attu0/benzene/assets/images/amcl_localization/rviz_particle_filtter.png

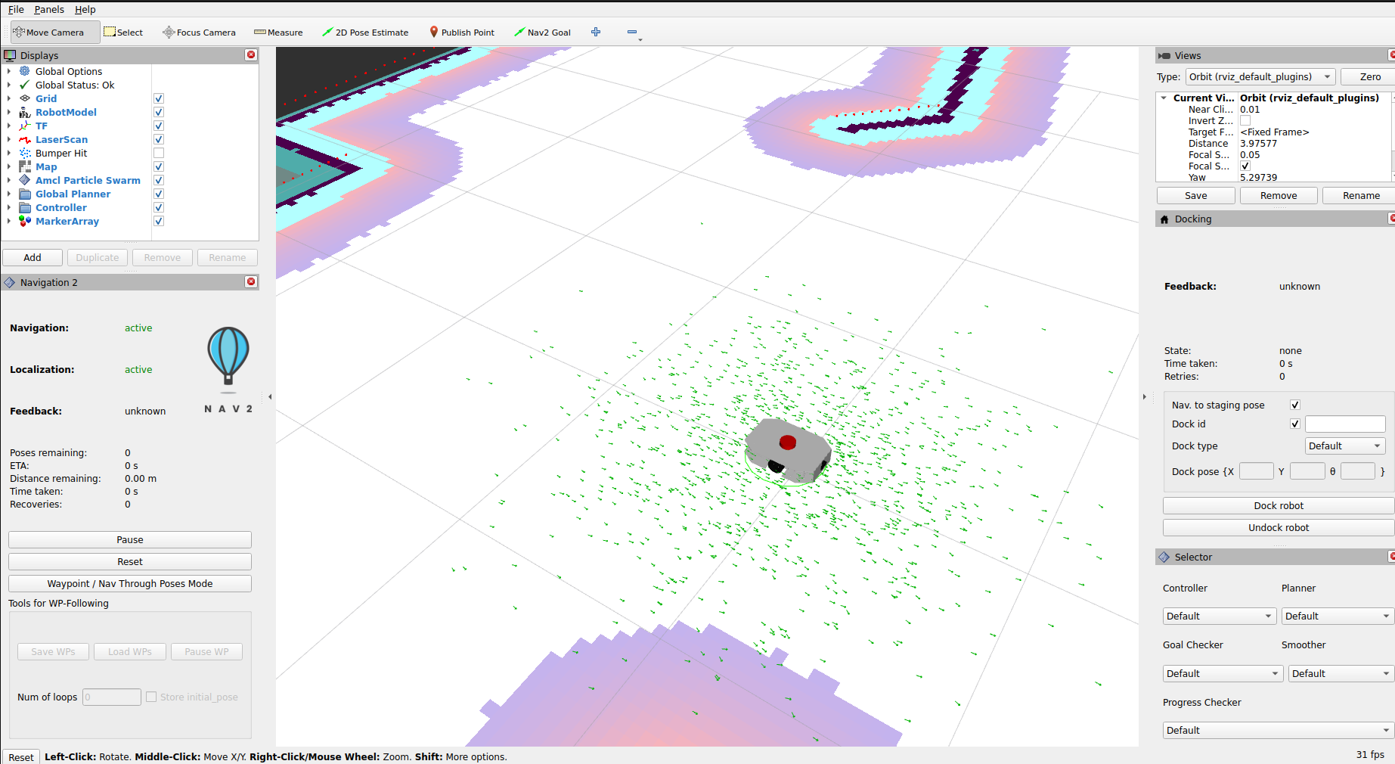
assets/images/amcl_localization/rviz_particle_filtter.png
