attu0/benzene/assets/images/amcl_localization/warehosue_particle.png

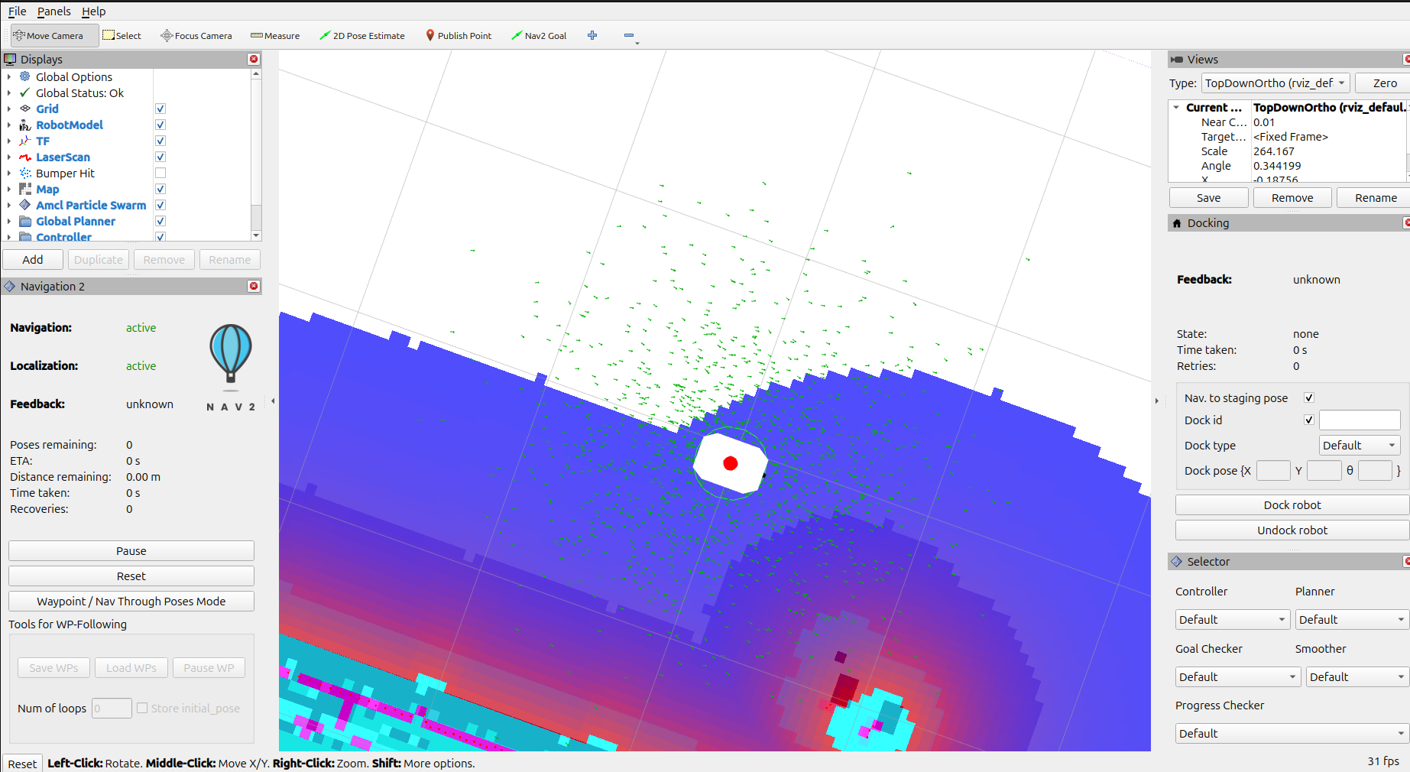
assets/images/amcl_localization/warehosue_particle.png
