attu0/benzene/assets/images/benzene/benzene.png

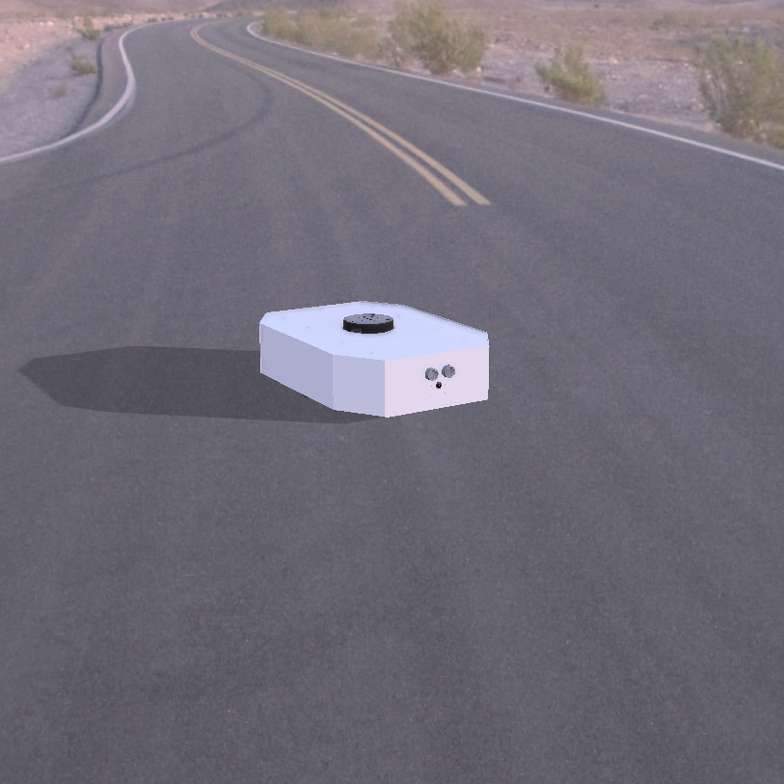
assets/images/benzene/benzene.png
