attu0/benzene/assets/images/benzene/benzene_2.png

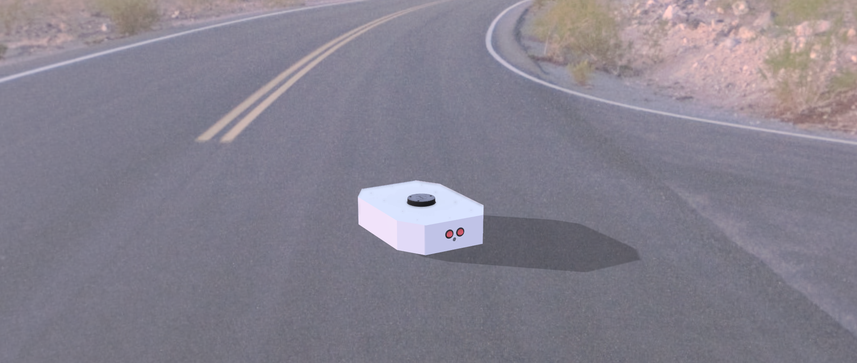
assets/images/benzene/benzene_2.png
