attu0/benzene/assets/images/benzene/benzene_2_back.png

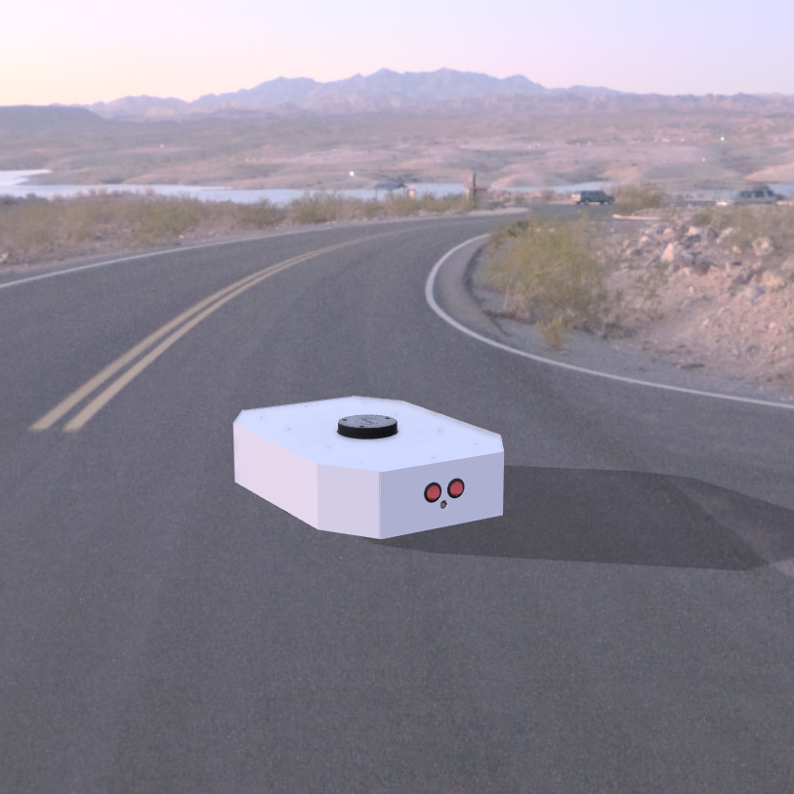
assets/images/benzene/benzene_2_back.png
