attu0/benzene/assets/images/benzene/benzene_2_solid.png

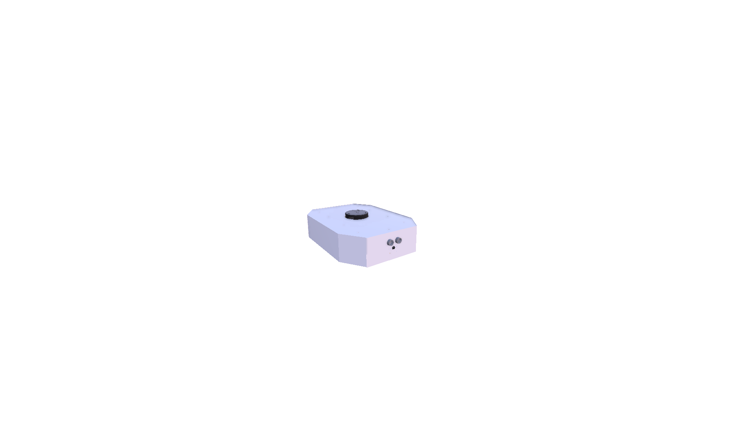
assets/images/benzene/benzene_2_solid.png
