attu0/benzene/assets/images/benzene/urdf_view_in_rviz.png

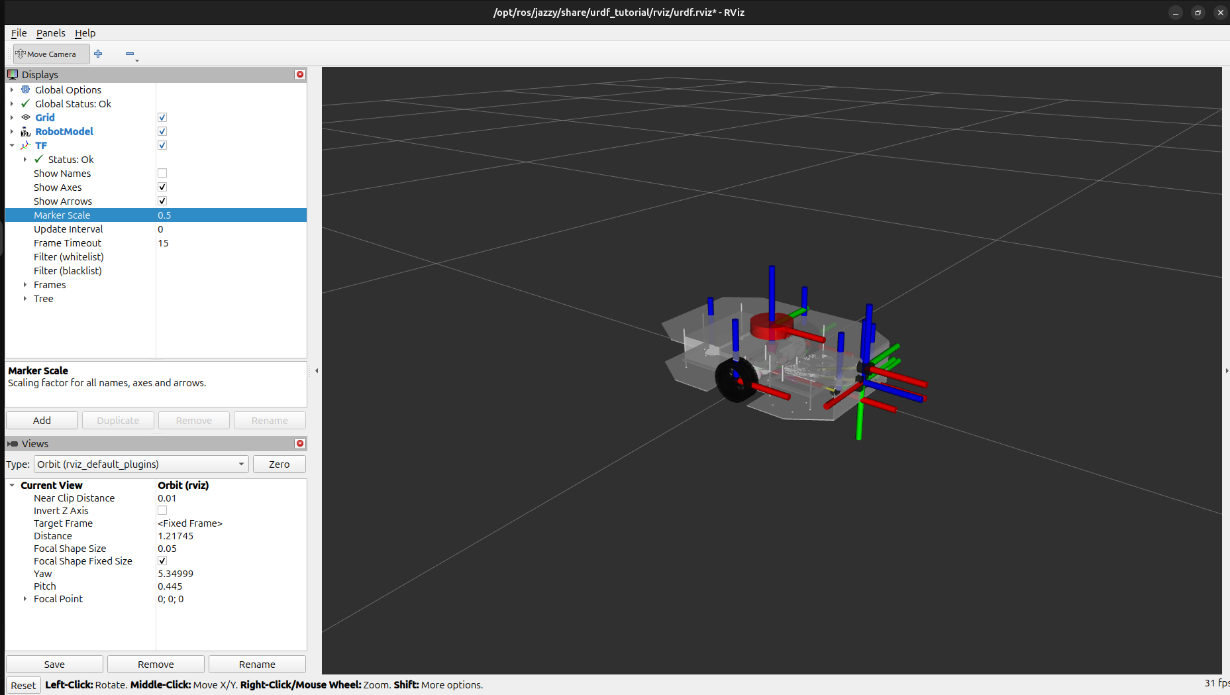
assets/images/benzene/urdf_view_in_rviz.png
