attu0/benzene/assets/images/circuit/arduino.png

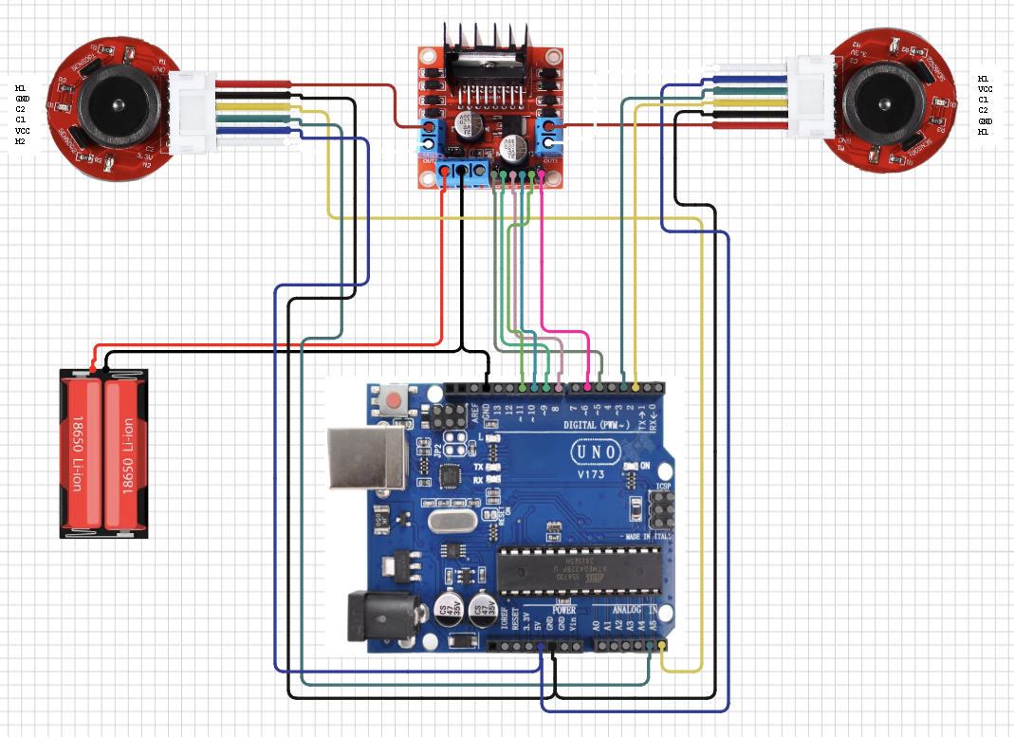
assets/images/circuit/arduino.png
