attu0/benzene/assets/images/circuit/complete_circuit.png

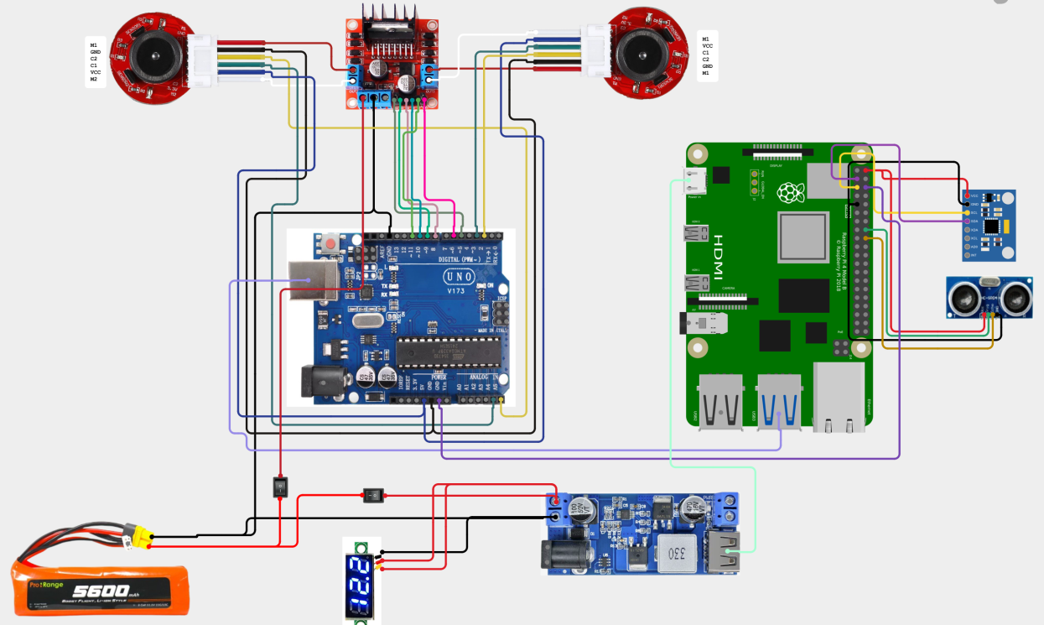
assets/images/circuit/complete_circuit.png
