attu0/benzene/assets/images/circuit/flow.jpg

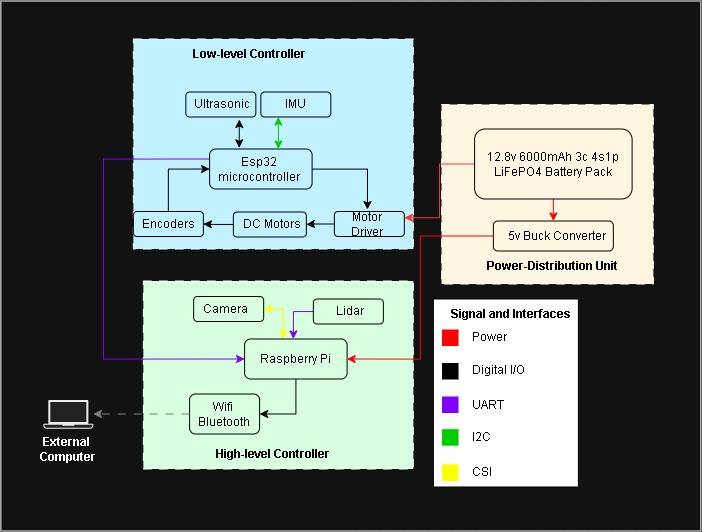
assets/images/circuit/flow.jpg
