attu0/benzene/assets/images/circuit/pi.png

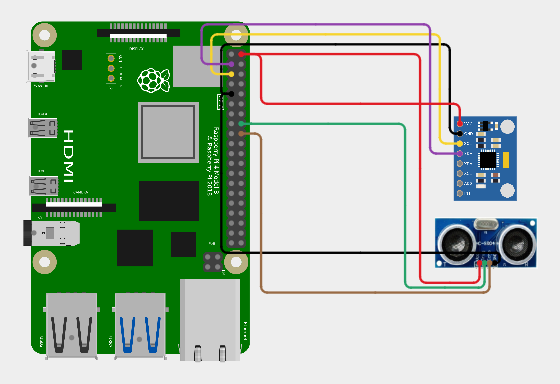
assets/images/circuit/pi.png
