attu0/benzene/assets/images/dagger/line_detection.png

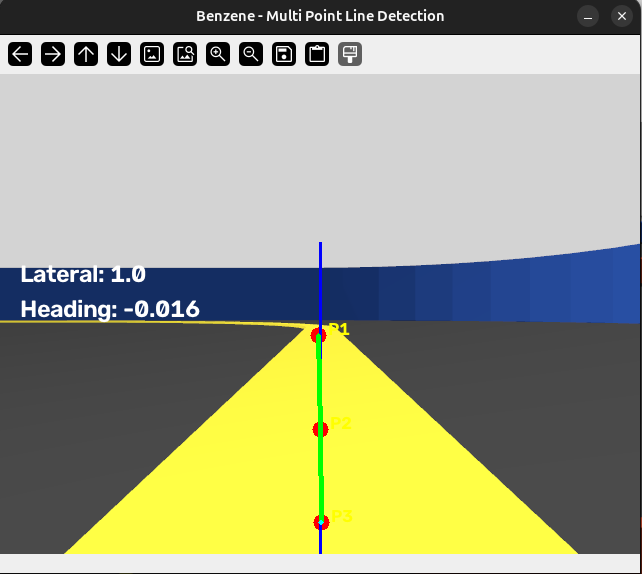
assets/images/dagger/line_detection.png
