attu0/benzene/assets/images/dagger/masking.png

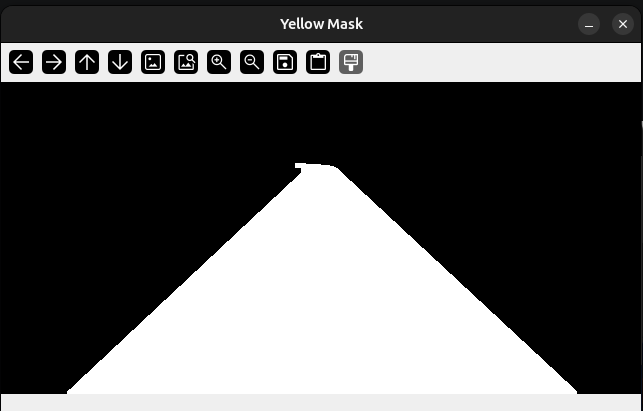
assets/images/dagger/masking.png
