attu0/benzene/assets/images/dagger/rviz2.png

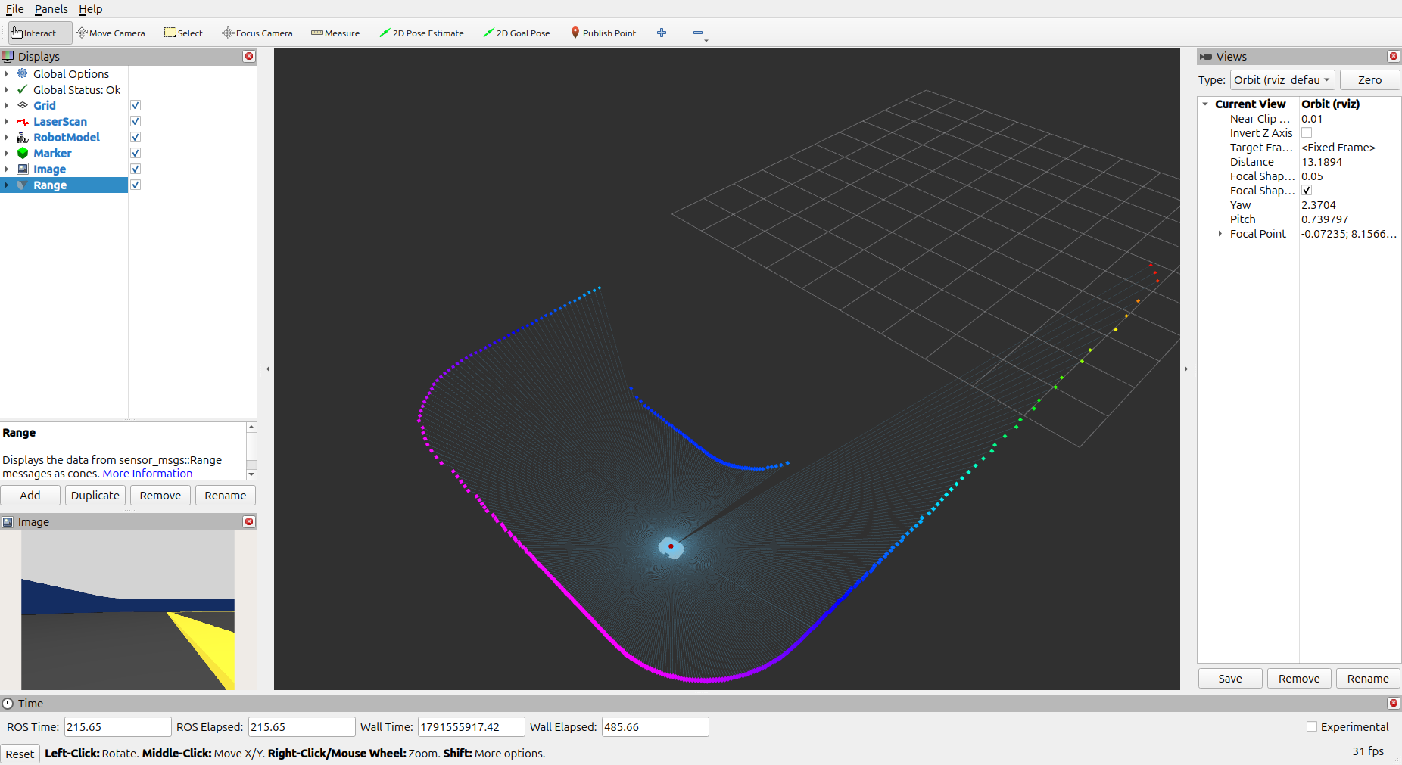
assets/images/dagger/rviz2.png
