attu0/benzene/assets/images/dagger/rviz.png

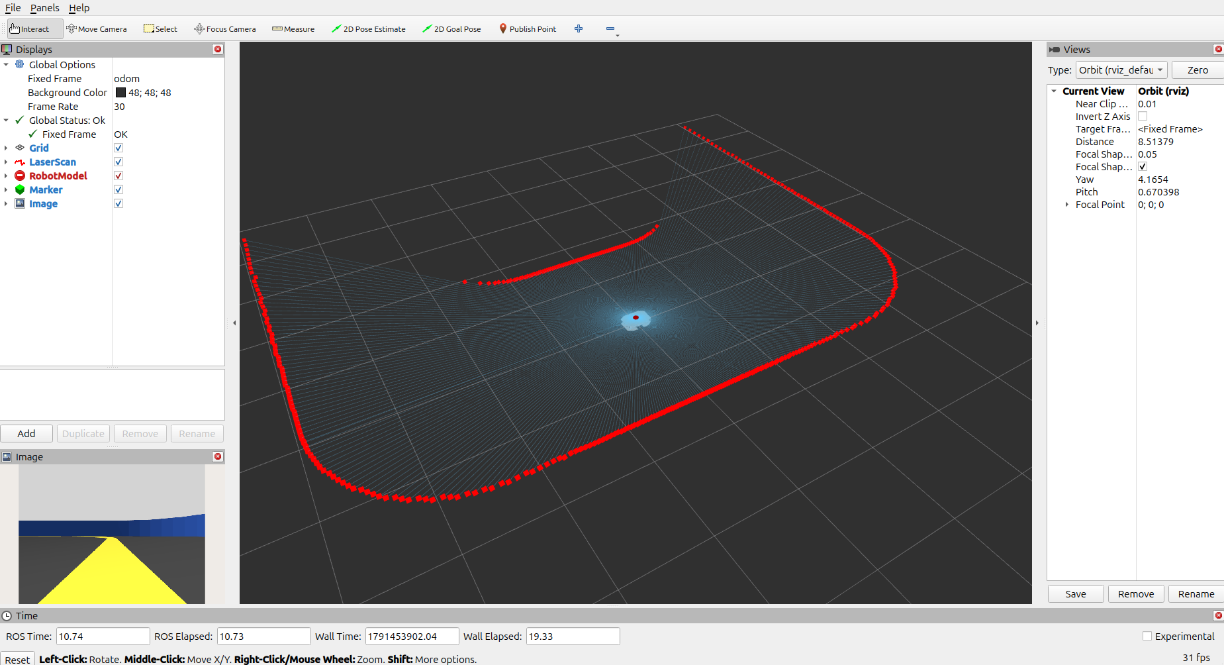
assets/images/dagger/rviz.png
