attu0/benzene/assets/images/dagger/world.png

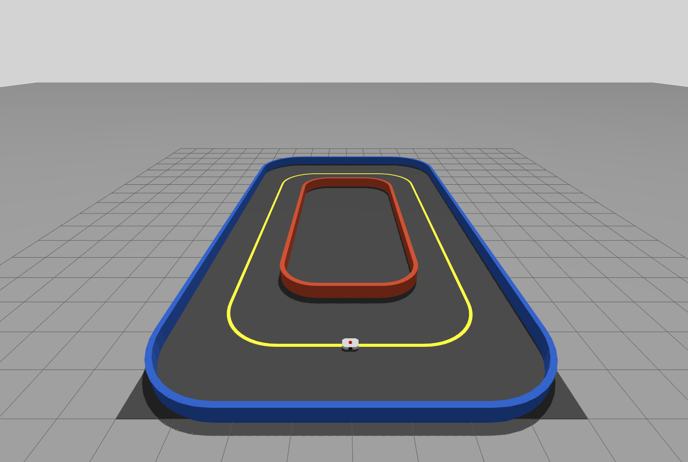
assets/images/dagger/world.png
