attu0/benzene/assets/images/docking/april_tag_align.png

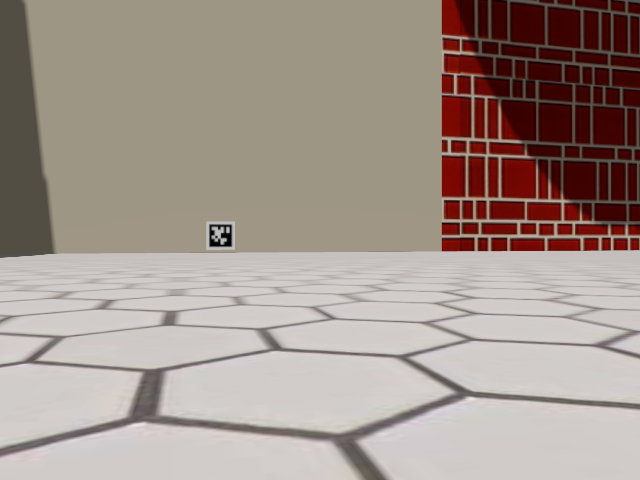
assets/images/docking/april_tag_align.png
