attu0/benzene/assets/images/docking/bot_view.png

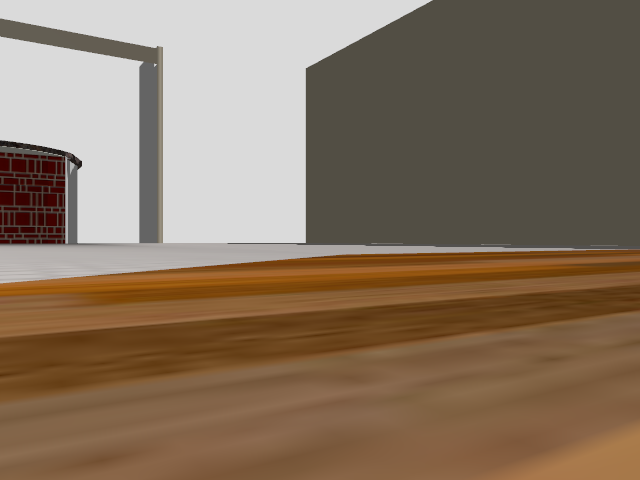
assets/images/docking/bot_view.png
