attu0/benzene/assets/images/docking/docking.png

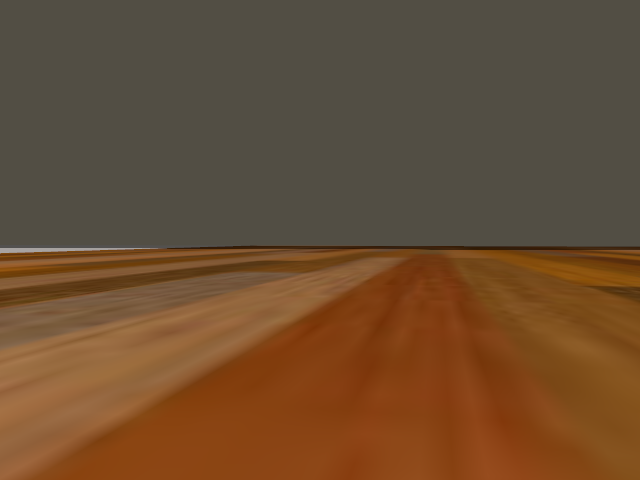
assets/images/docking/docking.png
