attu0/benzene/assets/images/docking/finding_april_tag.png

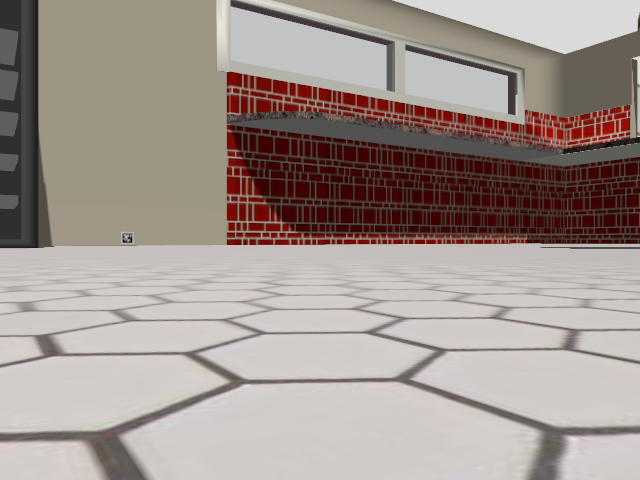
assets/images/docking/finding_april_tag.png
