attu0/benzene/assets/images/docking/gz1.png

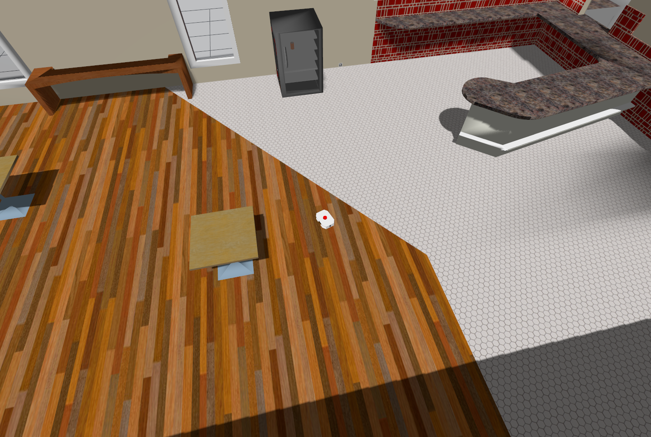
assets/images/docking/gz1.png
