attu0/benzene/assets/images/docking/gz2.png

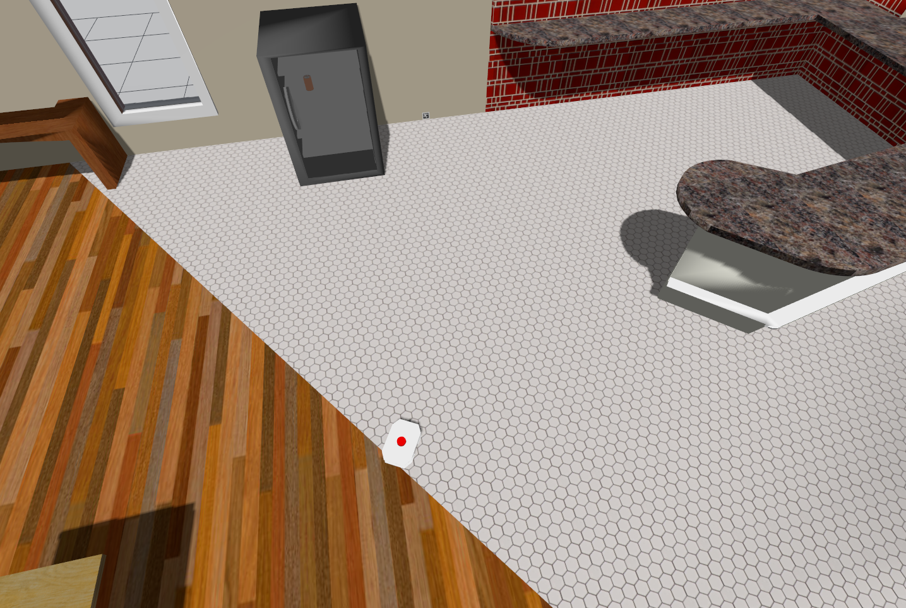
assets/images/docking/gz2.png
