attu0/benzene/assets/images/docking/gz3.png

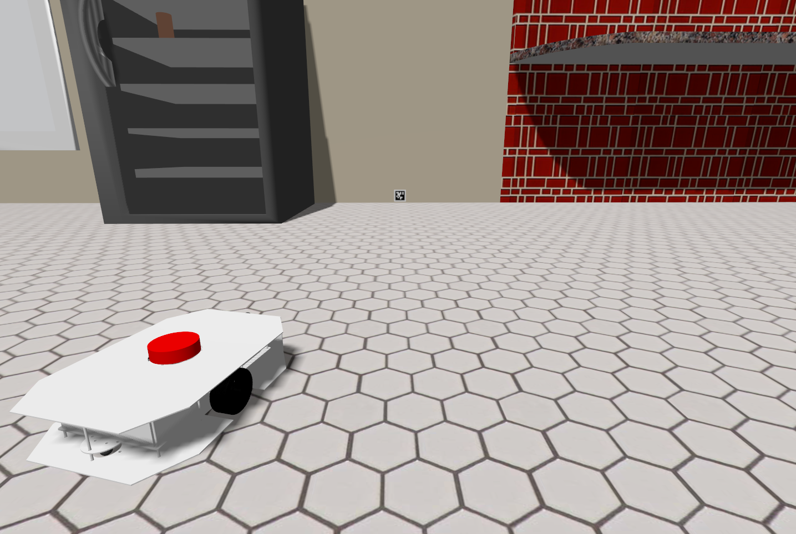
assets/images/docking/gz3.png
