attu0/benzene/assets/images/docking/gz4.png

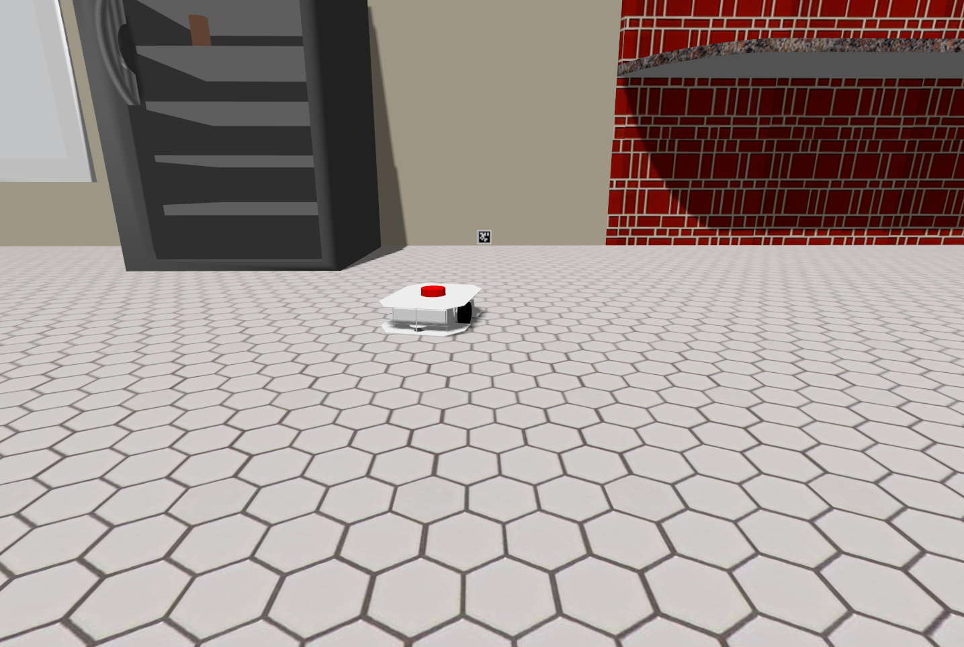
assets/images/docking/gz4.png
