attu0/benzene/assets/images/docking/image.png

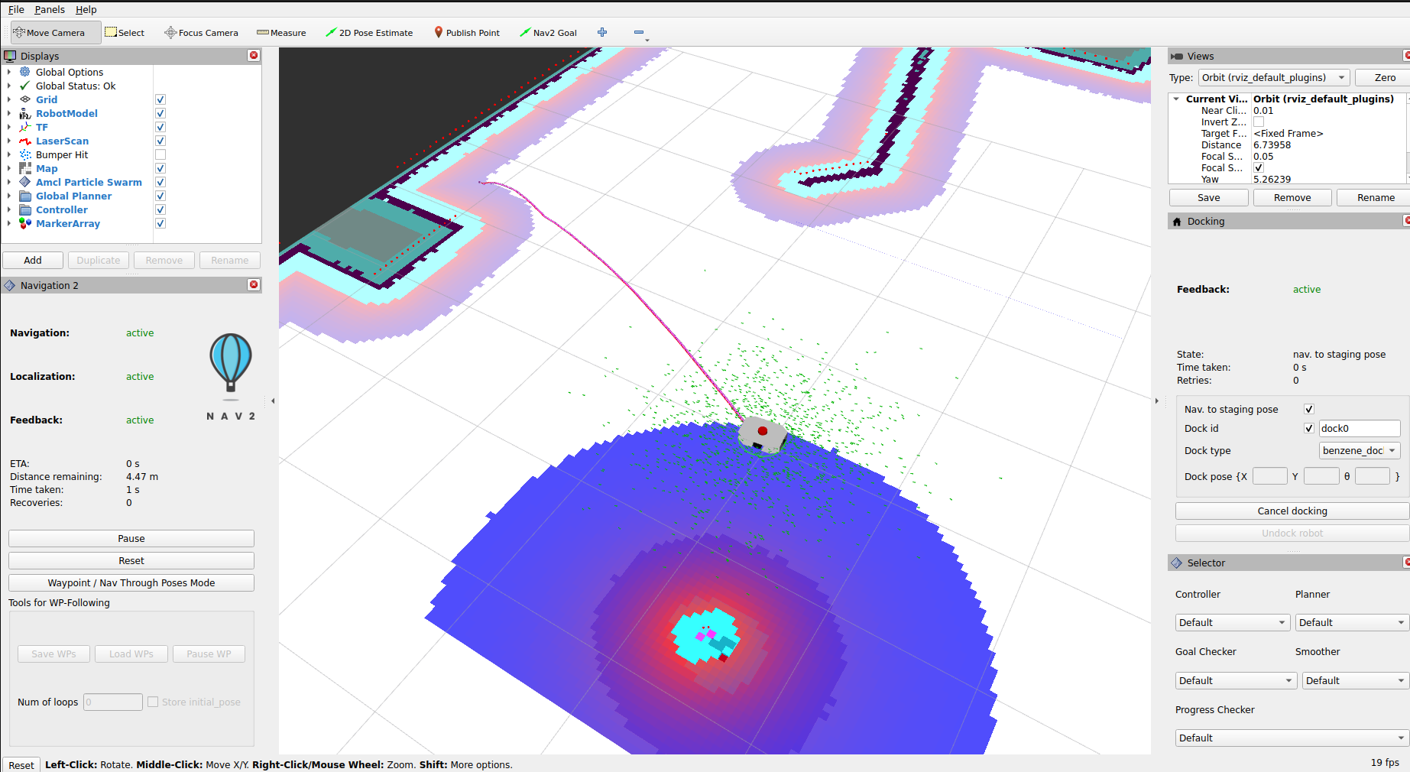
assets/images/docking/image.png
