attu0/benzene/assets/images/docking/reached.png

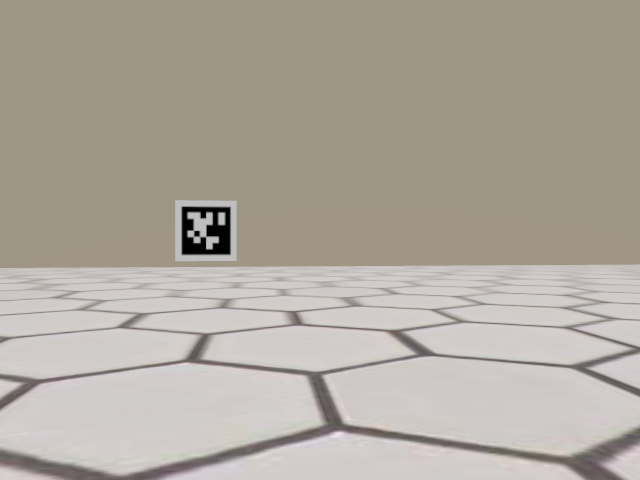
assets/images/docking/reached.png
