attu0/benzene/assets/images/laser_cut/base_plate.jpg

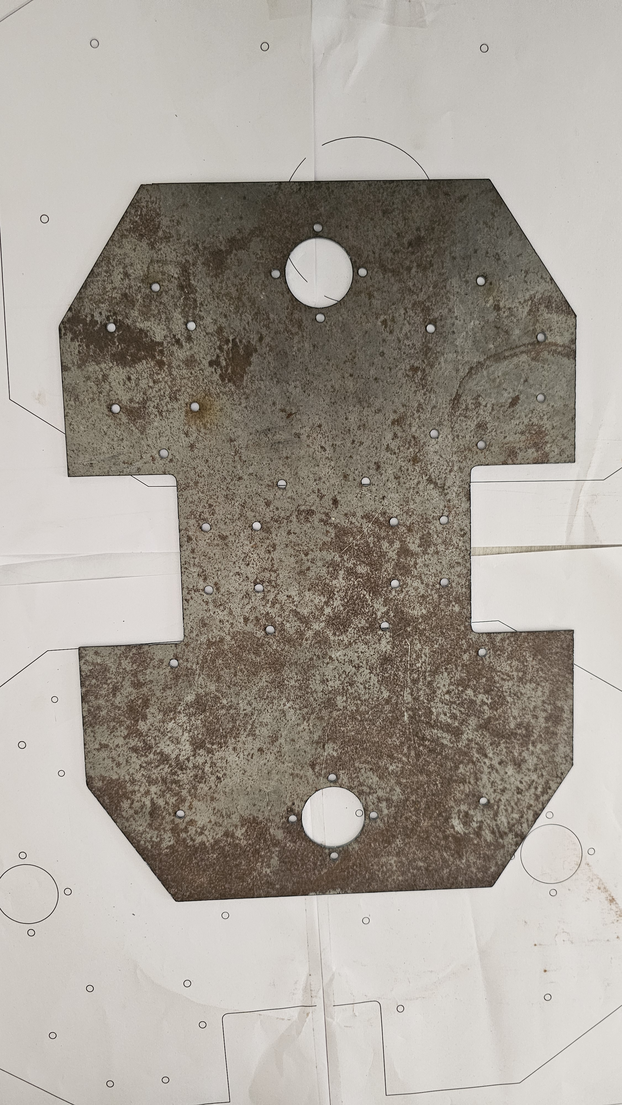
assets/images/laser_cut/base_plate.jpg
