attu0/benzene/assets/images/laser_cut/caster_plates.jpg

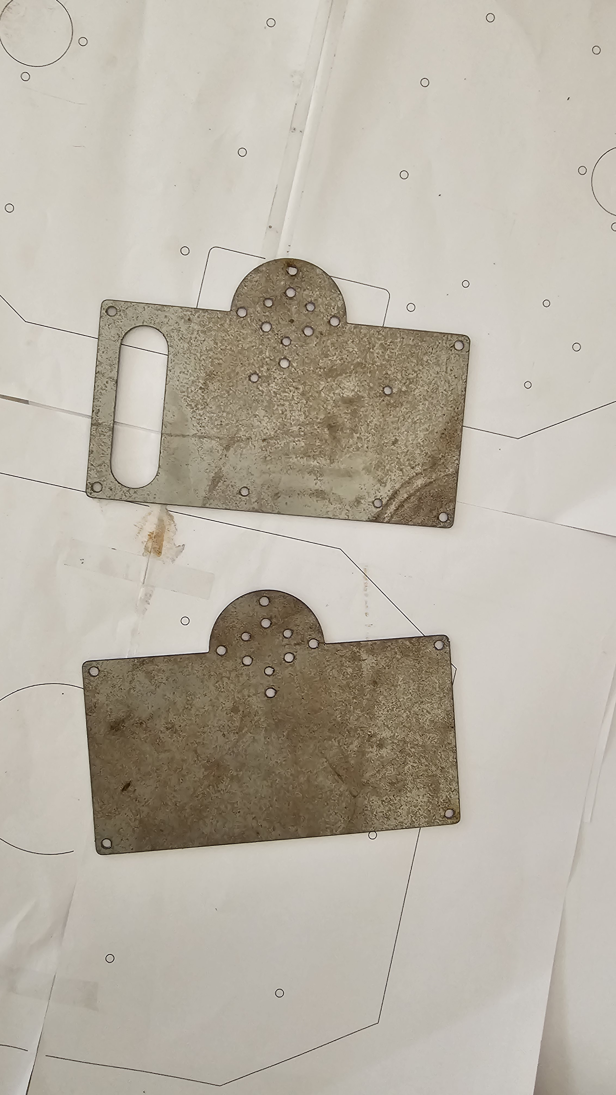
assets/images/laser_cut/caster_plates.jpg
