attu0/benzene/assets/images/laser_cut/corner_panels.jpg

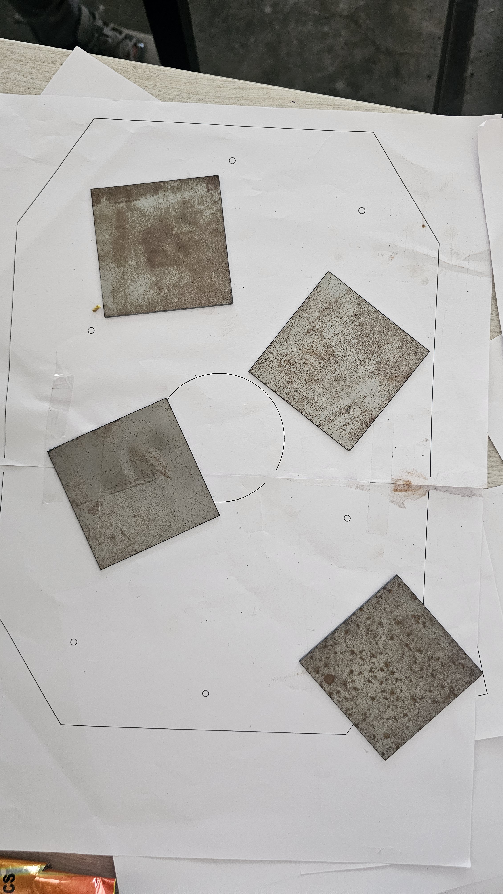
assets/images/laser_cut/corner_panels.jpg
