attu0/benzene/assets/images/laser_cut/fro_rear_plates.jpg

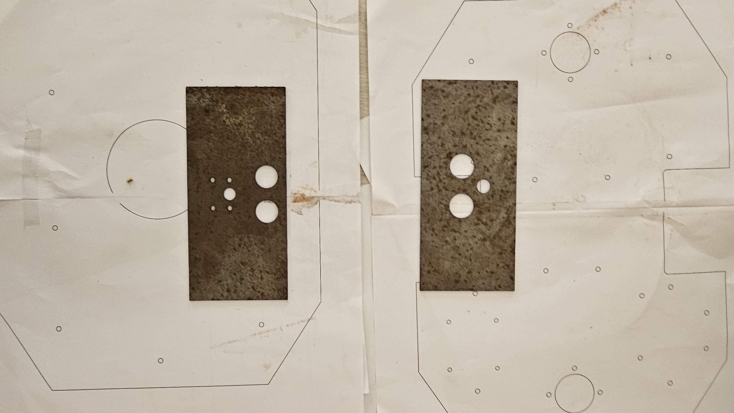
assets/images/laser_cut/fro_rear_plates.jpg
