attu0/benzene/assets/images/laser_cut/side_plates.jpg

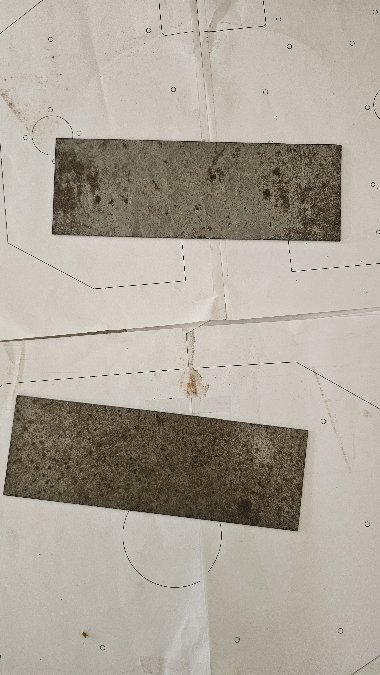
assets/images/laser_cut/side_plates.jpg
