attu0/benzene/assets/images/laser_cut/top_plate.jpg

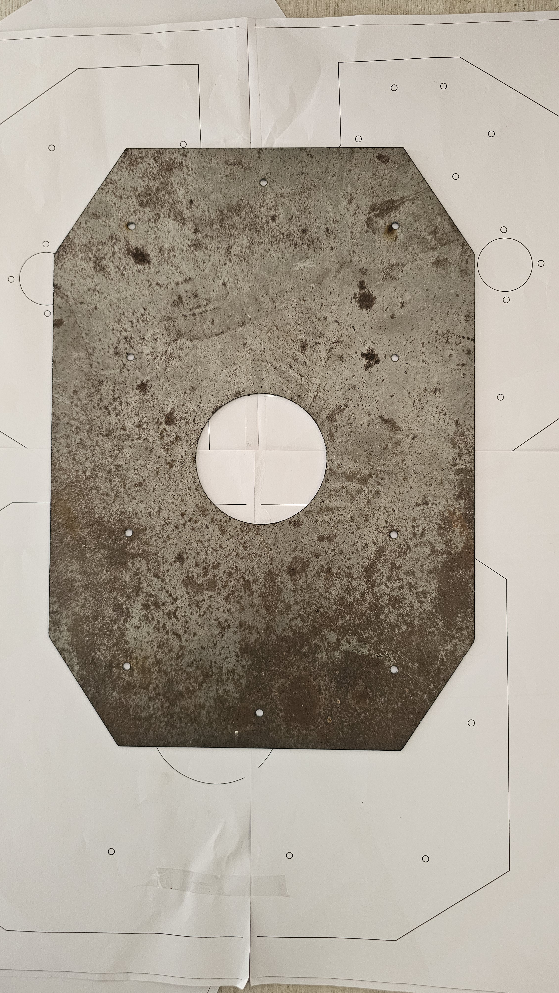
assets/images/laser_cut/top_plate.jpg
