attu0/benzene/assets/images/maps/cafe.png

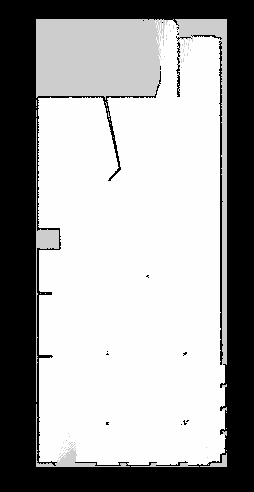
assets/images/maps/cafe.png
