attu0/benzene/assets/images/maps/office.png

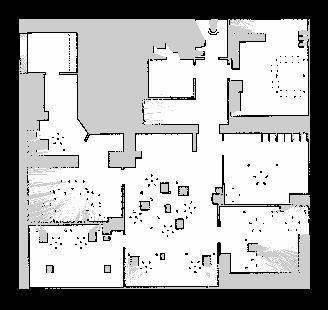
assets/images/maps/office.png
