attu0/benzene/assets/images/maps/warehouse.png

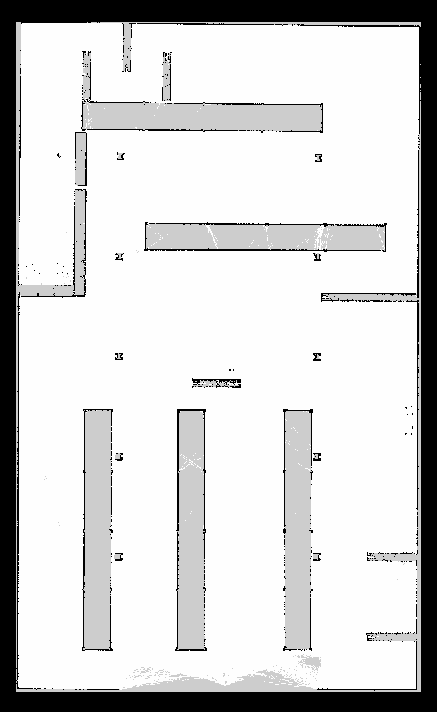
assets/images/maps/warehouse.png
