attu0/benzene/assets/images/nav2/gz_cafe.png

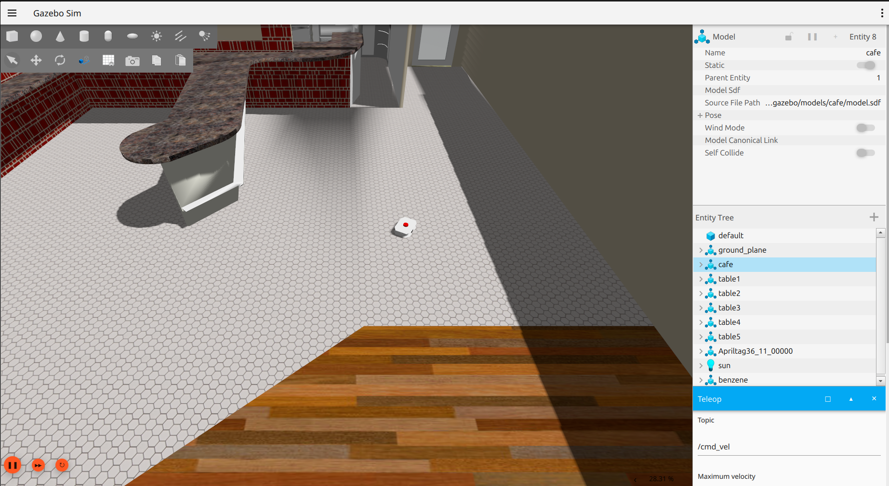
assets/images/nav2/gz_cafe.png
