attu0/benzene/assets/images/nav2/gz_warehouse.png

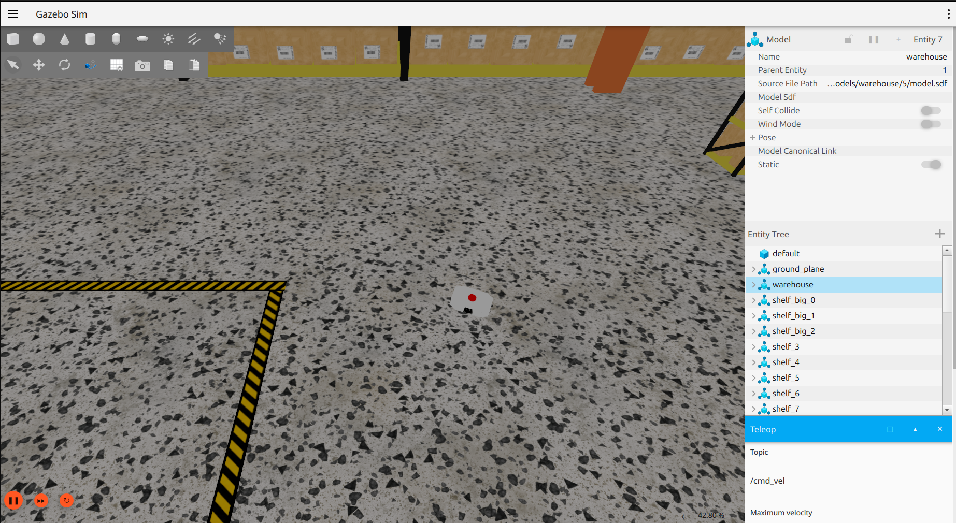
assets/images/nav2/gz_warehouse.png
