attu0/benzene/assets/images/nav2/rviz_cafe.png

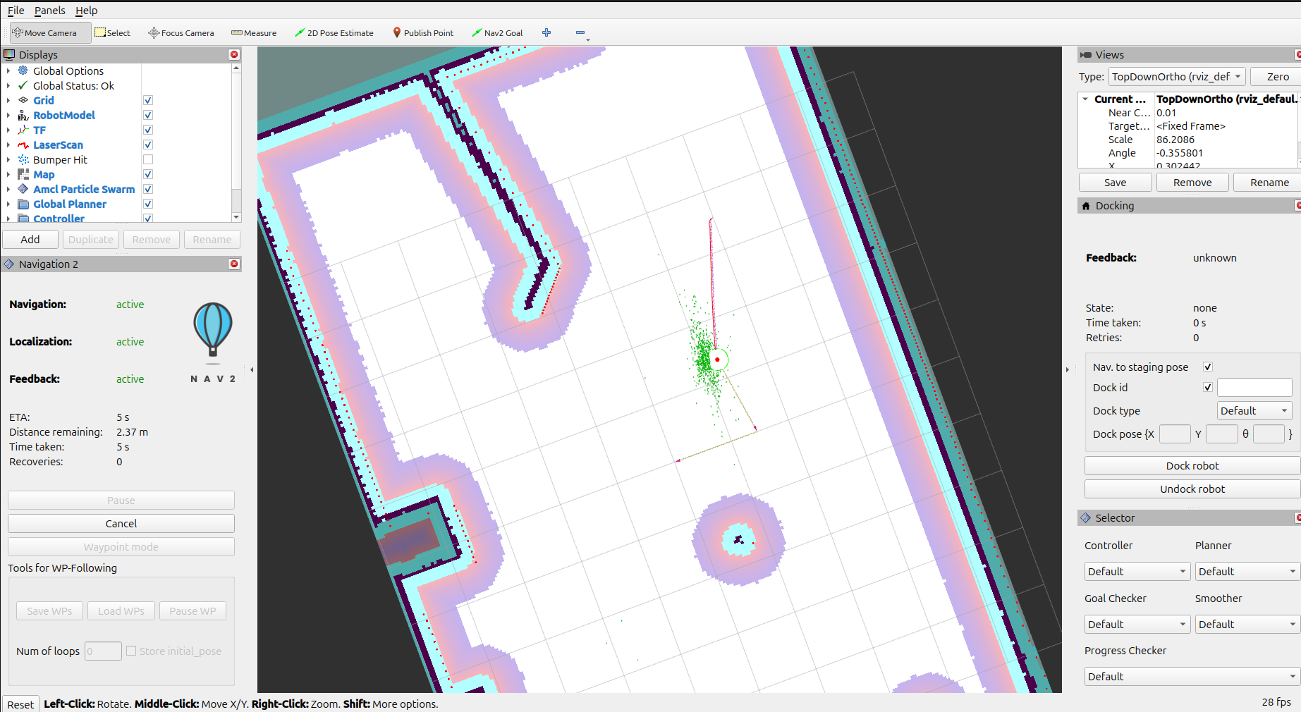
assets/images/nav2/rviz_cafe.png
