attu0/benzene/assets/images/nav2/rviz_office2.png

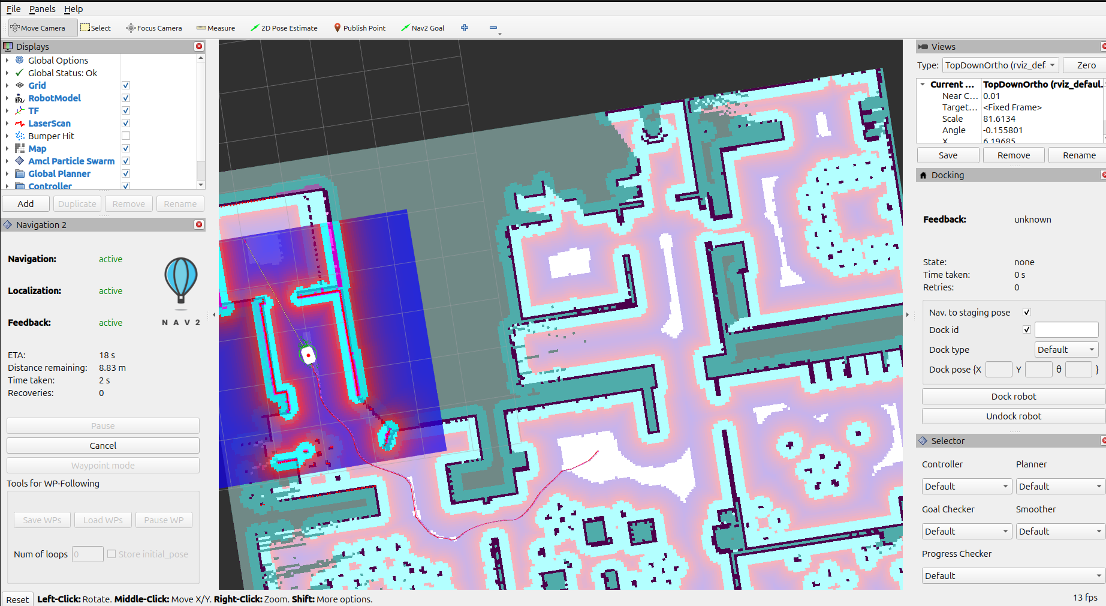
assets/images/nav2/rviz_office2.png
