attu0/benzene/assets/images/nav2/rviz_office.png

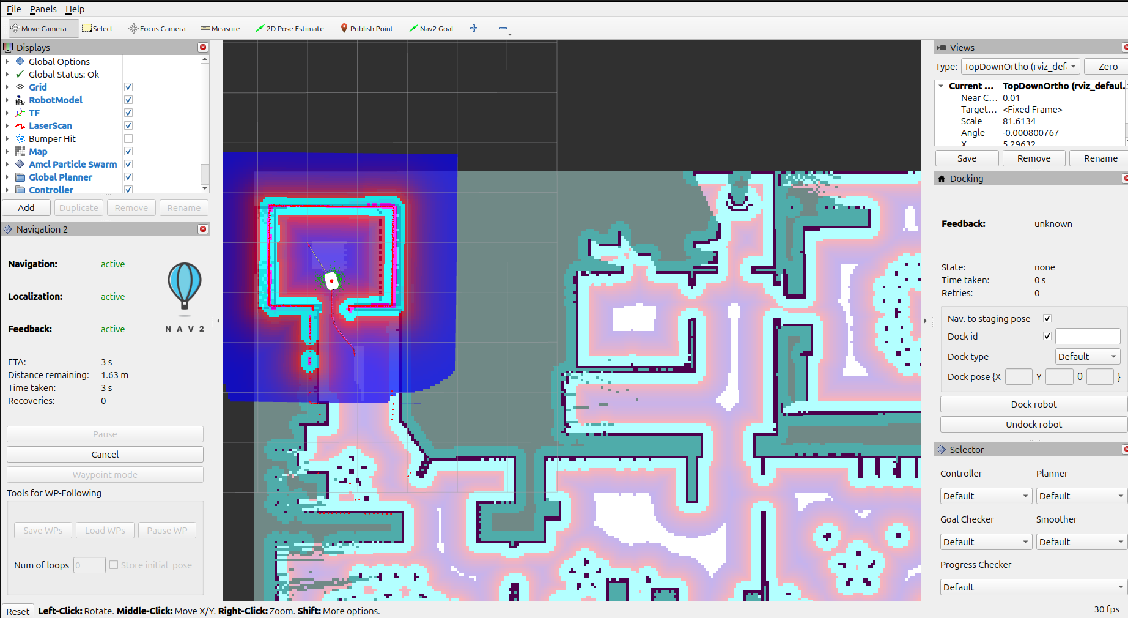
assets/images/nav2/rviz_office.png
