attu0/benzene/assets/images/nav2/rviz_warehosue.png

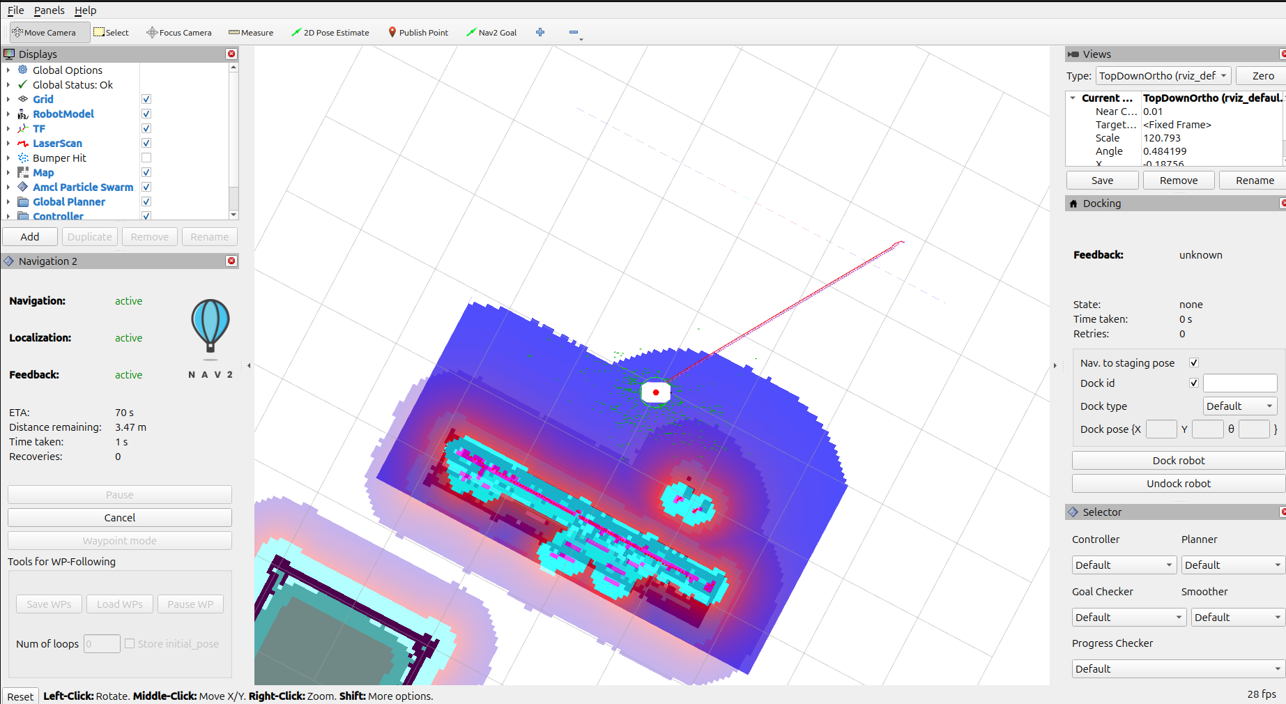
assets/images/nav2/rviz_warehosue.png
