attu0/benzene/assets/images/real_bot/benzene.jpeg

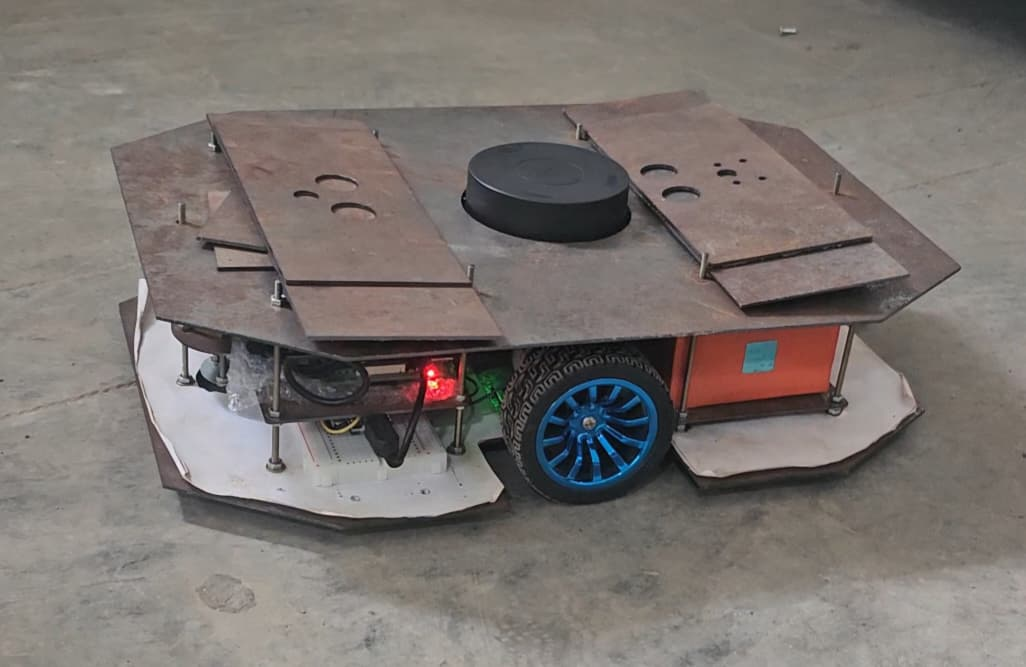
assets/images/real_bot/benzene.jpeg
