attu0/benzene/assets/images/real_bot/ckt_named.png

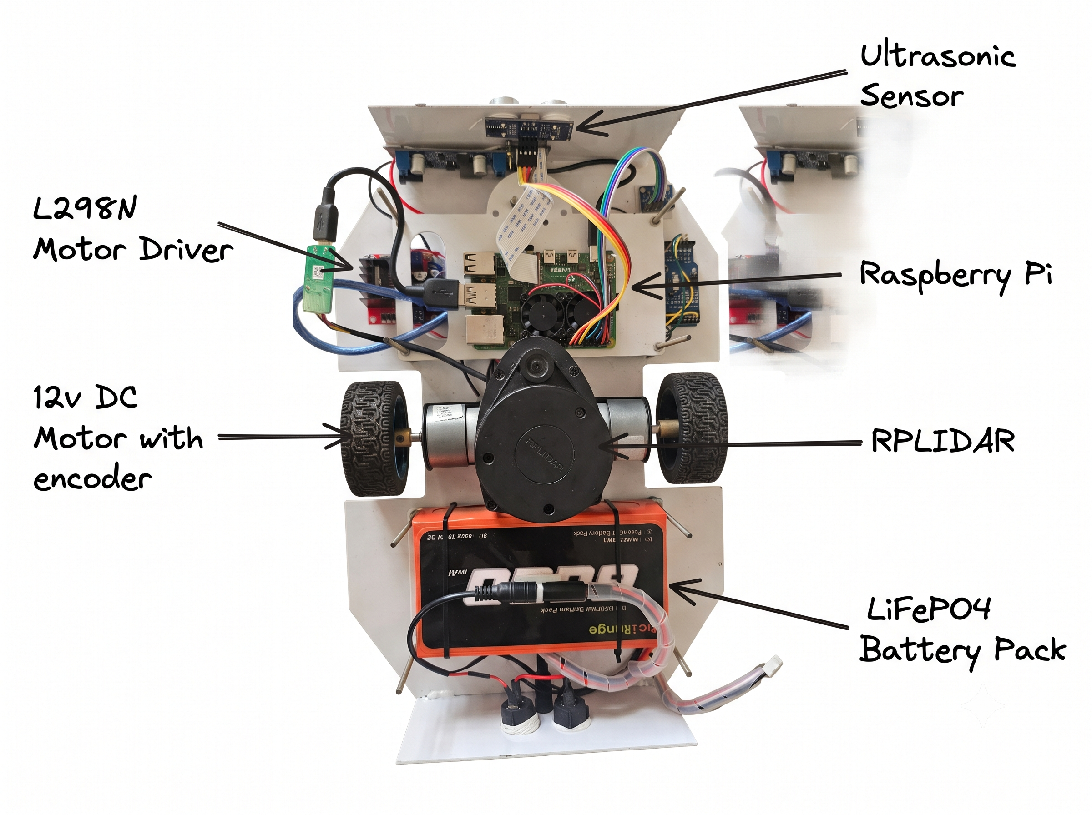
assets/images/real_bot/ckt_named.png
