attu0/benzene/assets/images/real_bot/front1.jpg

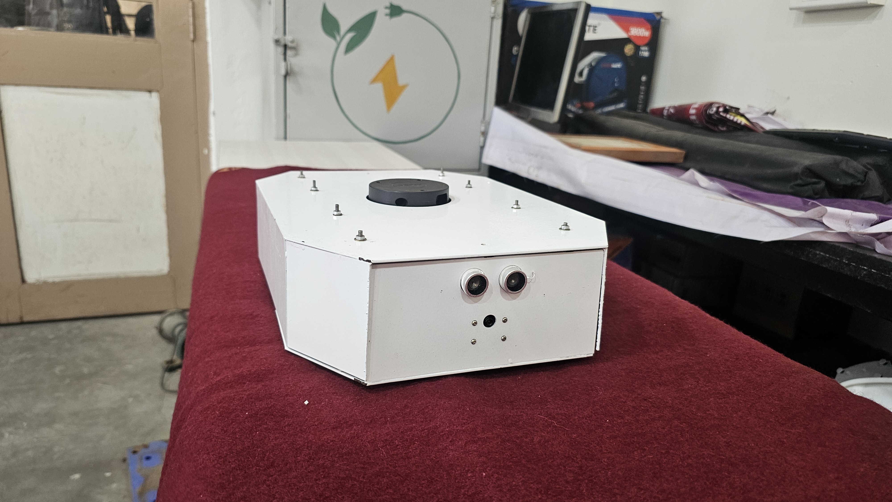
assets/images/real_bot/front1.jpg
