attu0/benzene/assets/images/real_bot/front2.jpg

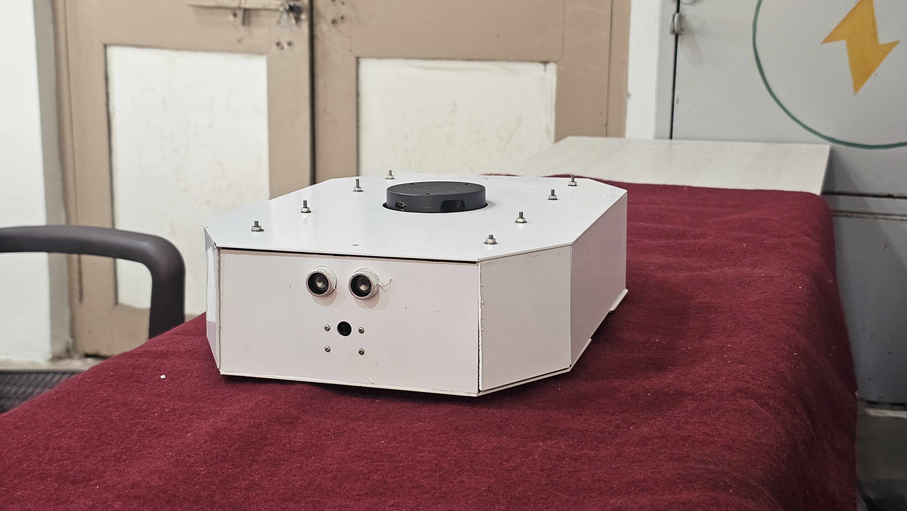
assets/images/real_bot/front2.jpg
