attu0/benzene/assets/images/real_bot/front3.jpg

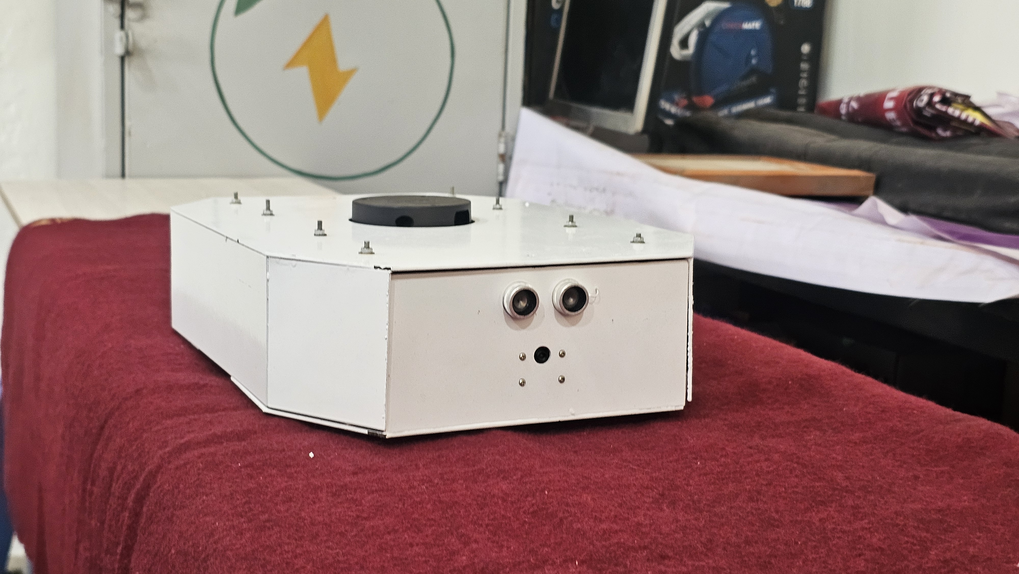
assets/images/real_bot/front3.jpg
