attu0/benzene/assets/images/real_bot/internal.jpg

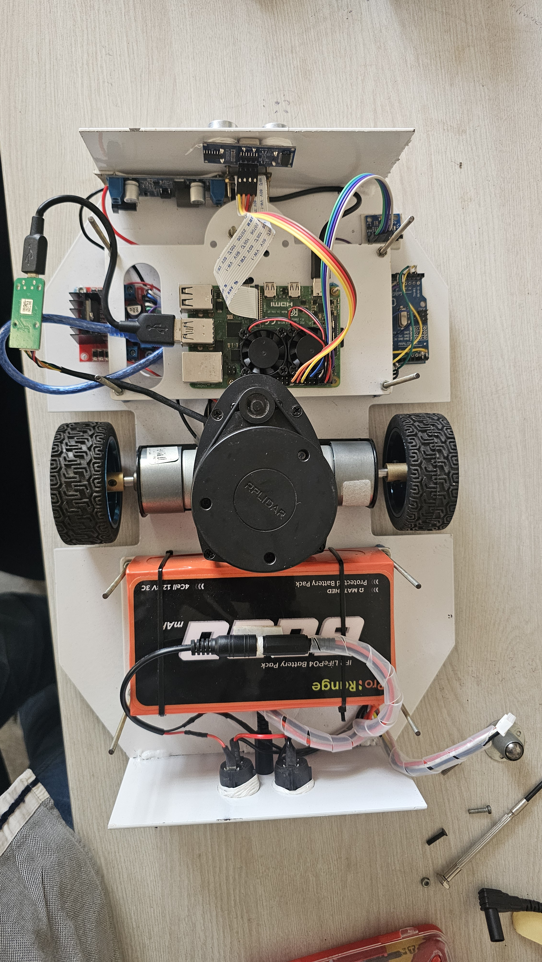
assets/images/real_bot/internal.jpg
