attu0/benzene/assets/images/real_bot/rear1.jpg

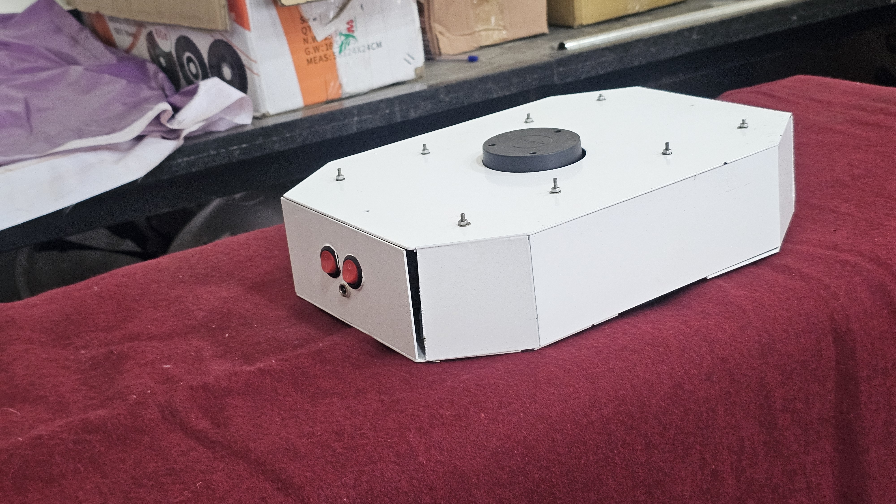
assets/images/real_bot/rear1.jpg
