attu0/benzene/assets/images/real_bot/rear2.jpg

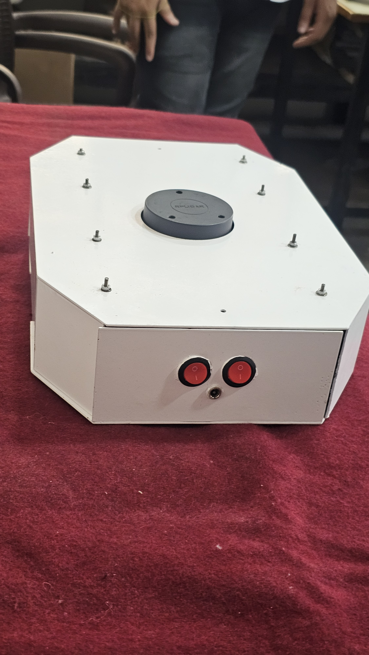
assets/images/real_bot/rear2.jpg
