attu0/benzene/assets/images/self_explore/cafe2.png

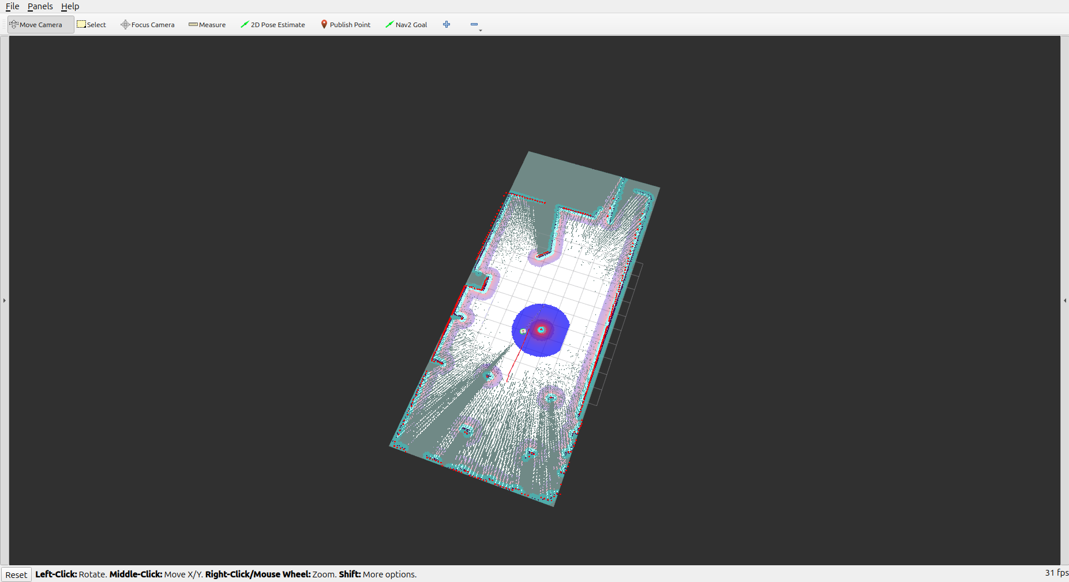
assets/images/self_explore/cafe2.png
