attu0/benzene/assets/images/self_explore/cafe.png

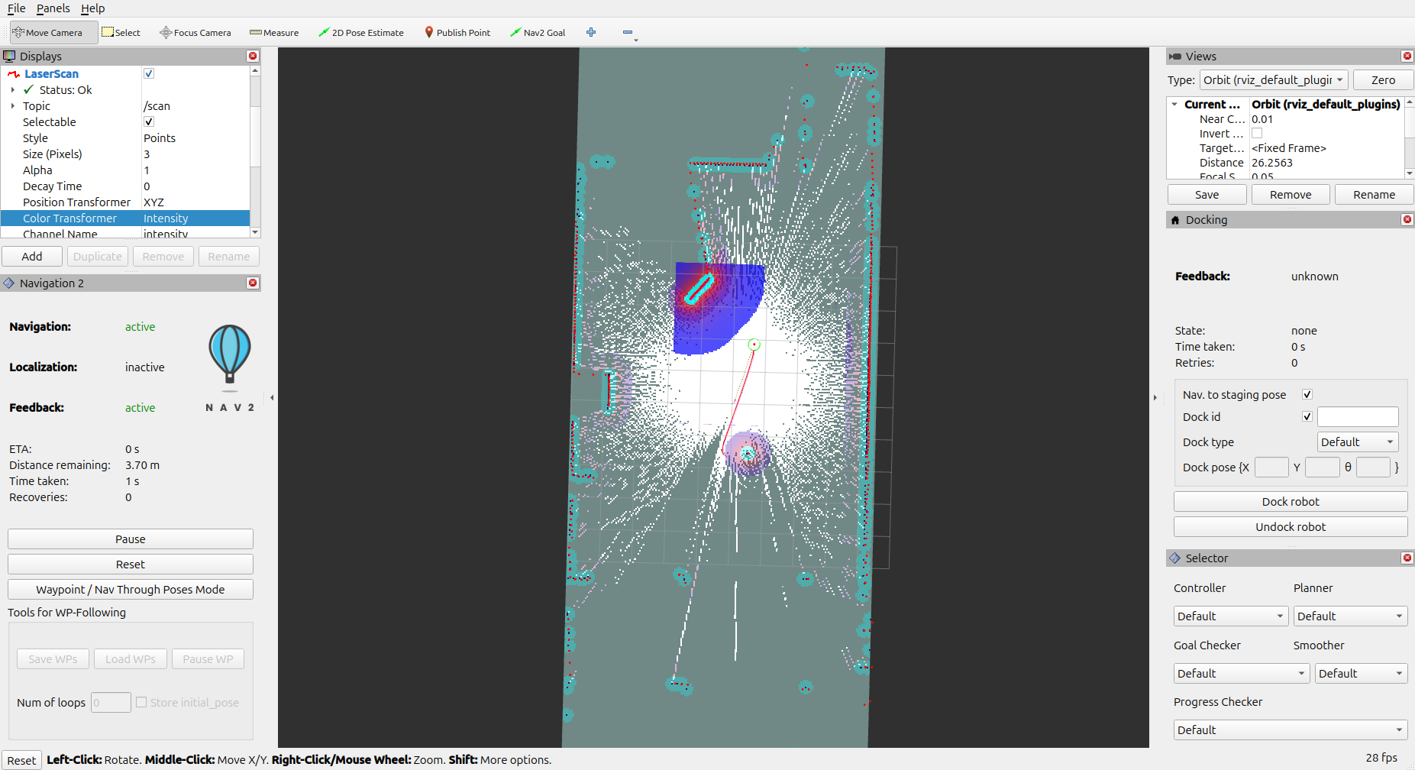
assets/images/self_explore/cafe.png
