attu0/benzene/assets/images/self_explore/office.png

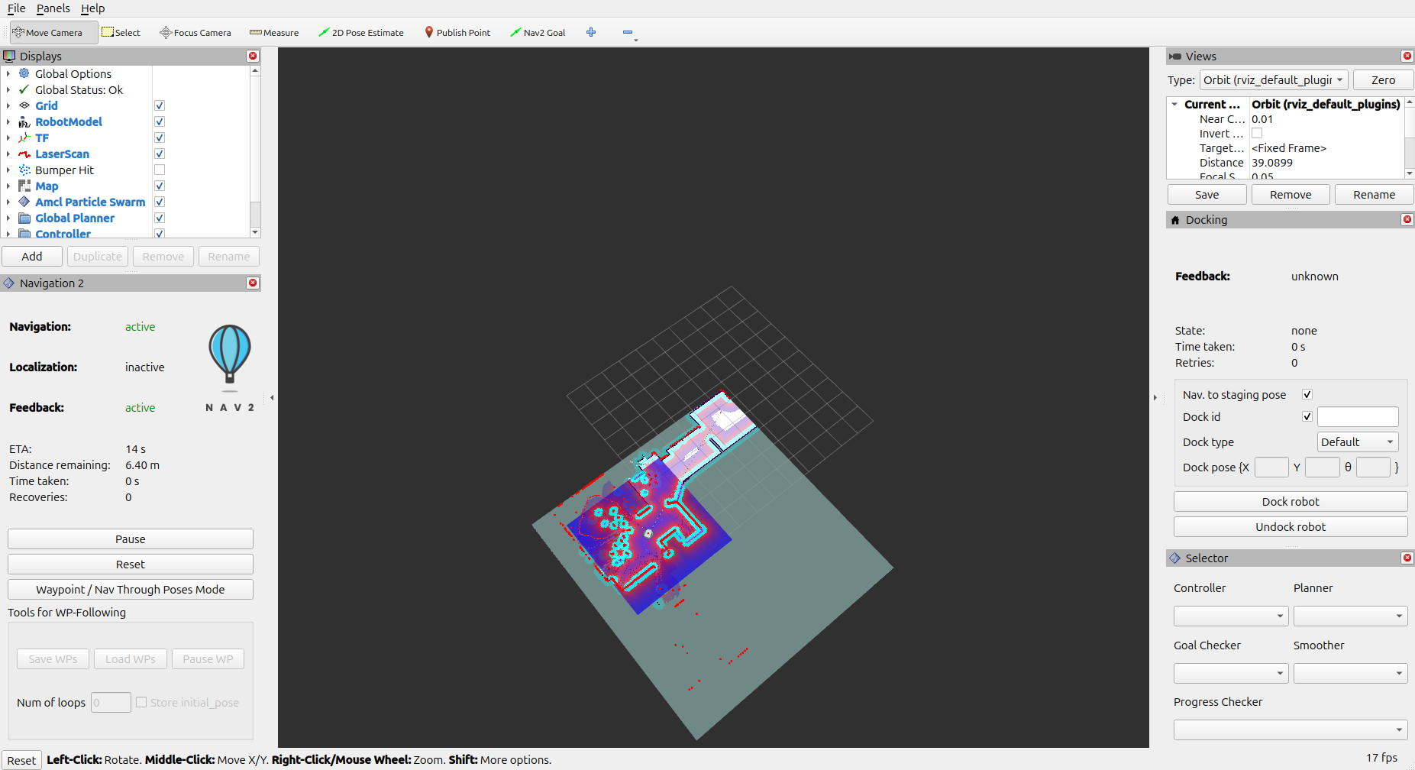
assets/images/self_explore/office.png
