attu0/benzene/assets/images/self_explore/office_gz.png

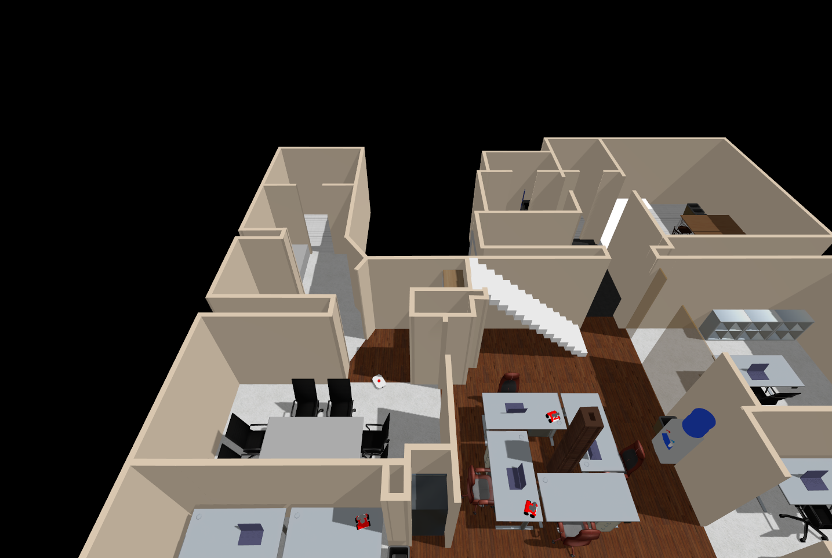
assets/images/self_explore/office_gz.png
