attu0/benzene/assets/images/self_explore/warehosue_gz.png

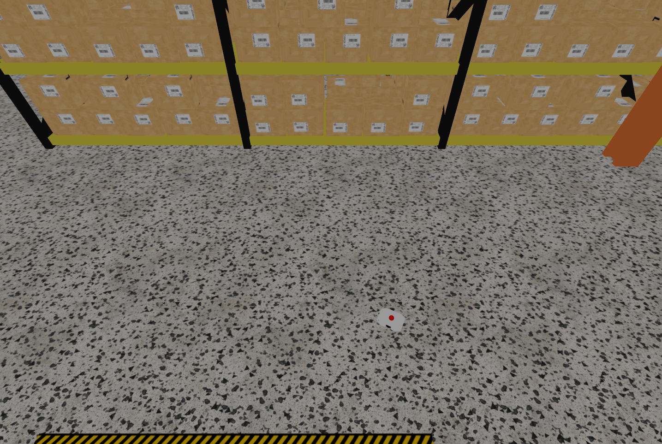
assets/images/self_explore/warehosue_gz.png
