attu0/benzene/assets/images/self_explore/warehouse2.png

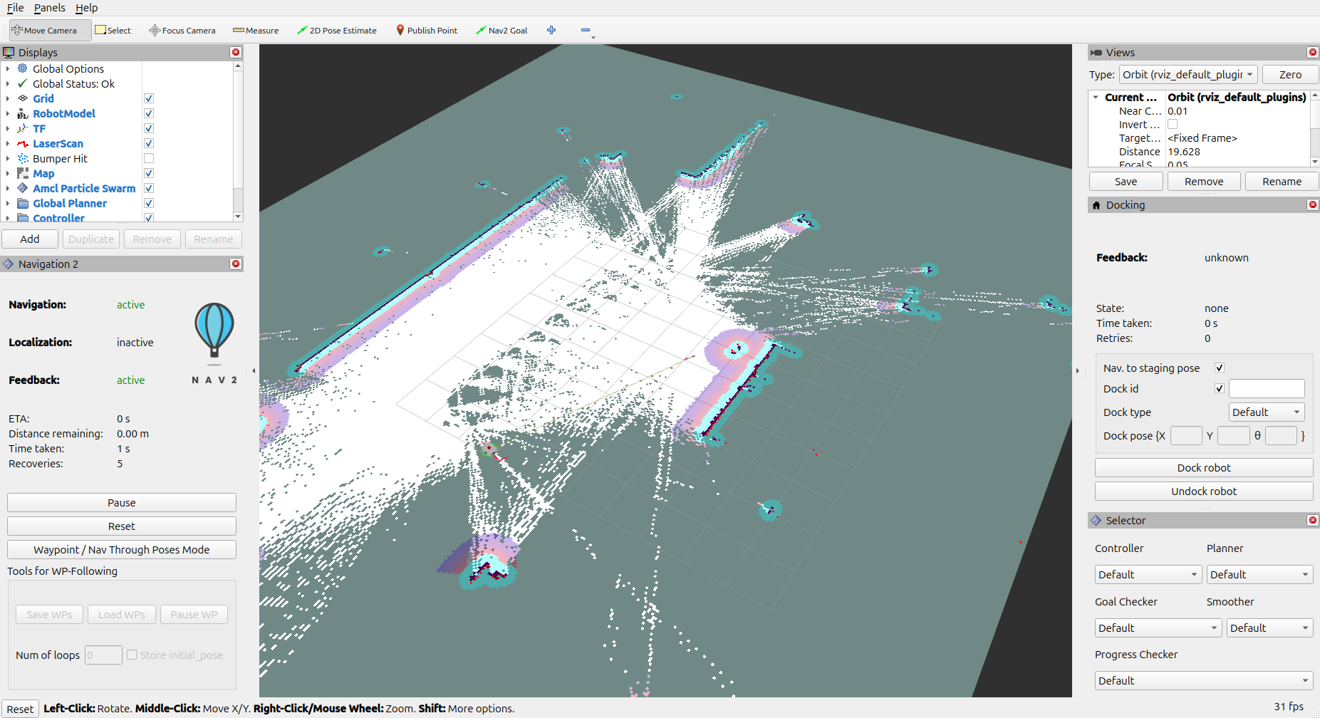
assets/images/self_explore/warehouse2.png
