attu0/benzene/assets/images/self_explore/warehouse.png

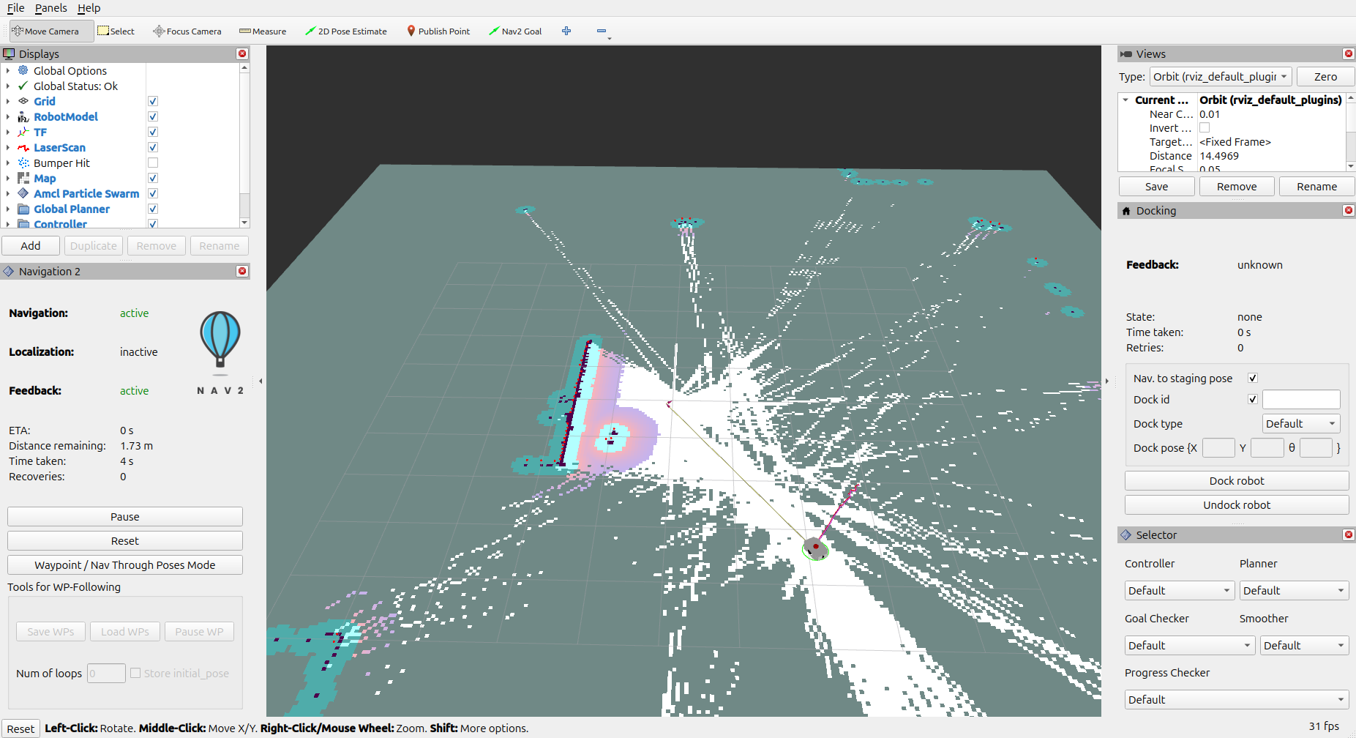
assets/images/self_explore/warehouse.png
