attu0/benzene/assets/images/sensors/ultrasonic_sim.png

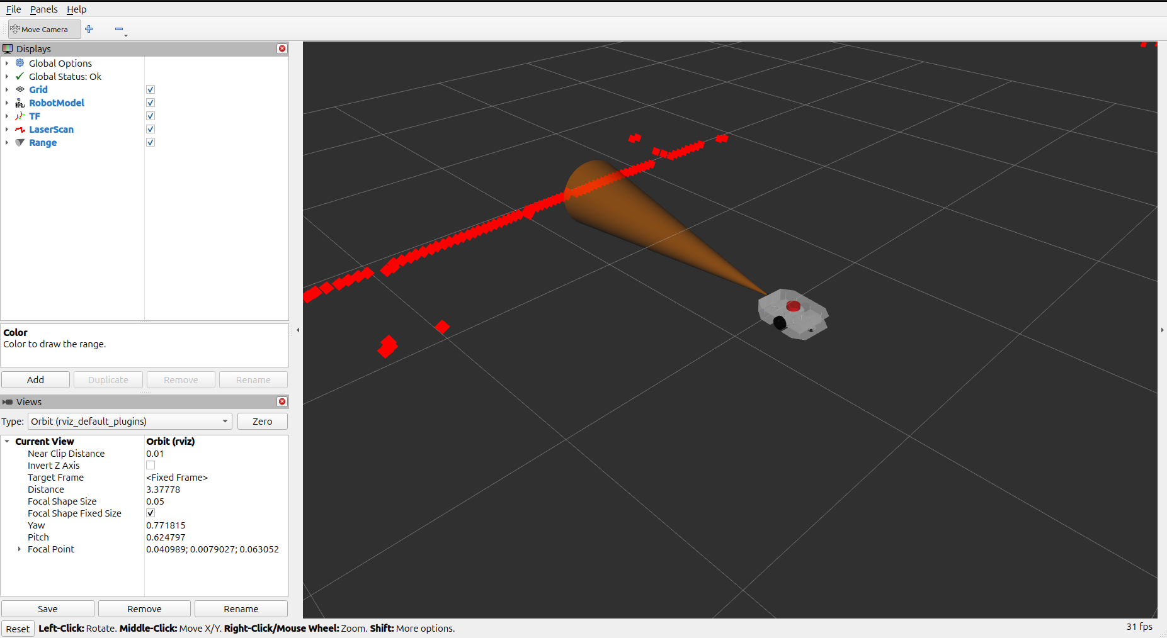
assets/images/sensors/ultrasonic_sim.png
