attu0/benzene/assets/images/slam/cafe.png

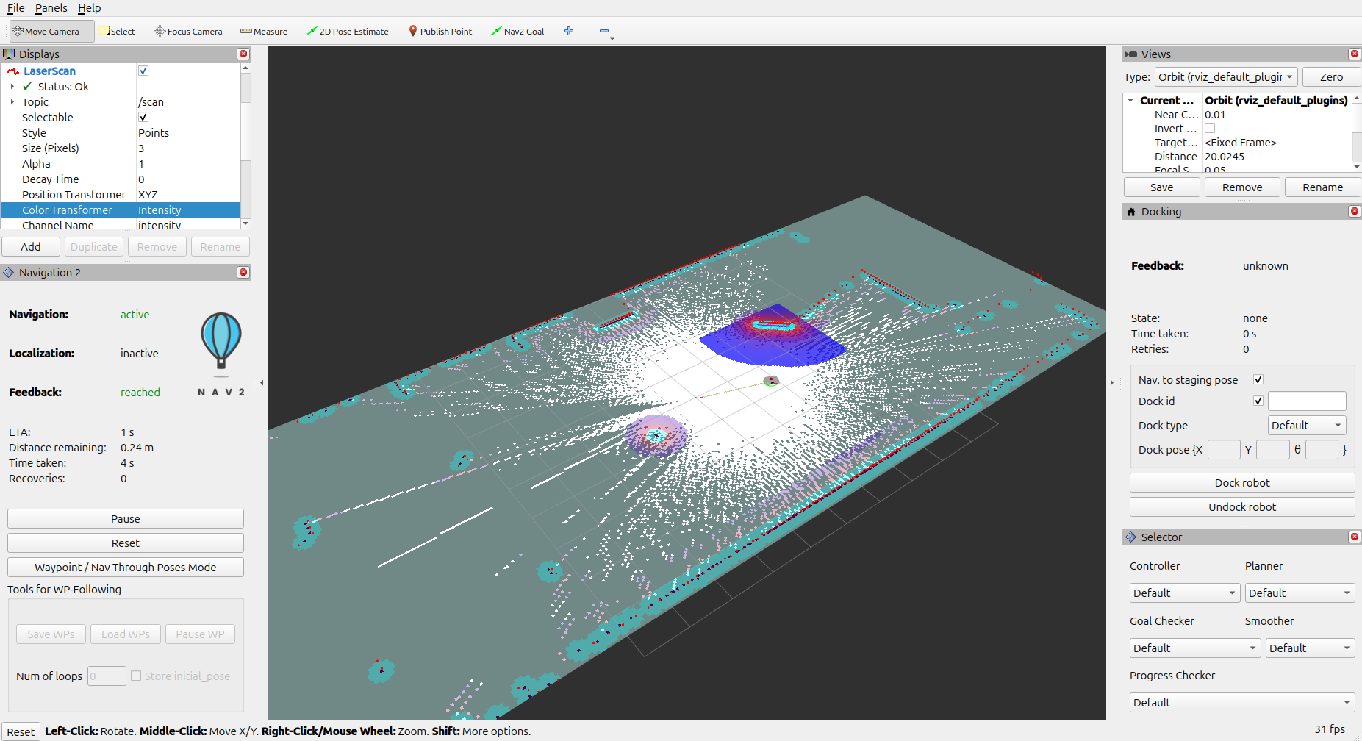
assets/images/slam/cafe.png
