attu0/benzene/assets/images/slam/warehouse.png

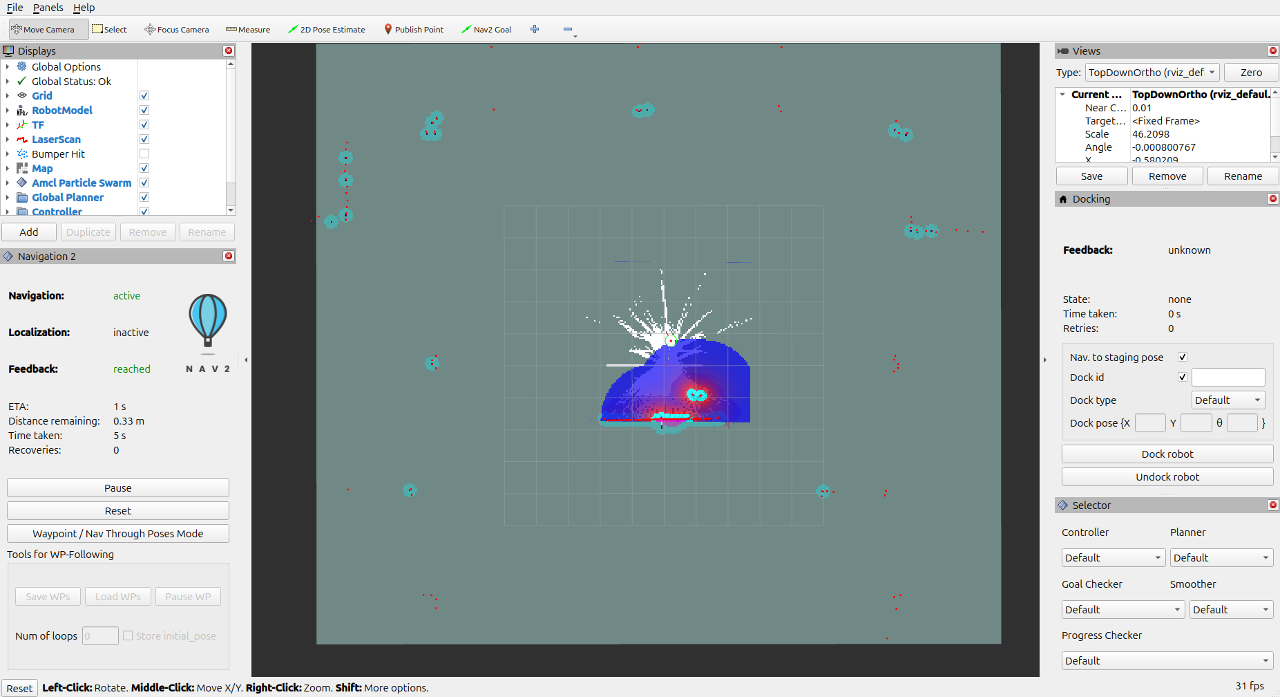
assets/images/slam/warehouse.png
