attu0/benzene/assets/images/teleop/teleop.png

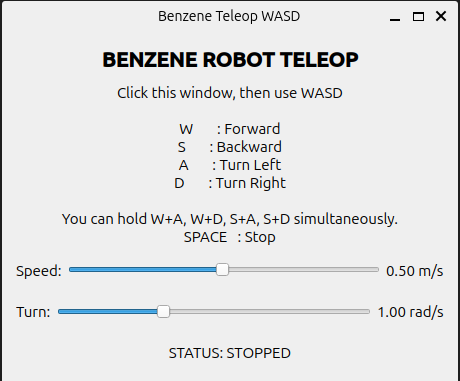
assets/images/teleop/teleop.png
