attu0/benzene/assets/images/waypoints/office/gazebo.png

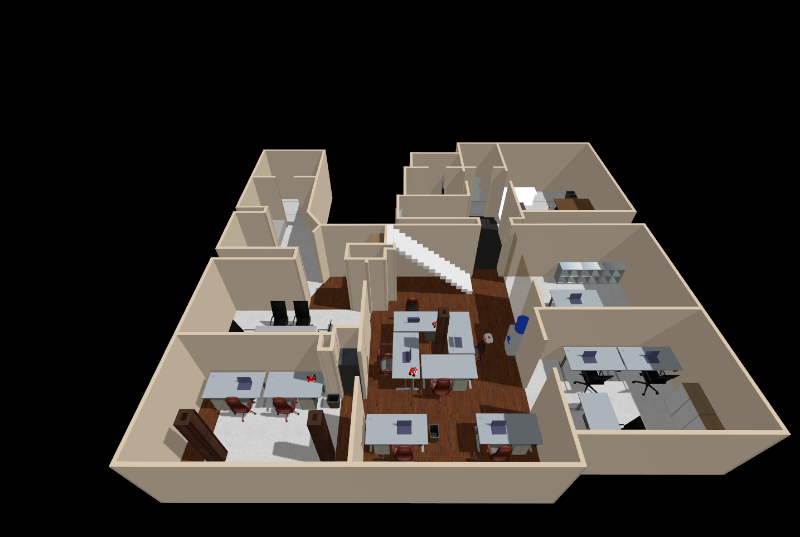
assets/images/waypoints/office/gazebo.png
