attu0/benzene/assets/images/waypoints/office/rviz1.png

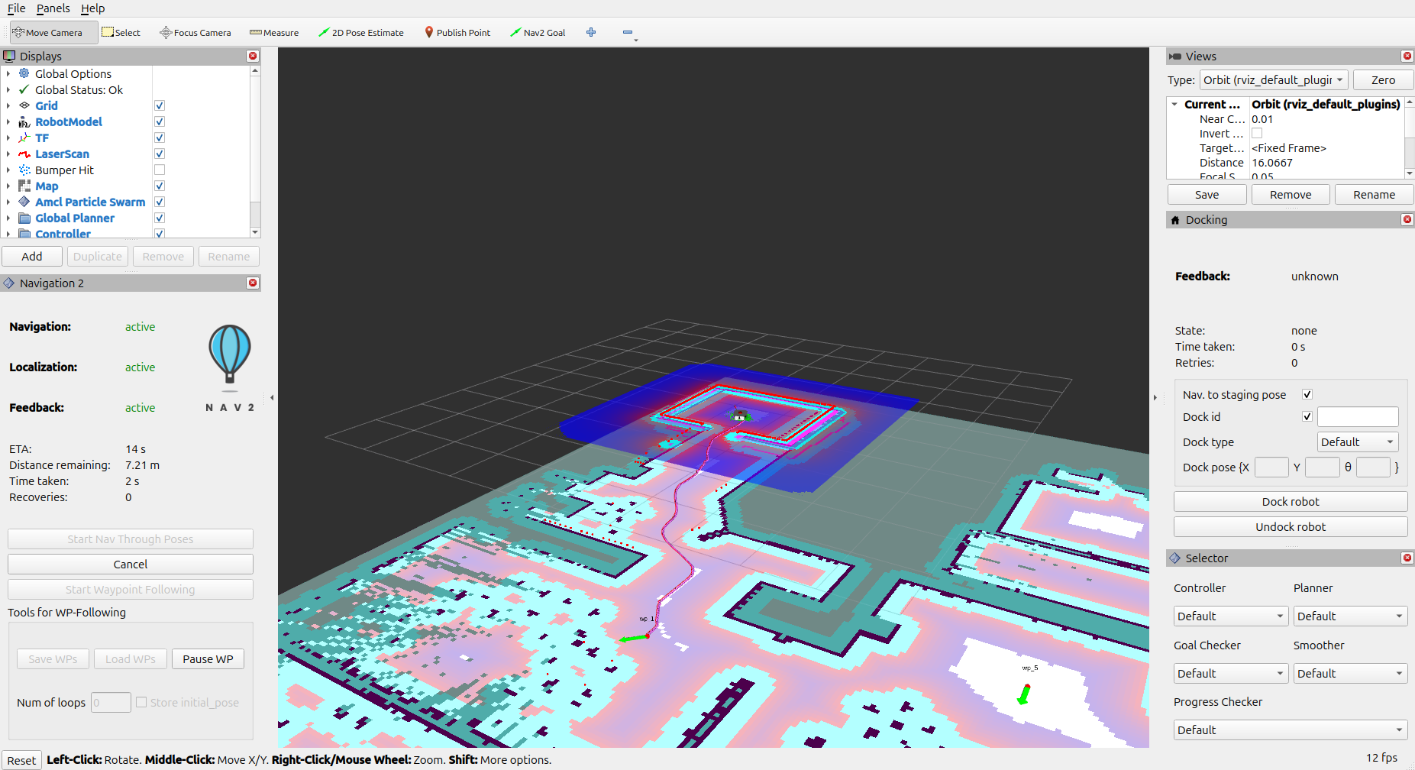
assets/images/waypoints/office/rviz1.png
