attu0/benzene/assets/images/waypoints/office/rviz2.png

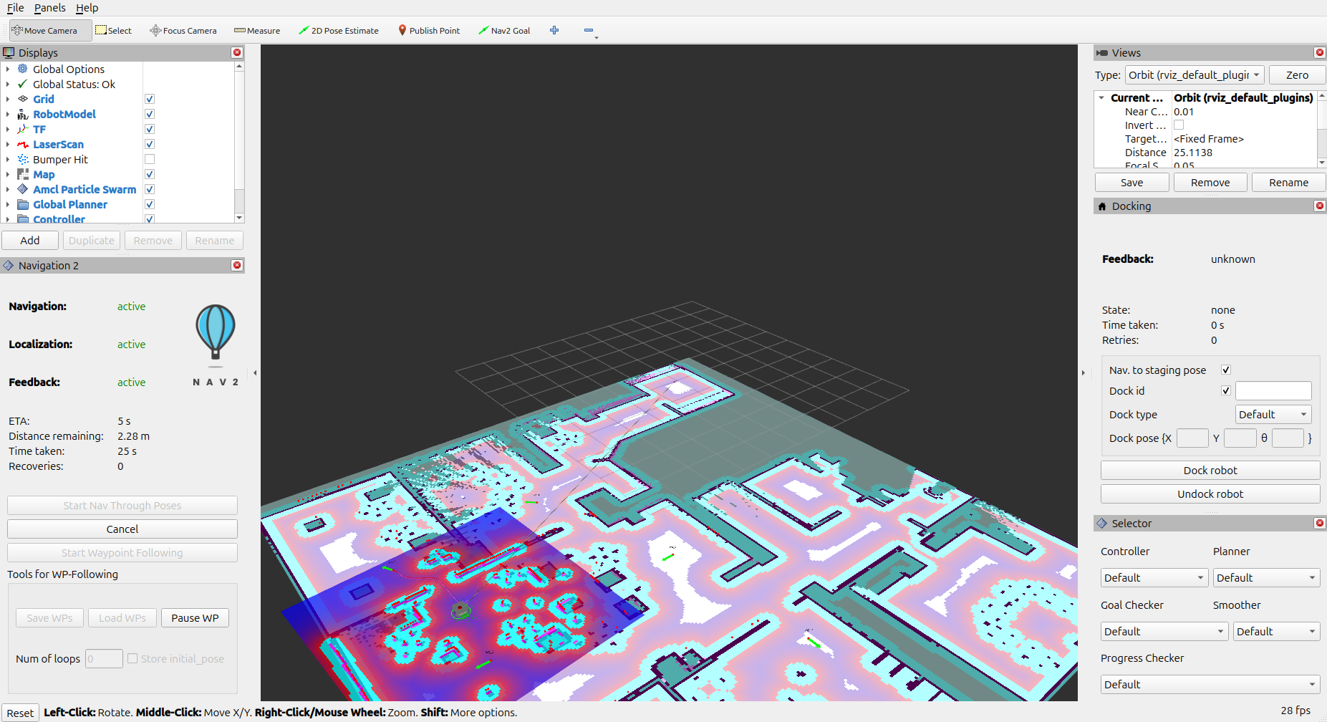
assets/images/waypoints/office/rviz2.png
