attu0/benzene/benzene_gazebo/models/mustard/meshes/texture_map.png

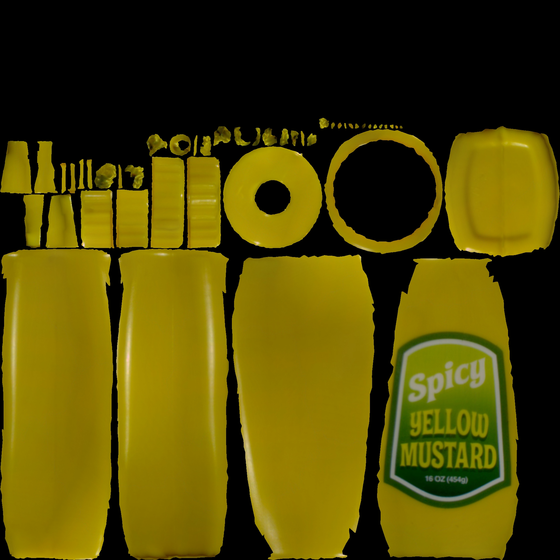
benzene_gazebo/models/mustard/meshes/texture_map.png
