attu0/benzene/benzene_gazebo/models/office/meshes/ROB_work_station/10239_Office_Chair_v1_Diffuse.jpg

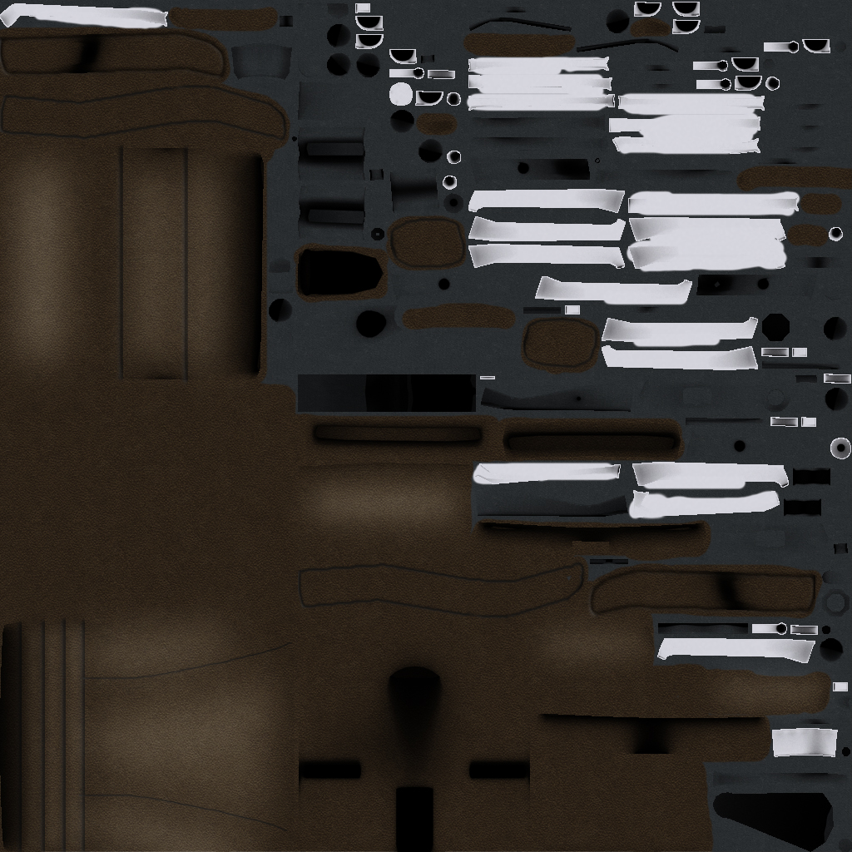
benzene_gazebo/models/office/meshes/ROB_work_station/10239_Office_Chair_v1_Diffuse.jpg
