attu0/benzene/benzene_gazebo/models/Surfaces/meshes/white_carpet.png

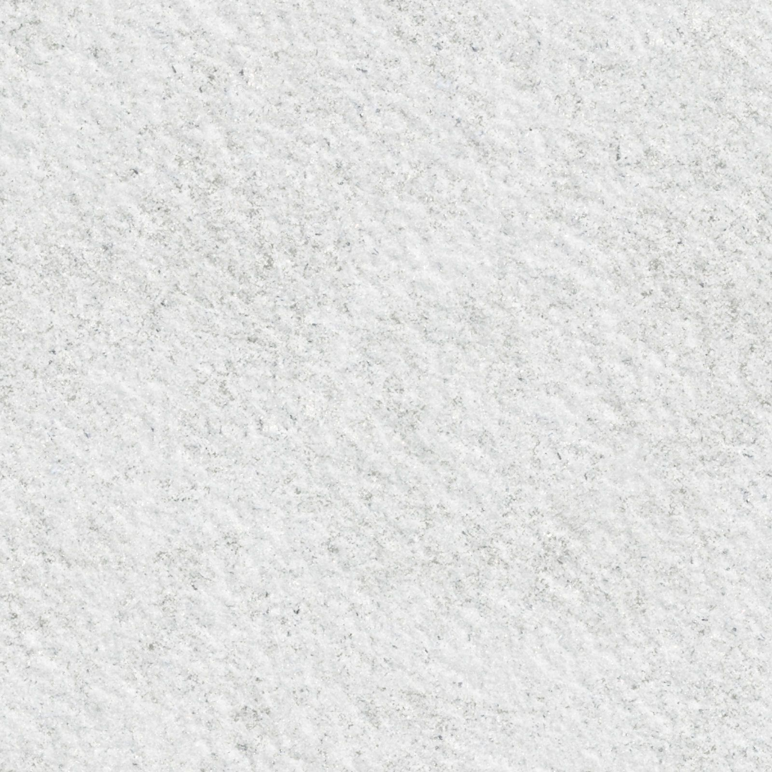
benzene_gazebo/models/Surfaces/meshes/white_carpet.png
