attu0/benzene/benzene_gazebo/models/Surfaces/meshes/white_tiles.png

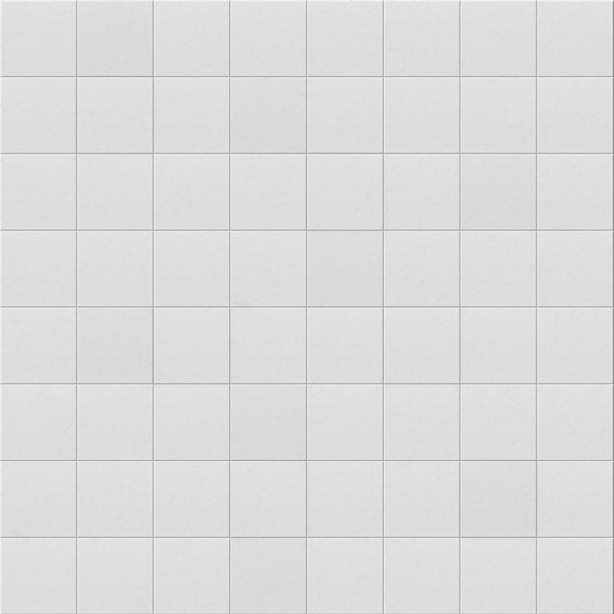
benzene_gazebo/models/Surfaces/meshes/white_tiles.png
