attu0/benzene/benzene_gazebo/models/Surfaces/meshes/wood1.png

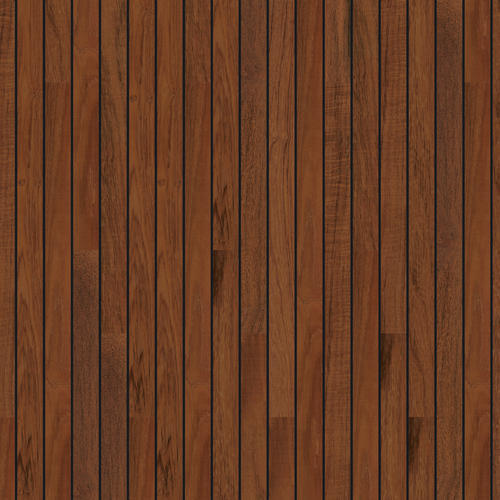
benzene_gazebo/models/Surfaces/meshes/wood1.png
