attu0/benzene/benzene_gazebo/models/Surfaces/meshes/wood2.png

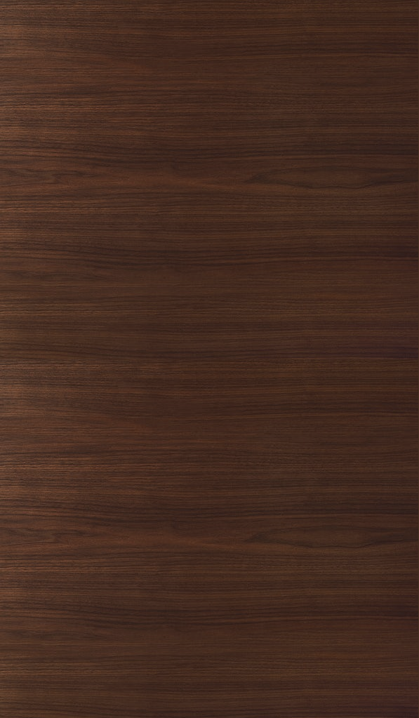
benzene_gazebo/models/Surfaces/meshes/wood2.png
