attu0/benzene/benzene_gazebo/models/Apriltag36_11_00000/materials/textures/tag36_11_00000.png

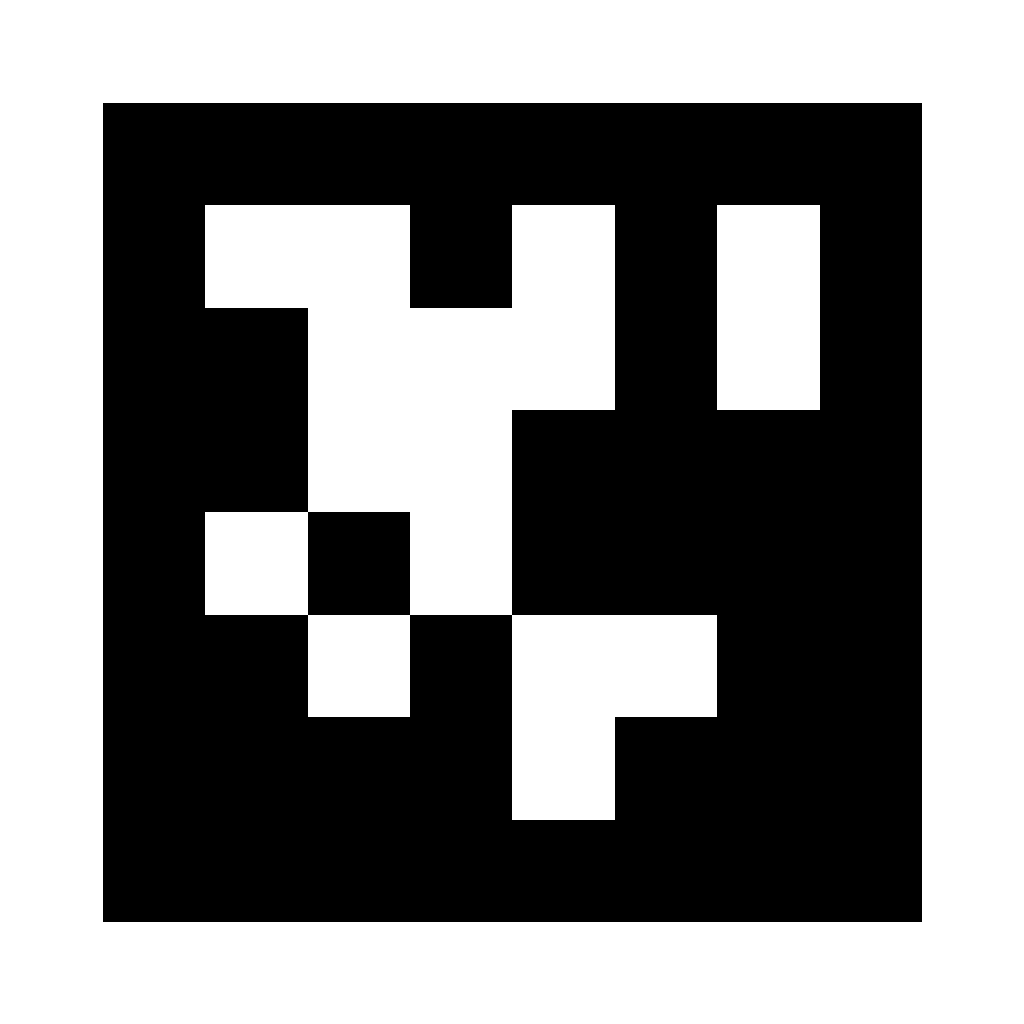
benzene_gazebo/models/Apriltag36_11_00000/materials/textures/tag36_11_00000.png
