attu0/benzene/benzene_gazebo/models/aws_bucket/materials/textures/aws_robomaker_warehouse_Bucket_01.png

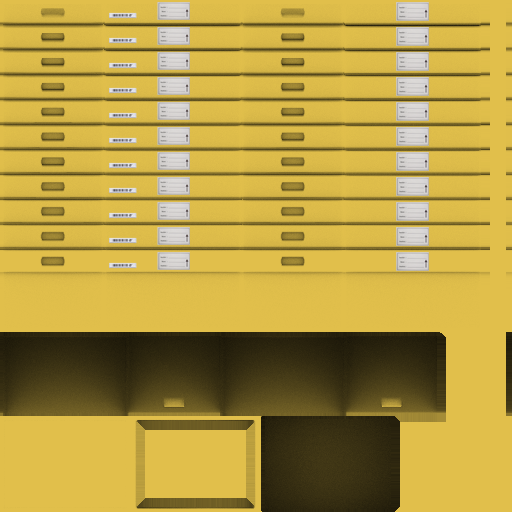
benzene_gazebo/models/aws_bucket/materials/textures/aws_robomaker_warehouse_Bucket_01.png
