attu0/benzene/benzene_gazebo/models/aws_cluttering_A/materials/textures/aws_robomaker_warehouse_ClutteringA_02.png

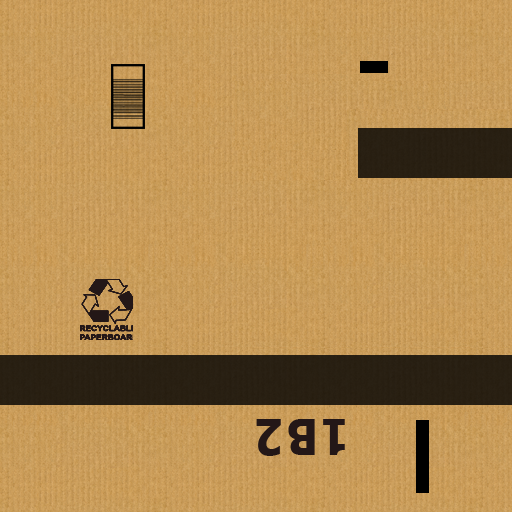
benzene_gazebo/models/aws_cluttering_A/materials/textures/aws_robomaker_warehouse_ClutteringA_02.png
