attu0/benzene/benzene_gazebo/models/aws_desk_C/materials/textures/aws_robomaker_warehouse_DeskC_04.png

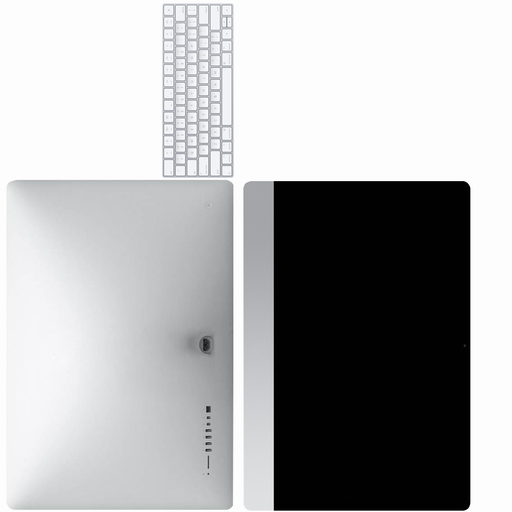
benzene_gazebo/models/aws_desk_C/materials/textures/aws_robomaker_warehouse_DeskC_04.png
