attu0/benzene/benzene_gazebo/models/aws_palletjack_B/materials/textures/aws_robomaker_warehouse_PalletJackB_02.png

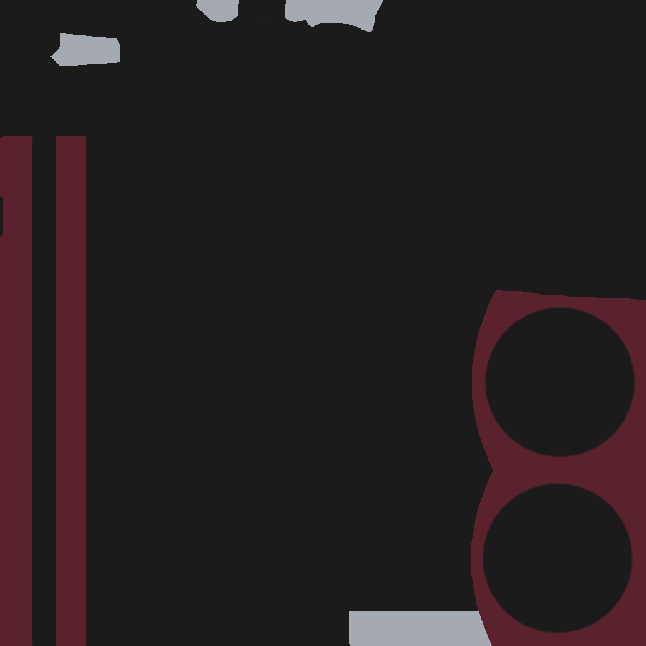
benzene_gazebo/models/aws_palletjack_B/materials/textures/aws_robomaker_warehouse_PalletJackB_02.png
