attu0/benzene/benzene_gazebo/models/aws_robomaker_residential_Ball_01/materials/textures/aws_Ball_01.png

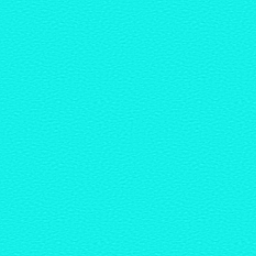
benzene_gazebo/models/aws_robomaker_residential_Ball_01/materials/textures/aws_Ball_01.png
