attu0/benzene/benzene_gazebo/models/aws_robomaker_residential_Bed_01/materials/textures/aws_BedA_01.png

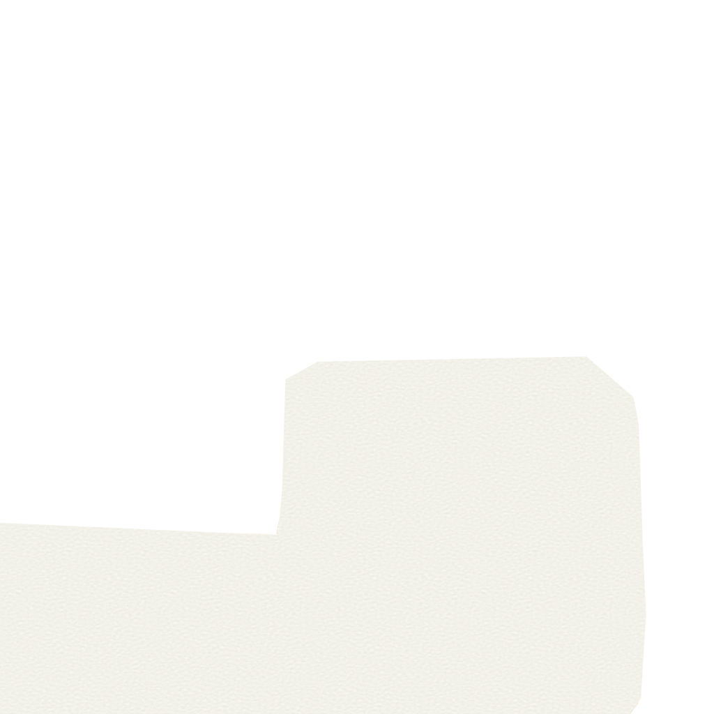
benzene_gazebo/models/aws_robomaker_residential_Bed_01/materials/textures/aws_BedA_01.png
