attu0/benzene/benzene_gazebo/models/aws_robomaker_residential_Board_01/materials/textures/aws_Board_01.png

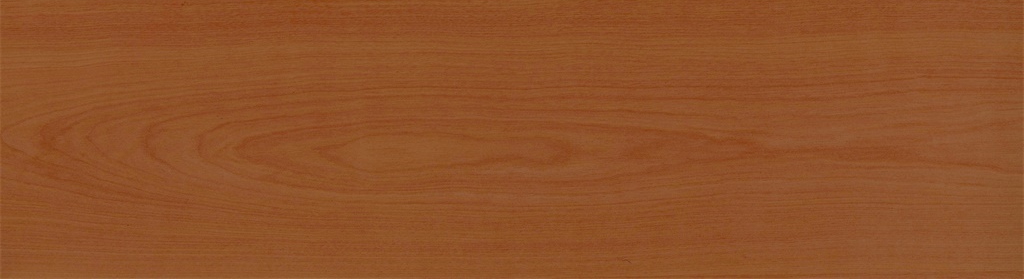
benzene_gazebo/models/aws_robomaker_residential_Board_01/materials/textures/aws_Board_01.png
