attu0/benzene/benzene_gazebo/models/aws_robomaker_residential_Carpet_01/materials/textures/aws_Carpet_01.png

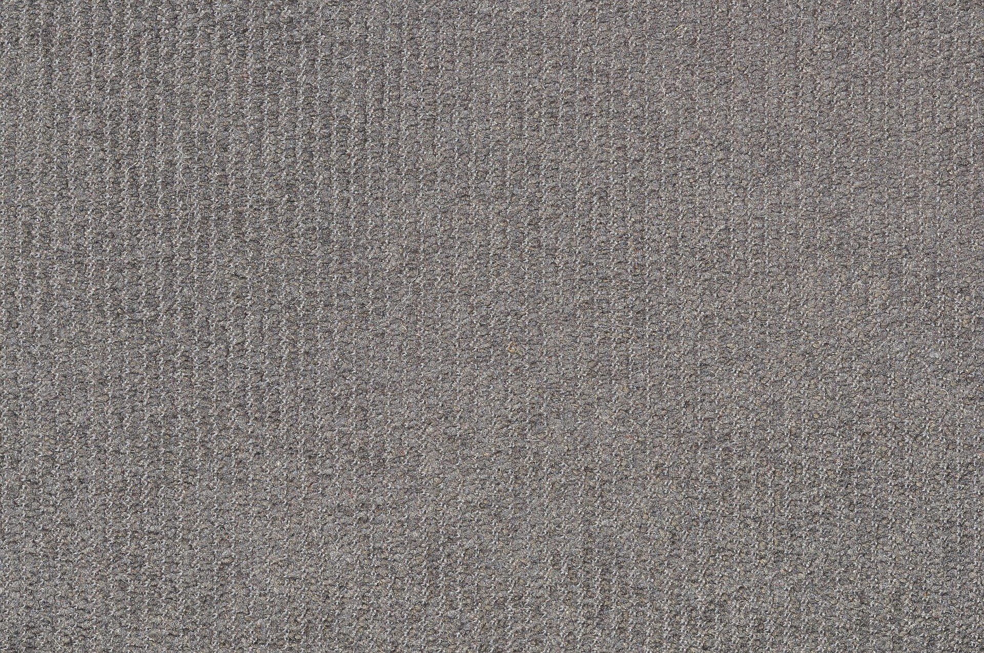
benzene_gazebo/models/aws_robomaker_residential_Carpet_01/materials/textures/aws_Carpet_01.png
