attu0/benzene/benzene_gazebo/models/aws_robomaker_residential_ChairA_01/materials/textures/aws_ChairA_01.png

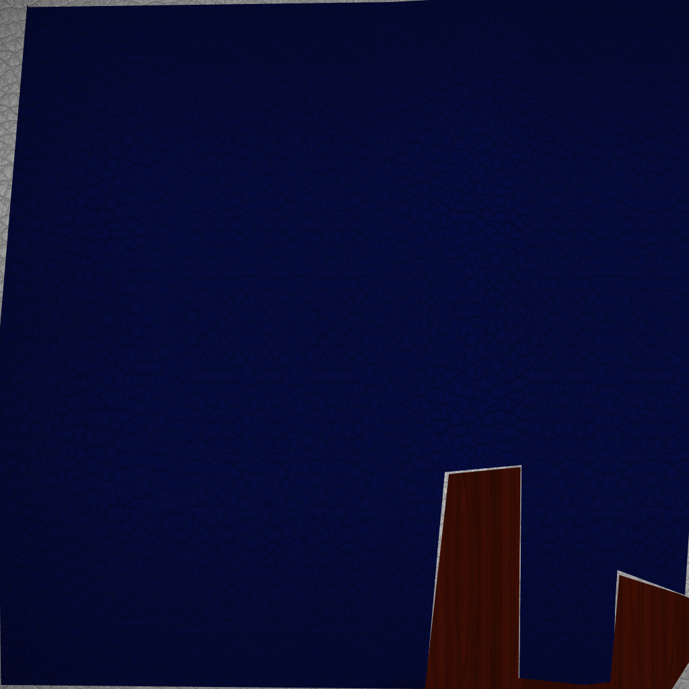
benzene_gazebo/models/aws_robomaker_residential_ChairA_01/materials/textures/aws_ChairA_01.png
