attu0/benzene/benzene_gazebo/models/aws_robomaker_residential_Curtain_01/materials/textures/aws_Curtain_01.png

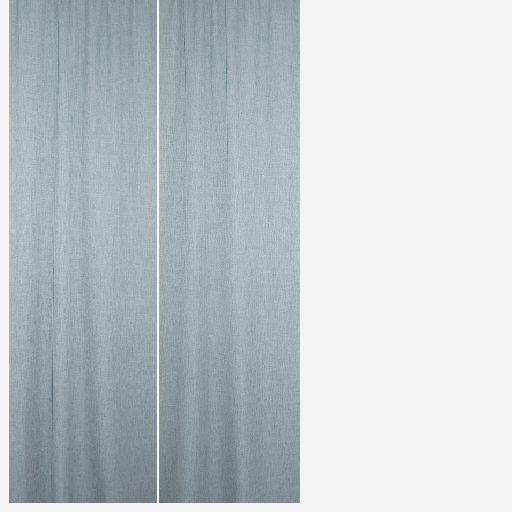
benzene_gazebo/models/aws_robomaker_residential_Curtain_01/materials/textures/aws_Curtain_01.png
