attu0/benzene/benzene_gazebo/models/aws_robomaker_residential_Door_01/materials/textures/aws_Door_01.png

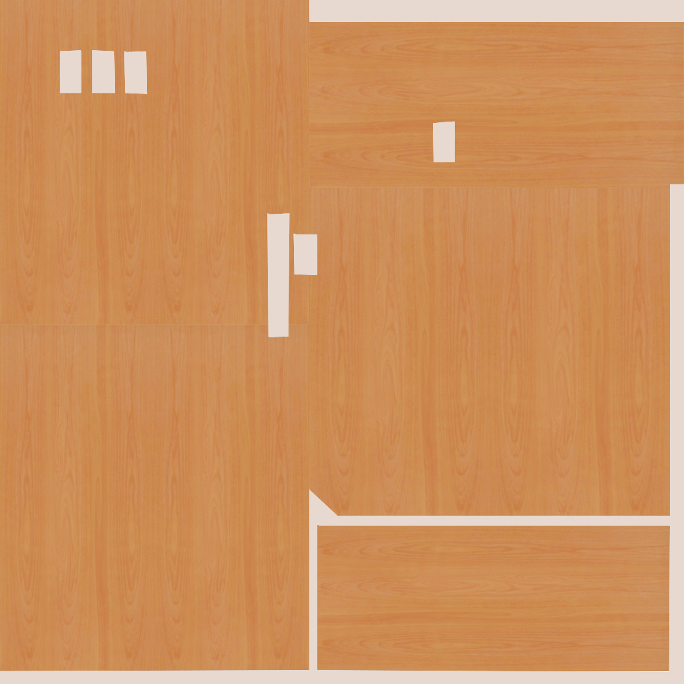
benzene_gazebo/models/aws_robomaker_residential_Door_01/materials/textures/aws_Door_01.png
