attu0/benzene/benzene_gazebo/models/aws_robomaker_residential_FloorB_01/materials/textures/aws_FloorB_01.png

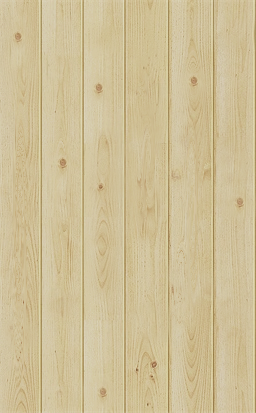
benzene_gazebo/models/aws_robomaker_residential_FloorB_01/materials/textures/aws_FloorB_01.png
