attu0/benzene/benzene_gazebo/models/aws_robomaker_residential_Handle_01/materials/textures/aws_Handle_01.png

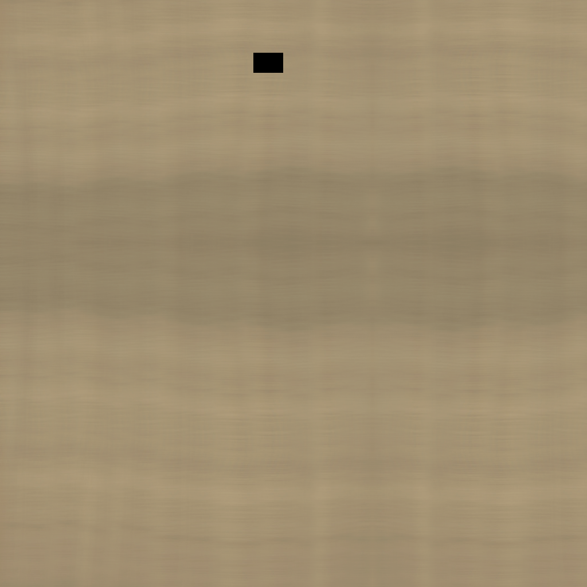
benzene_gazebo/models/aws_robomaker_residential_Handle_01/materials/textures/aws_Handle_01.png
