attu0/benzene/benzene_gazebo/models/aws_robomaker_residential_NightStand_01/materials/textures/aws_NightStand_01.png

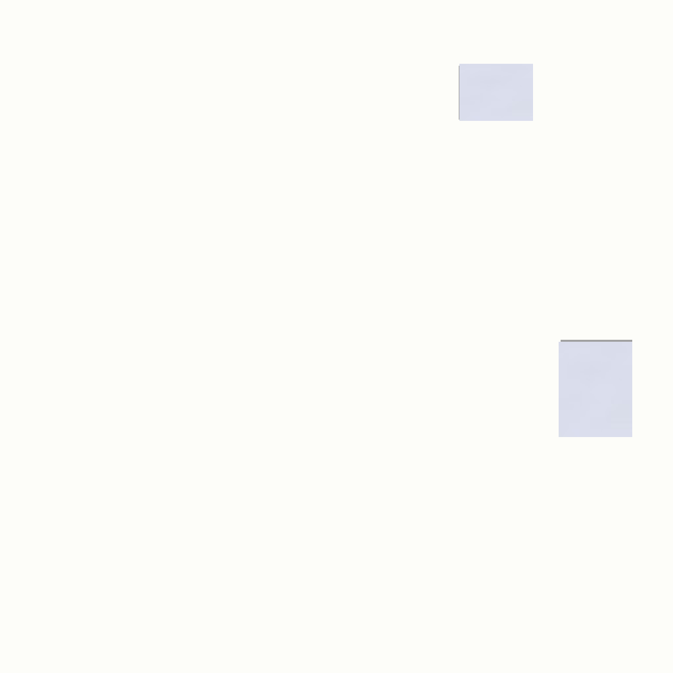
benzene_gazebo/models/aws_robomaker_residential_NightStand_01/materials/textures/aws_NightStand_01.png
