attu0/benzene/benzene_gazebo/models/aws_robomaker_residential_PortraitA_01/materials/textures/PortraitA_01.jpg

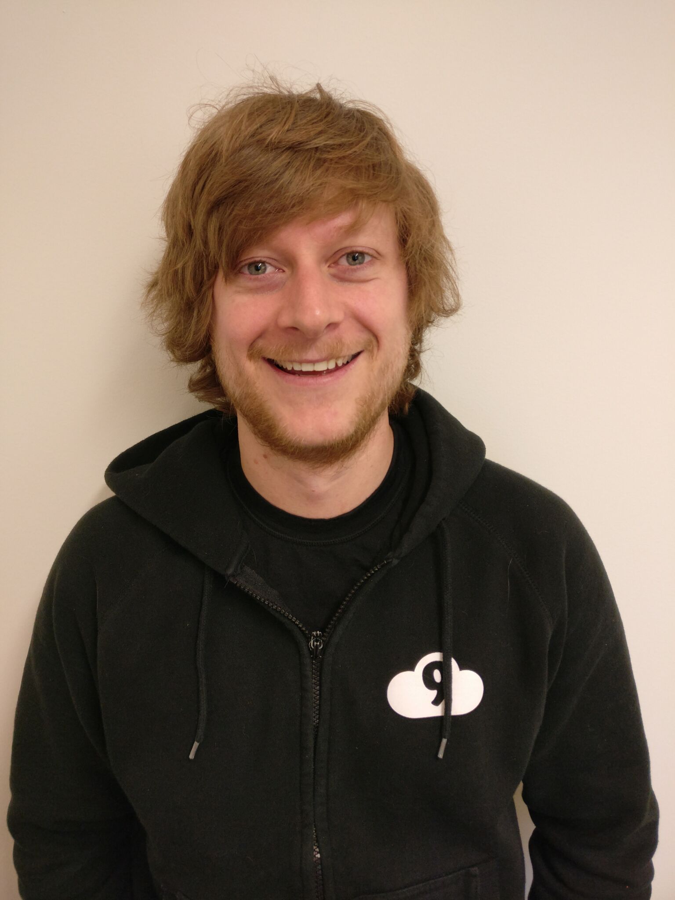
benzene_gazebo/models/aws_robomaker_residential_PortraitA_01/materials/textures/PortraitA_01.jpg
