attu0/benzene/benzene_gazebo/models/aws_robomaker_residential_PortraitA_02/materials/textures/PortraitA_02.jpg

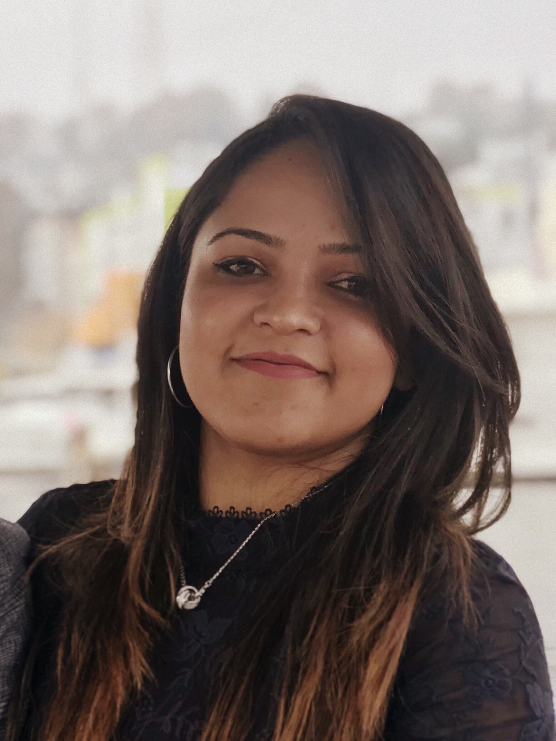
benzene_gazebo/models/aws_robomaker_residential_PortraitA_02/materials/textures/PortraitA_02.jpg
