attu0/benzene/benzene_gazebo/models/aws_robomaker_residential_PortraitB_01/materials/textures/PortraitB_01.jpg

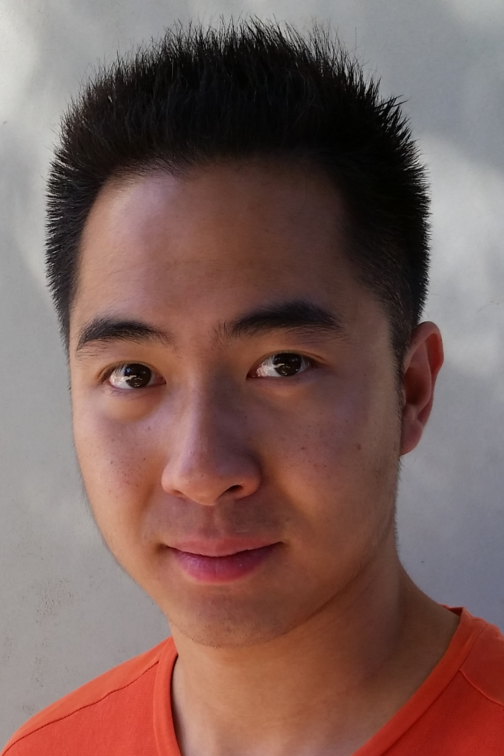
benzene_gazebo/models/aws_robomaker_residential_PortraitB_01/materials/textures/PortraitB_01.jpg
