attu0/benzene/benzene_gazebo/models/aws_robomaker_residential_PortraitB_02/materials/textures/PortraitB_02.jpg

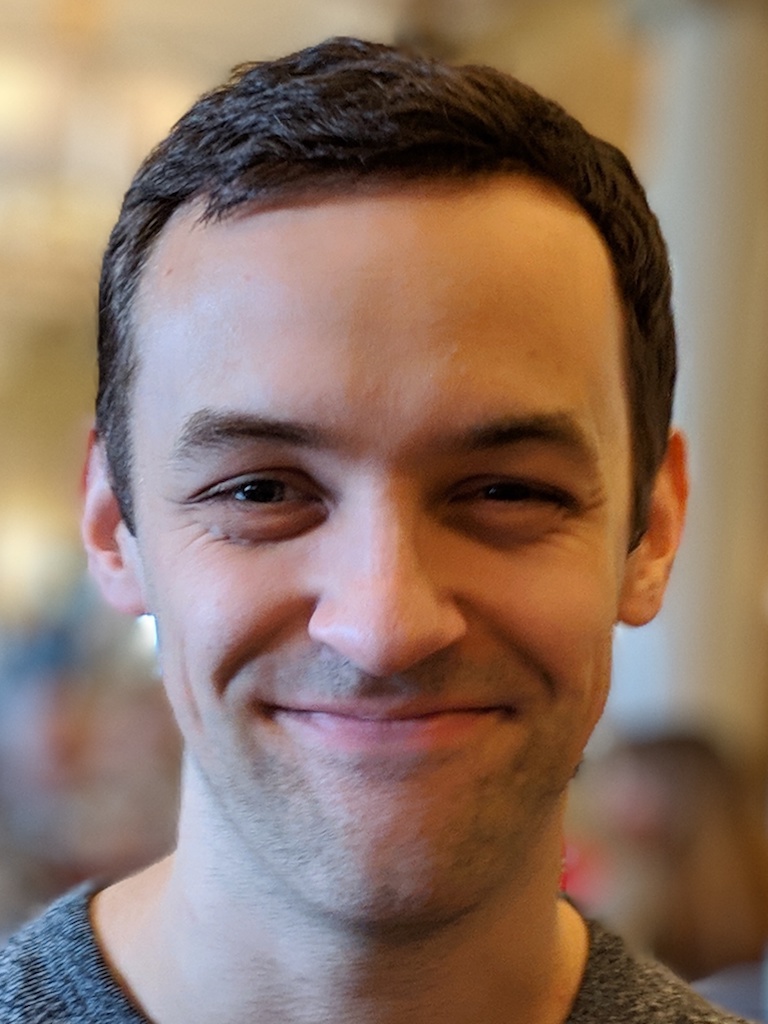
benzene_gazebo/models/aws_robomaker_residential_PortraitB_02/materials/textures/PortraitB_02.jpg
