attu0/benzene/benzene_gazebo/models/aws_robomaker_residential_PortraitB_03/materials/textures/PortraitB_03.jpg

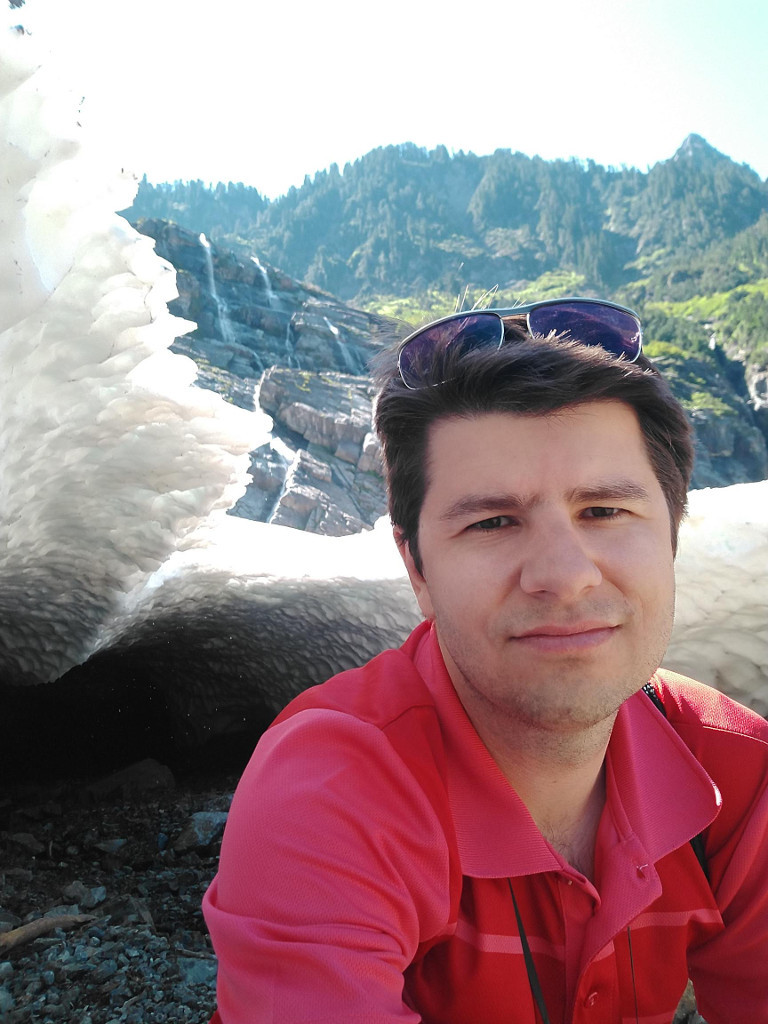
benzene_gazebo/models/aws_robomaker_residential_PortraitB_03/materials/textures/PortraitB_03.jpg
