attu0/benzene/benzene_gazebo/models/aws_robomaker_residential_PortraitC_01/materials/textures/PortraitC_01.jpg

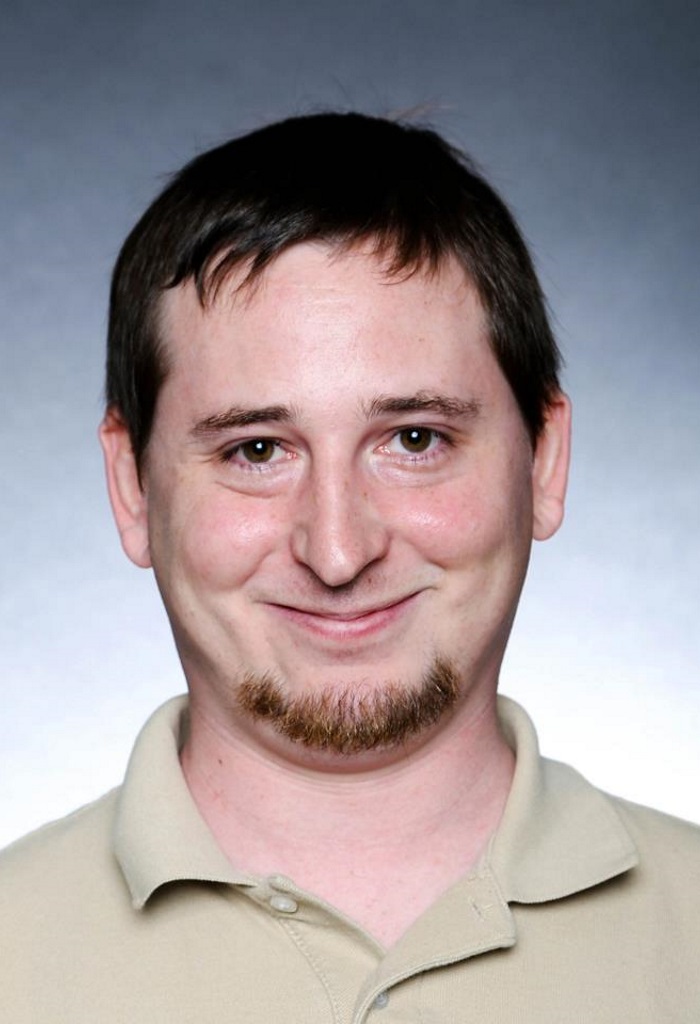
benzene_gazebo/models/aws_robomaker_residential_PortraitC_01/materials/textures/PortraitC_01.jpg
