attu0/benzene/benzene_gazebo/models/aws_robomaker_residential_PortraitE_01/materials/textures/PortraitE_01.jpg

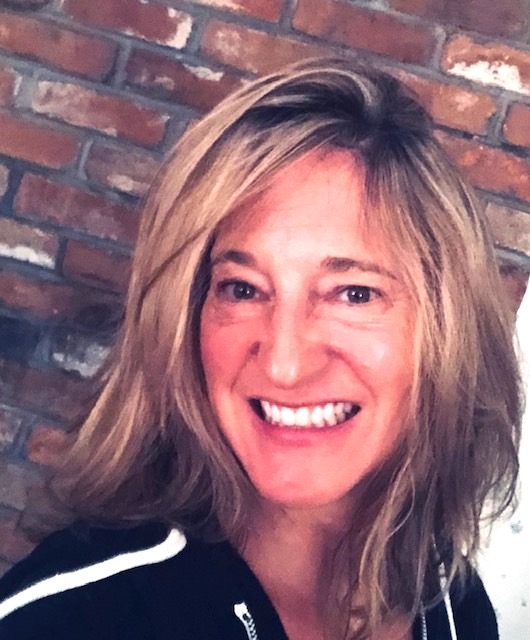
benzene_gazebo/models/aws_robomaker_residential_PortraitE_01/materials/textures/PortraitE_01.jpg
