attu0/benzene/benzene_gazebo/models/aws_robomaker_residential_PortraitE_02/materials/textures/PortraitE_02.jpg

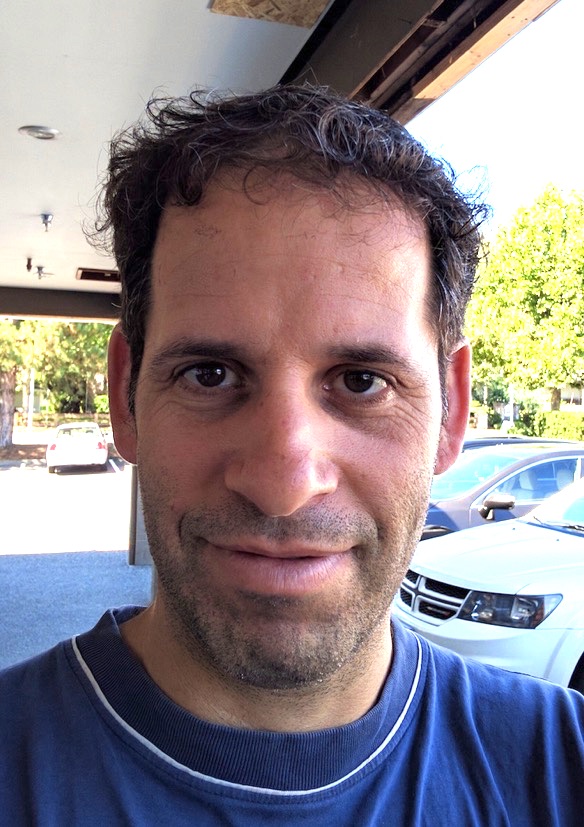
benzene_gazebo/models/aws_robomaker_residential_PortraitE_02/materials/textures/PortraitE_02.jpg
