attu0/benzene/benzene_gazebo/models/aws_robomaker_residential_Tableware_01/materials/textures/aws_Tableware_01.png

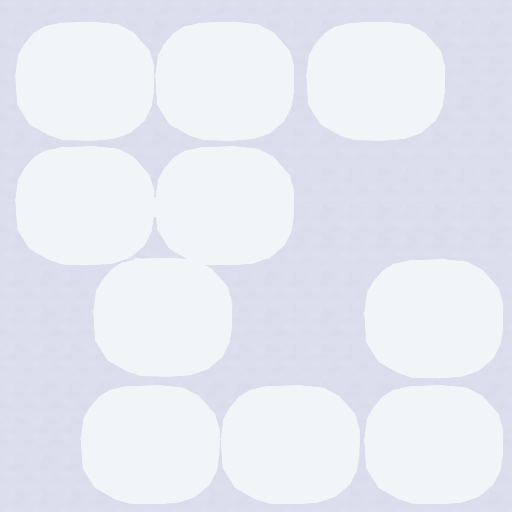
benzene_gazebo/models/aws_robomaker_residential_Tableware_01/materials/textures/aws_Tableware_01.png
