attu0/benzene/benzene_gazebo/models/aws_robomaker_residential_Trash_01/materials/textures/aws_Trash_01.png

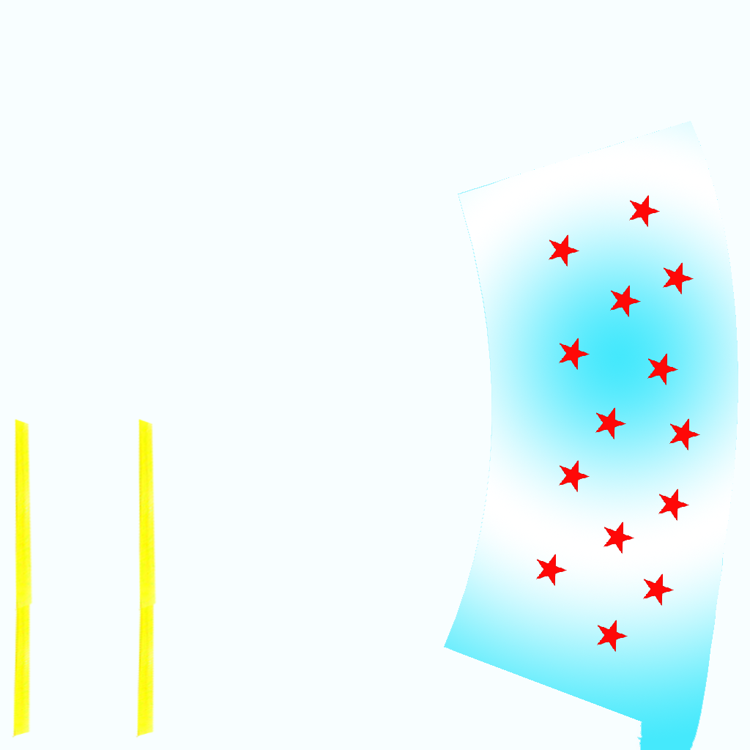
benzene_gazebo/models/aws_robomaker_residential_Trash_01/materials/textures/aws_Trash_01.png
