attu0/benzene/benzene_gazebo/models/aws_robomaker_residential_TV_02/materials/textures/aws_TV_01.png

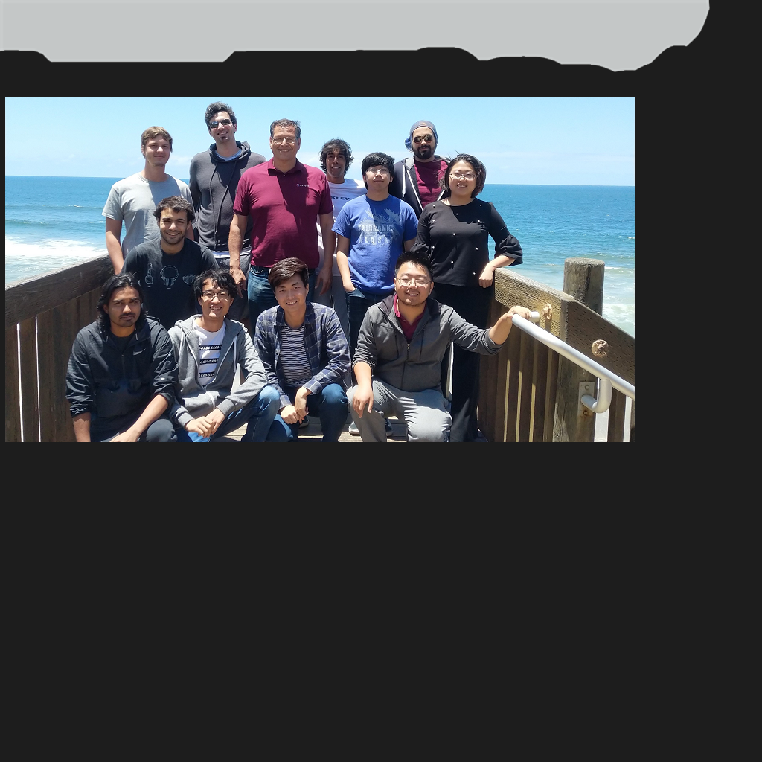
benzene_gazebo/models/aws_robomaker_residential_TV_02/materials/textures/aws_TV_01.png
