attu0/benzene/benzene_gazebo/models/aws_robomaker_residential_Vase_01/materials/textures/aws_Vase_01.png

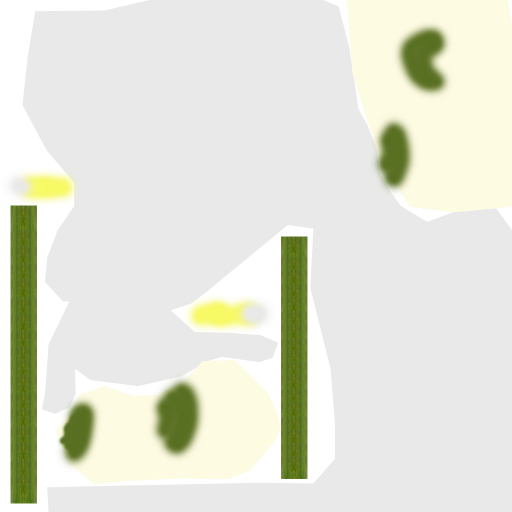
benzene_gazebo/models/aws_robomaker_residential_Vase_01/materials/textures/aws_Vase_01.png
