attu0/benzene/benzene_gazebo/models/aws_trashcan/materials/textures/aws_robomaker_warehouse_TrashCanC_01.png

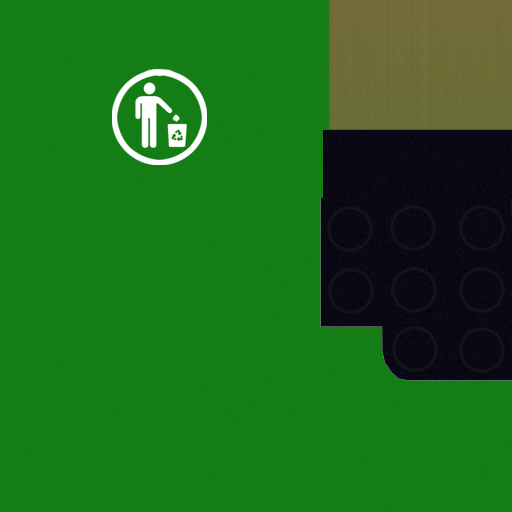
benzene_gazebo/models/aws_trashcan/materials/textures/aws_robomaker_warehouse_TrashCanC_01.png
