attu0/benzene/benzene_gazebo/models/cafe/materials/textures/__auto_21.jpg

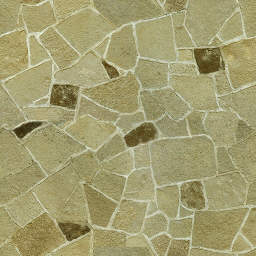
benzene_gazebo/models/cafe/materials/textures/__auto_21.jpg
