attu0/benzene/benzene_gazebo/models/cafe/materials/textures/__auto_26.jpg

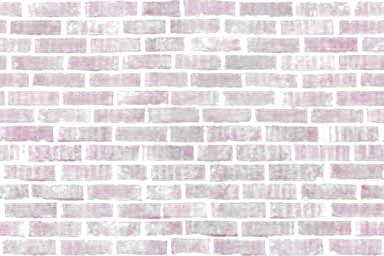
benzene_gazebo/models/cafe/materials/textures/__auto_26.jpg
