attu0/benzene/benzene_gazebo/models/cafe/materials/textures/__auto_35.jpg

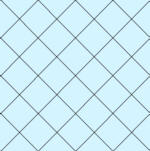
benzene_gazebo/models/cafe/materials/textures/__auto_35.jpg
