attu0/benzene/benzene_gazebo/models/cafe/materials/textures/__auto_37.jpg

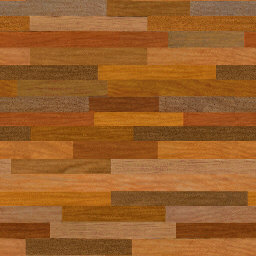
benzene_gazebo/models/cafe/materials/textures/__auto_37.jpg
