attu0/benzene/benzene_gazebo/models/cafe_counter/materials/textures/cafe_counter.png

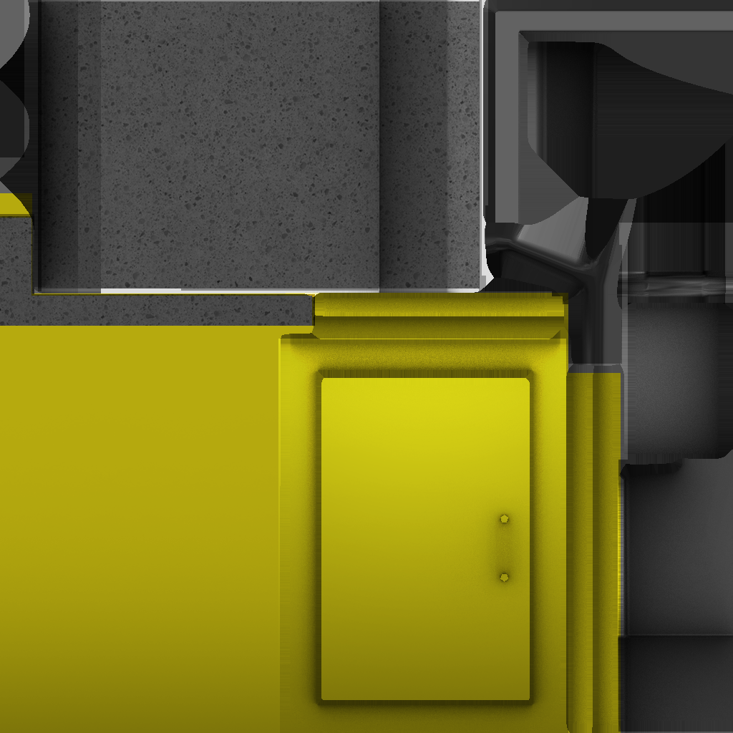
benzene_gazebo/models/cafe_counter/materials/textures/cafe_counter.png
