attu0/benzene/benzene_gazebo/models/cafe_table/materials/textures/Maple.jpg

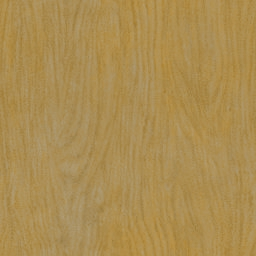
benzene_gazebo/models/cafe_table/materials/textures/Maple.jpg
