attu0/benzene/benzene_gazebo/models/coke_can/materials/textures/coke_can.png

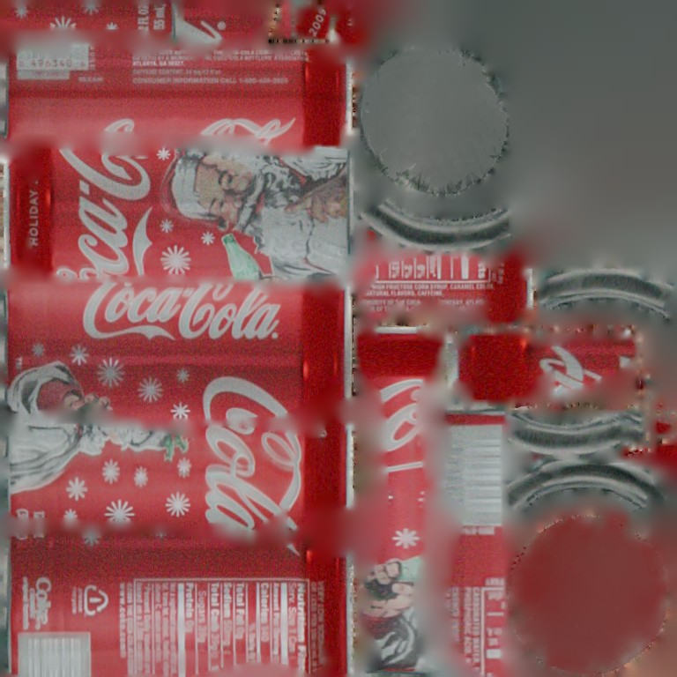
benzene_gazebo/models/coke_can/materials/textures/coke_can.png
