attu0/benzene/benzene_gazebo/models/workcell/materials/textures/Bin.png

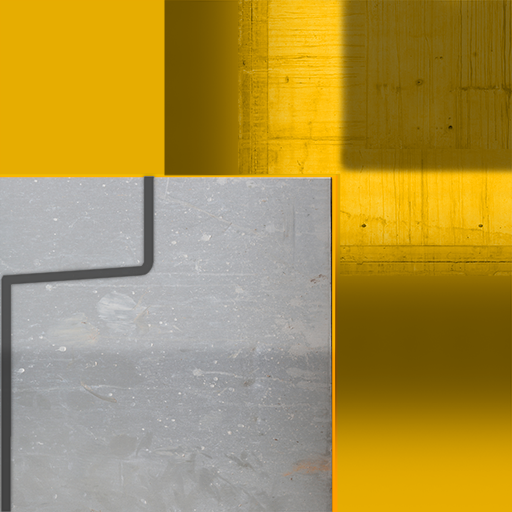
benzene_gazebo/models/workcell/materials/textures/Bin.png
