attu0/benzene/benzene_gazebo/models/workcell/materials/textures/CardboardBoxes.png

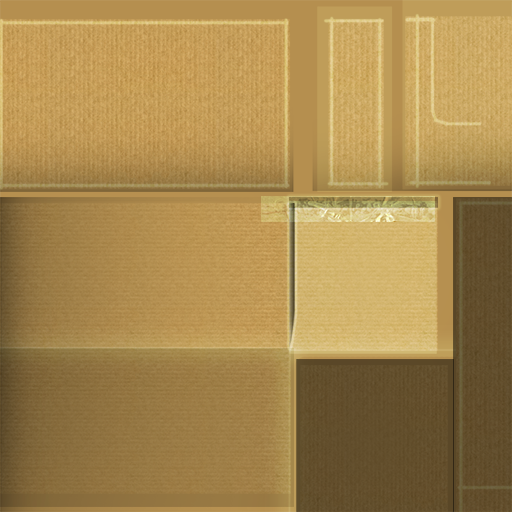
benzene_gazebo/models/workcell/materials/textures/CardboardBoxes.png
