attu0/benzene/benzene_gazebo/models/workcell/materials/textures/ControlPanel.png

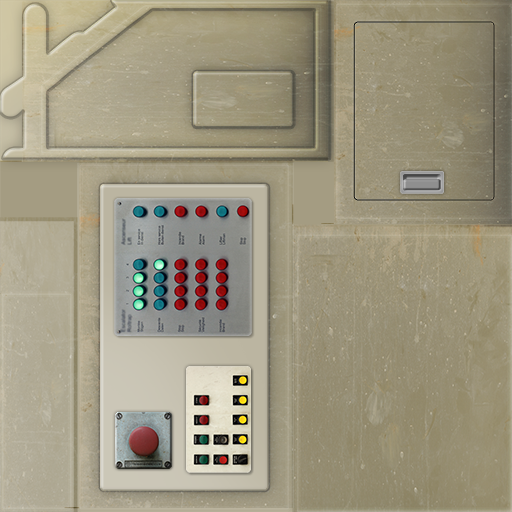
benzene_gazebo/models/workcell/materials/textures/ControlPanel.png
