attu0/benzene/benzene_gazebo/models/workcell/materials/textures/Conveyor.png

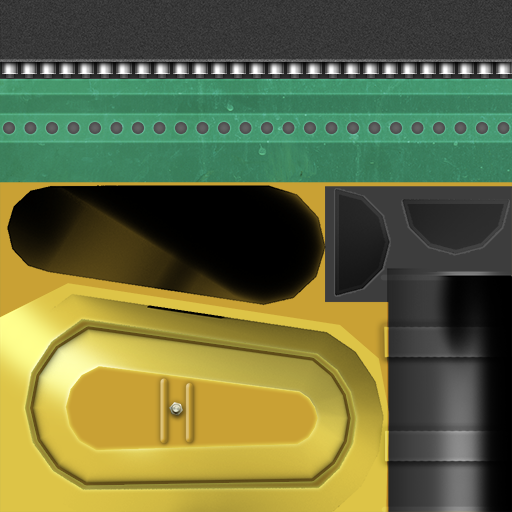
benzene_gazebo/models/workcell/materials/textures/Conveyor.png
