attu0/benzene/benzene_gazebo/models/workcell/materials/textures/Door_Window.png

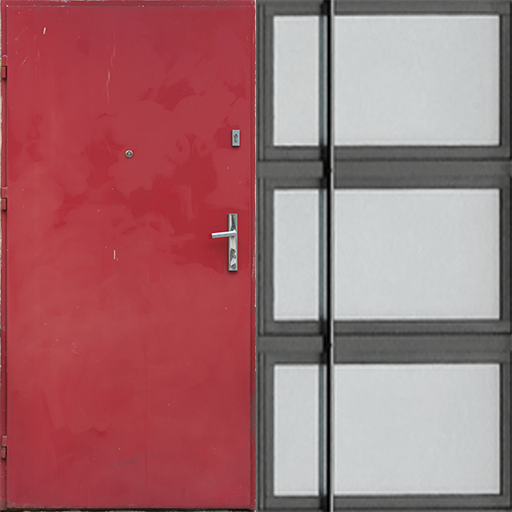
benzene_gazebo/models/workcell/materials/textures/Door_Window.png
