attu0/benzene/benzene_gazebo/models/workcell/materials/textures/Floor.png

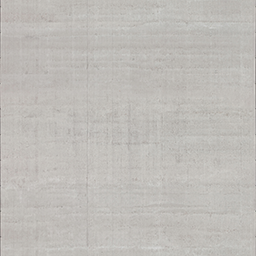
benzene_gazebo/models/workcell/materials/textures/Floor.png
