attu0/benzene/benzene_gazebo/models/workcell/materials/textures/Pallet.png

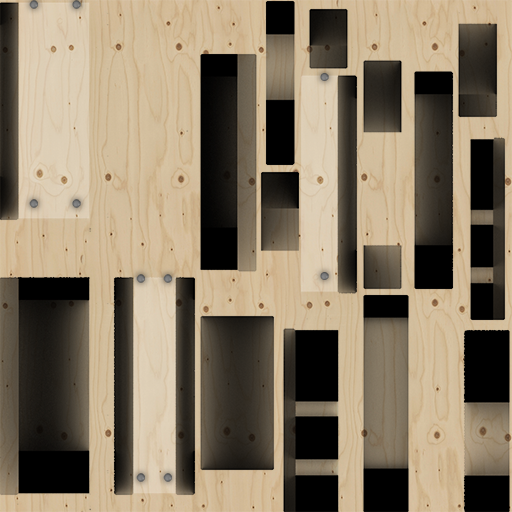
benzene_gazebo/models/workcell/materials/textures/Pallet.png
