attu0/benzene/benzene_gazebo/models/workcell/materials/textures/PalletWrap.png

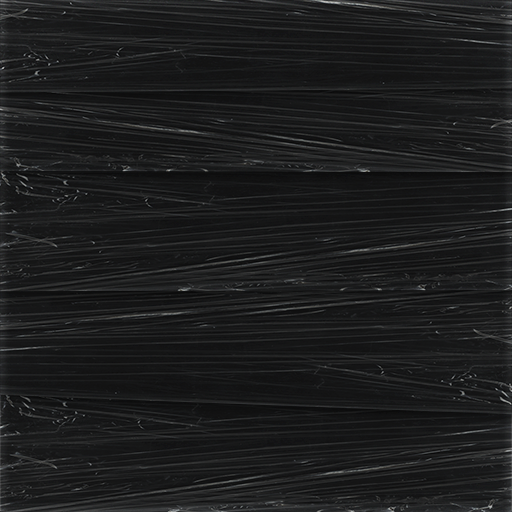
benzene_gazebo/models/workcell/materials/textures/PalletWrap.png
