attu0/benzene/benzene_gazebo/models/workcell/materials/textures/Pillar.png

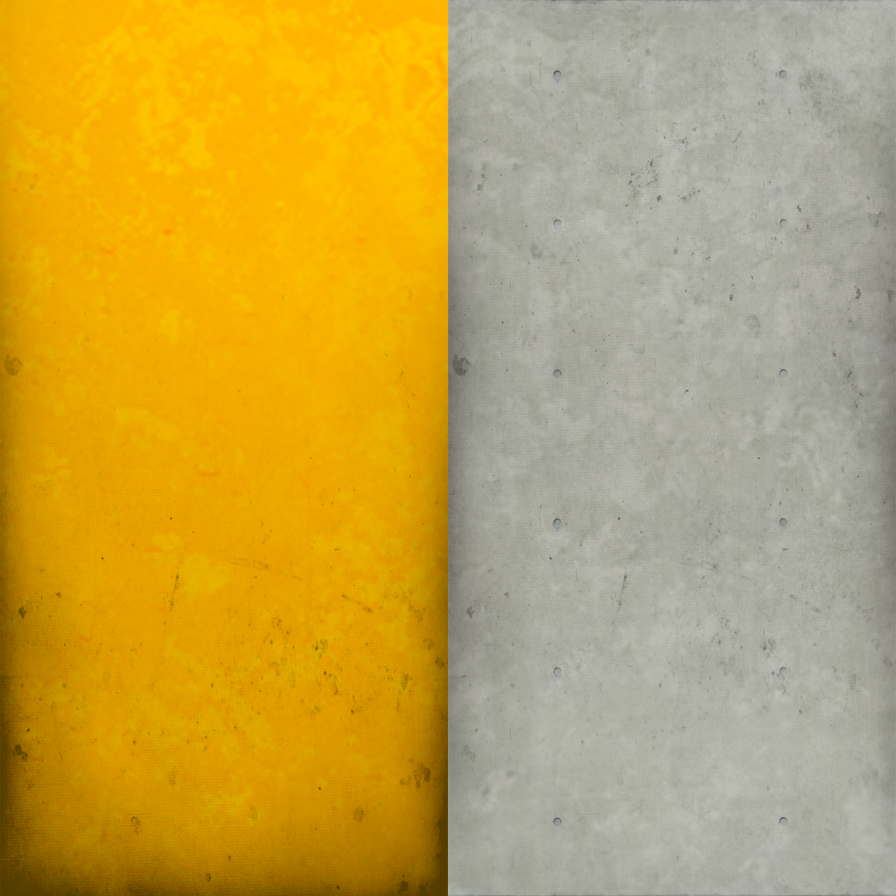
benzene_gazebo/models/workcell/materials/textures/Pillar.png
