attu0/benzene/benzene_gazebo/models/workcell/materials/textures/Plywood.png

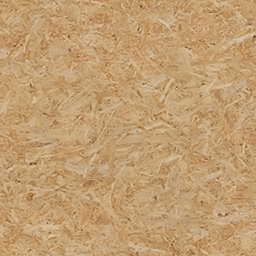
benzene_gazebo/models/workcell/materials/textures/Plywood.png
