attu0/benzene/benzene_gazebo/models/workcell/materials/textures/RollupDoor.png

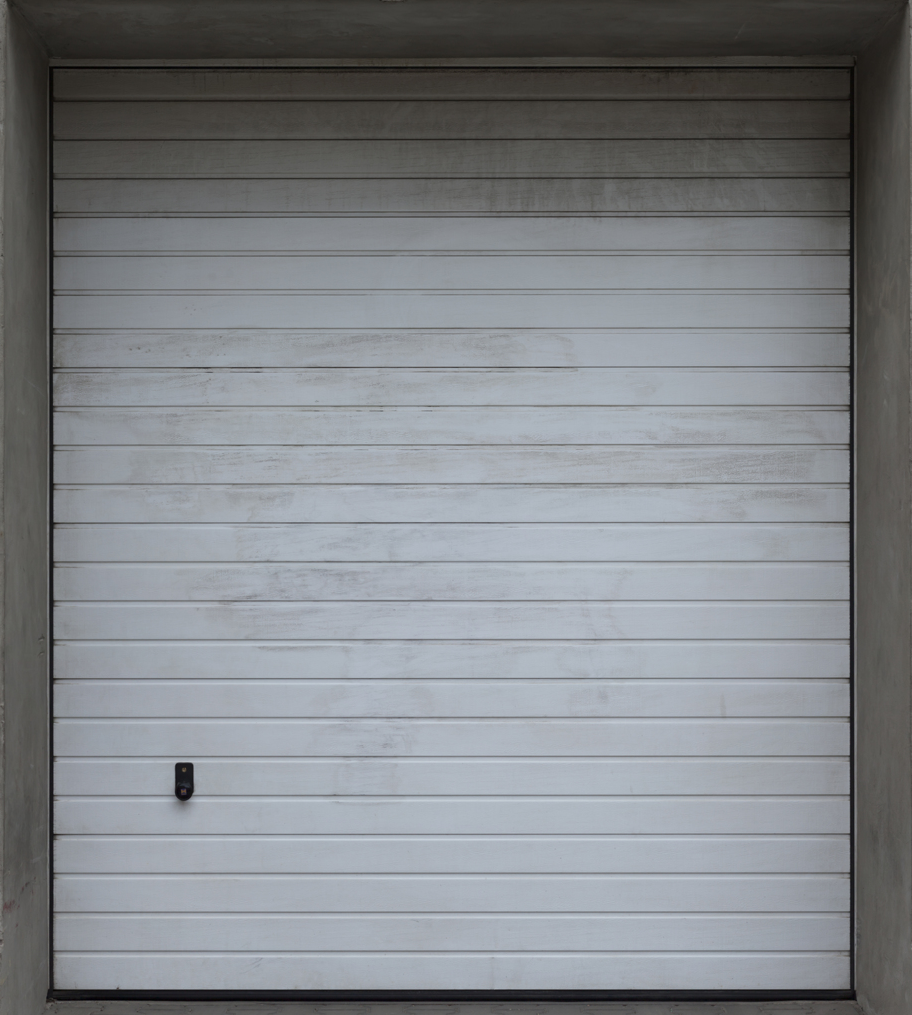
benzene_gazebo/models/workcell/materials/textures/RollupDoor.png
