attu0/benzene/benzene_gazebo/models/workcell/materials/textures/RubberMat.png

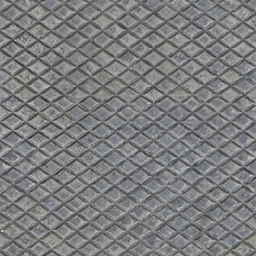
benzene_gazebo/models/workcell/materials/textures/RubberMat.png
