attu0/benzene/benzene_gazebo/models/workcell/materials/textures/Shelves.png

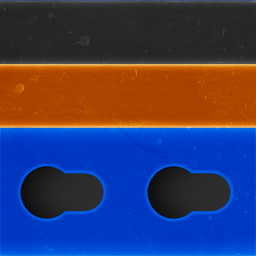
benzene_gazebo/models/workcell/materials/textures/Shelves.png
