attu0/benzene/benzene_gazebo/models/workcell/materials/textures/Stairs.png

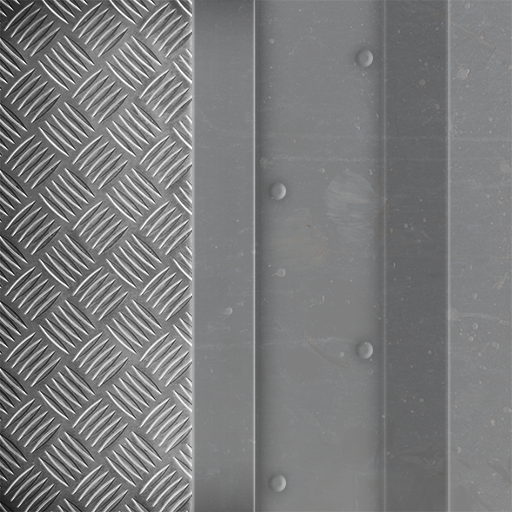
benzene_gazebo/models/workcell/materials/textures/Stairs.png
