attu0/benzene/benzene_gazebo/models/workcell/materials/textures/Wall_Concrete.png

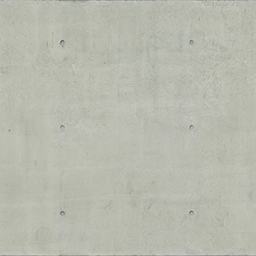
benzene_gazebo/models/workcell/materials/textures/Wall_Concrete.png
