attu0/benzene/benzene_gazebo/models/workcell/materials/textures/Wall_Corrugated.png

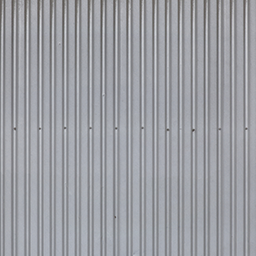
benzene_gazebo/models/workcell/materials/textures/Wall_Corrugated.png
