attu0/benzene/benzene_gazebo/models/workcell/materials/textures/WorkCell_Render.png

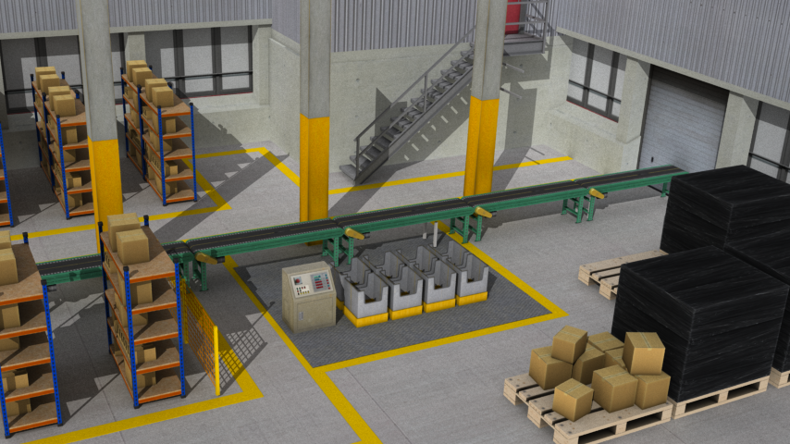
benzene_gazebo/models/workcell/materials/textures/WorkCell_Render.png
