attu0/benzene/benzene_gazebo/models/opil_warehouse/meshes/opil_warehouse.STL

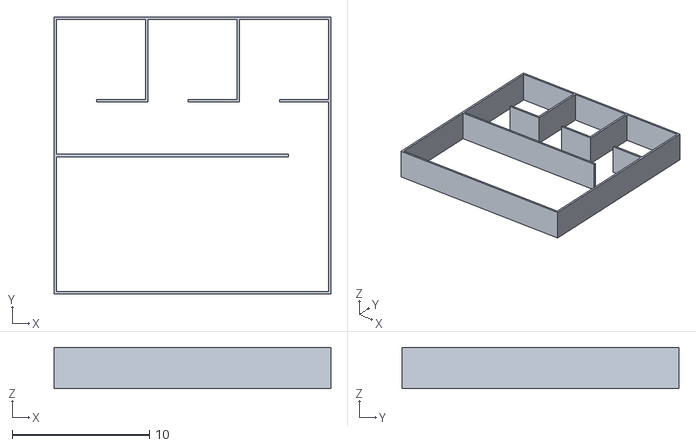
[picture p193: CAD file, 2026-09-20]
benzene_gazebo/models/opil_warehouse/meshes/opil_warehouse.STL
20.2 x 20.2 x 3.00
