attu0/benzene/benzene_gazebo/models/others/meshes/apple_collision.stl

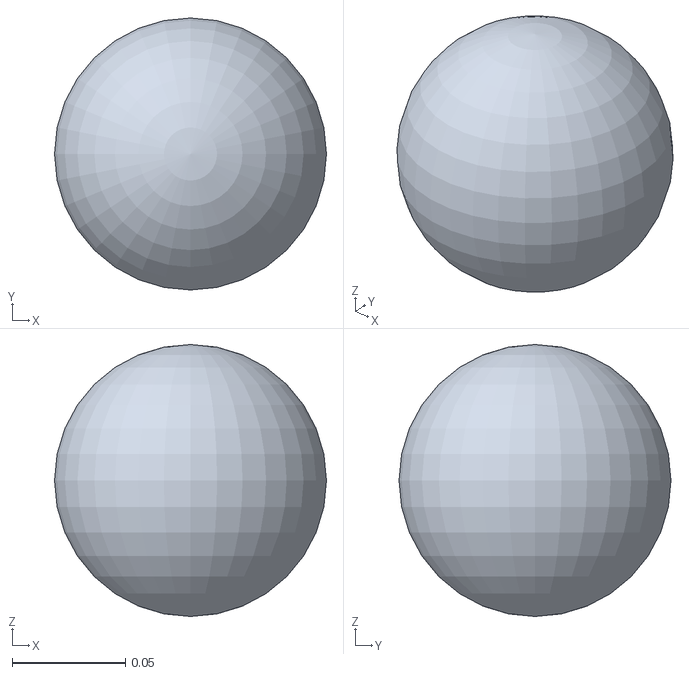
[picture p194: CAD file, 2026-09-20]
benzene_gazebo/models/others/meshes/apple_collision.stl
0.12 x 0.12 x 0.12
