attu0/benzene/benzene_gazebo/models/Surfaces/meshes/wall_1.obj

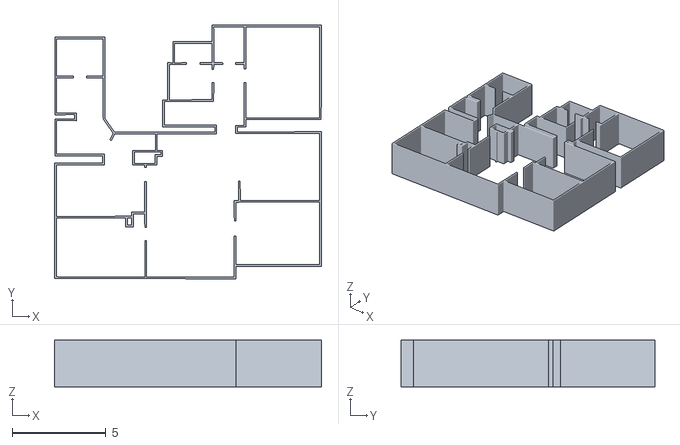
[picture p195: CAD file, 2026-09-14]
benzene_gazebo/models/Surfaces/meshes/wall_1.obj
14.3 x 13.6 x 2.50
