attu0/benzene/benzene_gazebo/models/Tv/meshes/tv.stl

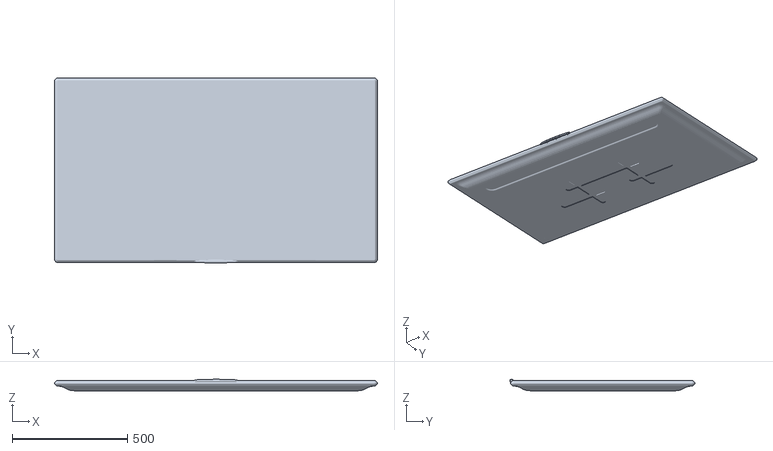
[picture p196: CAD file, 2026-09-14]
benzene_gazebo/models/Tv/meshes/tv.stl
1400.0 x 801.9 x 50.0
