attu0/benzene/assets/laser_cut/middle1.dxf

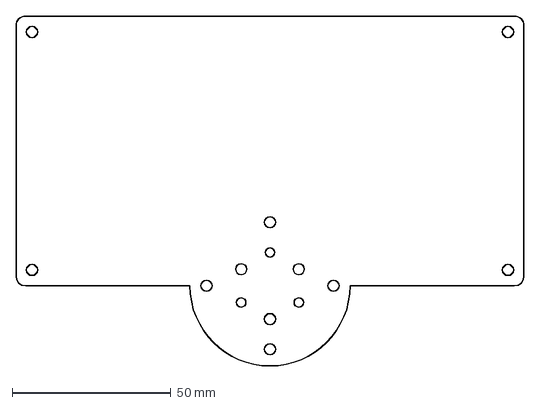
[picture p197: CAD file, 2026-10-04]
assets/laser_cut/middle1.dxf
160.0 x 110.2 mm
