attu0/benzene/benzene_description/meshes/rplidar/lidar.stl

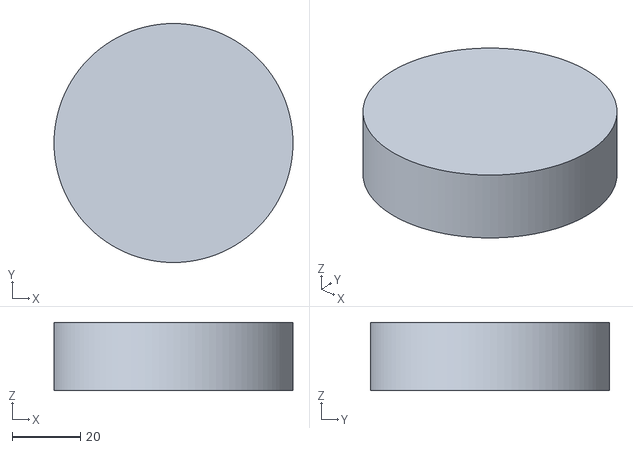
[picture p198: CAD file, 2026-08-12]
benzene_description/meshes/rplidar/lidar.stl
70.0 x 70.0 x 20.0
