attu0/benzene/benzene_description/meshes/v3/visual/caster_link.stl

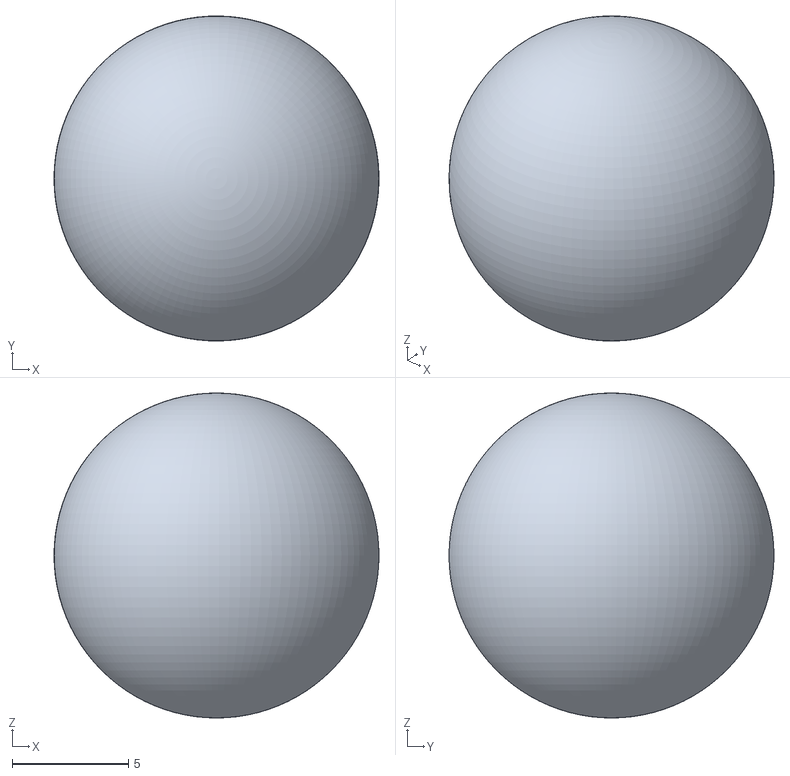
[picture p199: CAD file, 2026-09-08]
benzene_description/meshes/v3/visual/caster_link.stl
14.0 x 14.0 x 14.0
