attu0/benzene/benzene_gazebo/models/cafe_counter/meshes/cafe_counter.obj

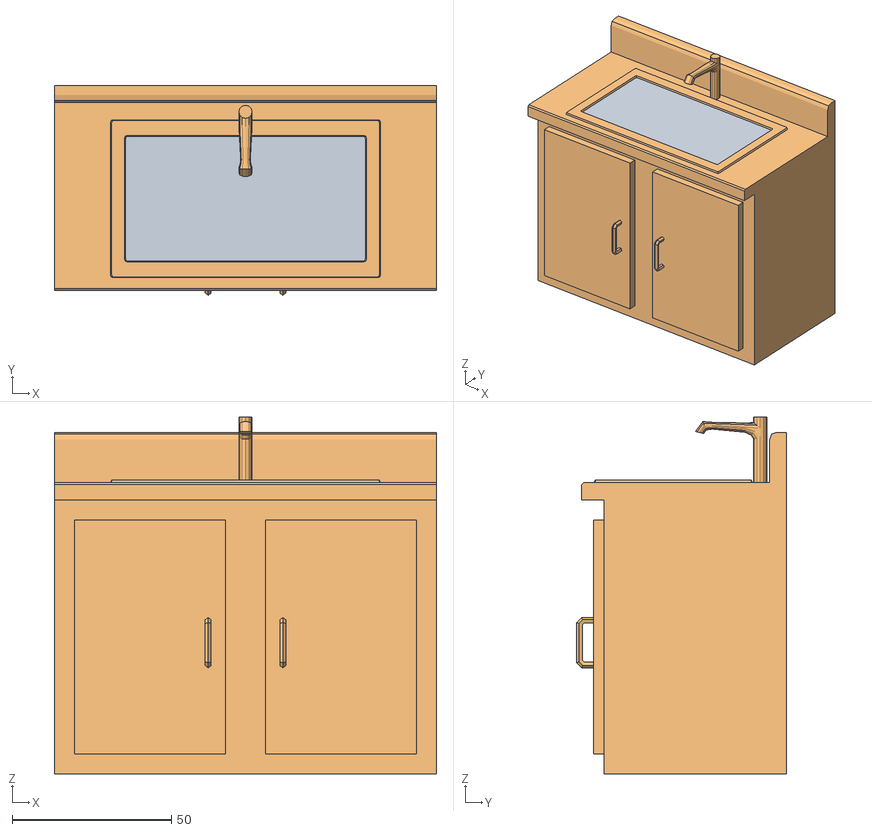
[picture p200: CAD file, 2026-08-16]
benzene_gazebo/models/cafe_counter/meshes/cafe_counter.obj
120.0 x 65.8 x 112.0
cafe_counter
cafe_counter_sink
