attu0/benzene/benzene_gazebo/models/others/meshes/apple.stl

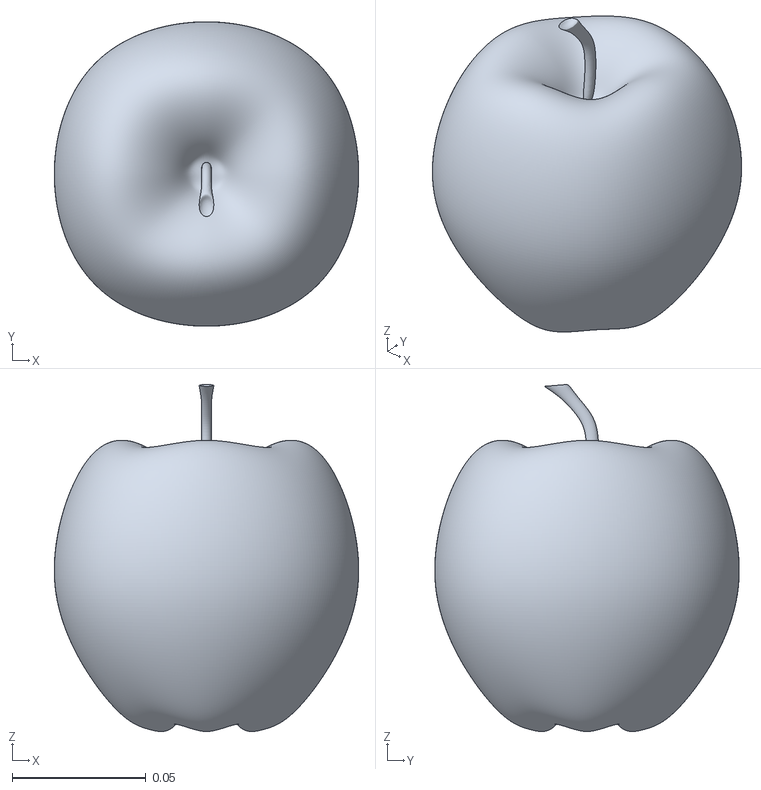
[picture p201: CAD file, 2026-09-20]
benzene_gazebo/models/others/meshes/apple.stl
0.114 x 0.114 x 0.13
