attu0/benzene/benzene_gazebo/models/Surfaces/meshes/floor_7.obj

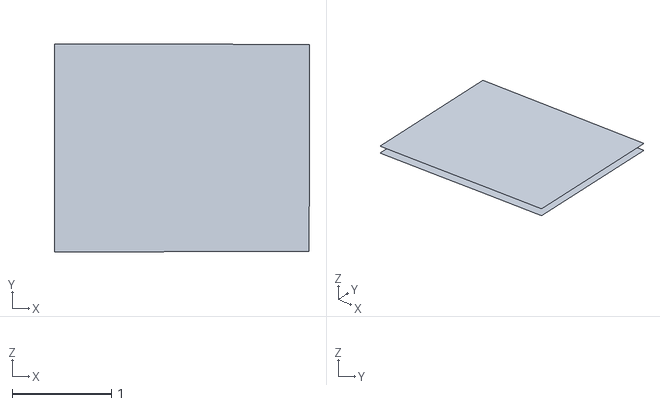
[picture p202: CAD file, 2026-09-14]
benzene_gazebo/models/Surfaces/meshes/floor_7.obj
2.57 x 2.10 x 0.1
