attu0/benzene/assets/laser_cut/middle2.dxf

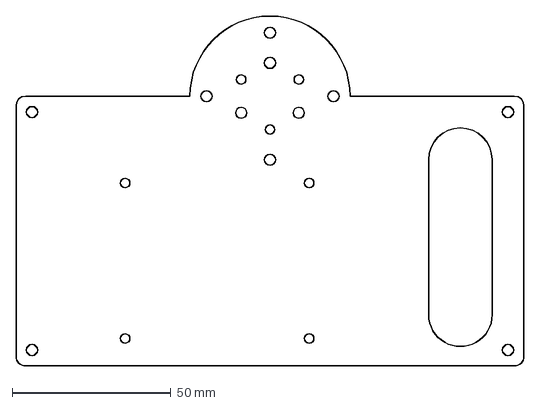
[picture p203: CAD file, 2026-10-04]
assets/laser_cut/middle2.dxf
160.0 x 110.2 mm
