attu0/benzene/benzene_description/meshes/v3/visual/wheel_link.stl

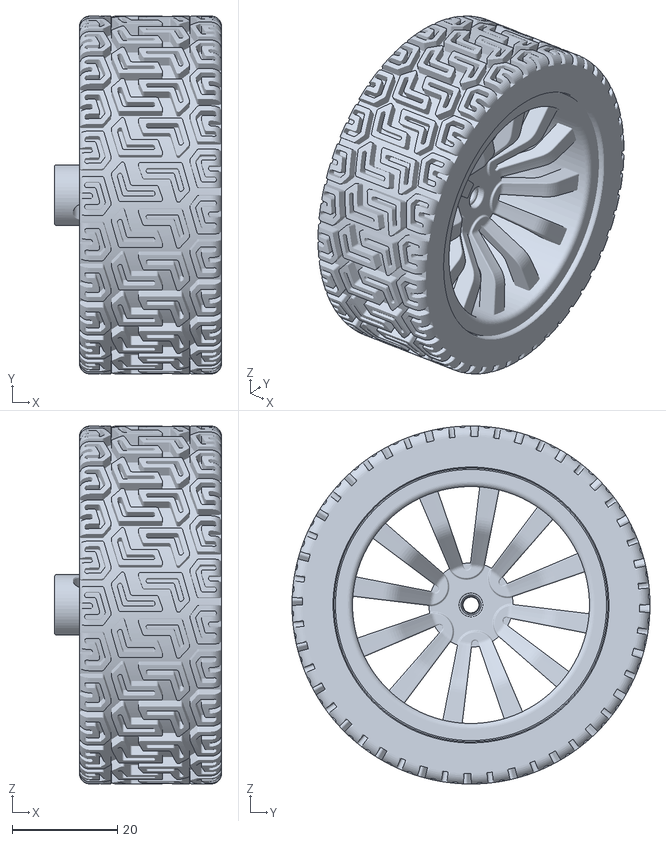
[picture p204: CAD file, 2026-09-08]
benzene_description/meshes/v3/visual/wheel_link.stl
31.8 x 68.0 x 68.0
