attu0/benzene/benzene_gazebo/models/cafe_counter/meshes/counter_sink.obj

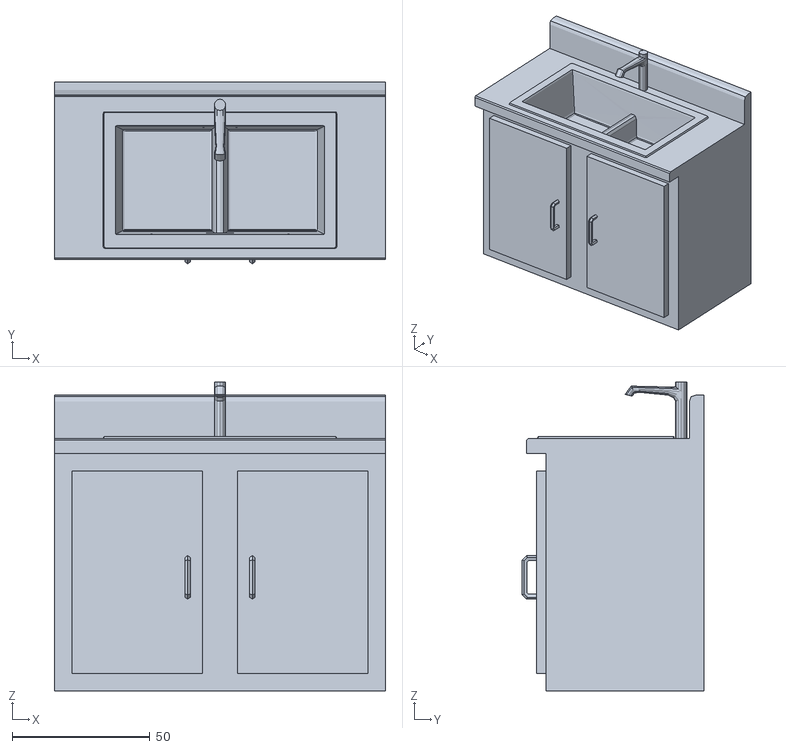
[picture p205: CAD file, 2026-08-16]
benzene_gazebo/models/cafe_counter/meshes/counter_sink.obj
120.0 x 65.8 x 112.0
