attu0/benzene/benzene_gazebo/models/others/meshes/fruit_box.stl

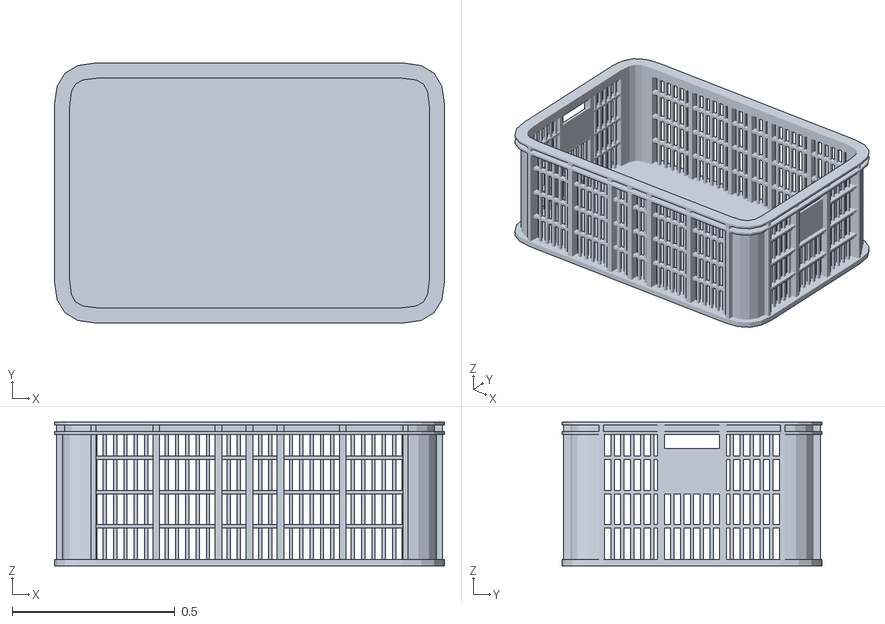
[picture p206: CAD file, 2026-09-20]
benzene_gazebo/models/others/meshes/fruit_box.stl
1.20 x 0.8 x 0.443
