attu0/benzene/benzene_gazebo/models/Surfaces/meshes/floor_8.obj

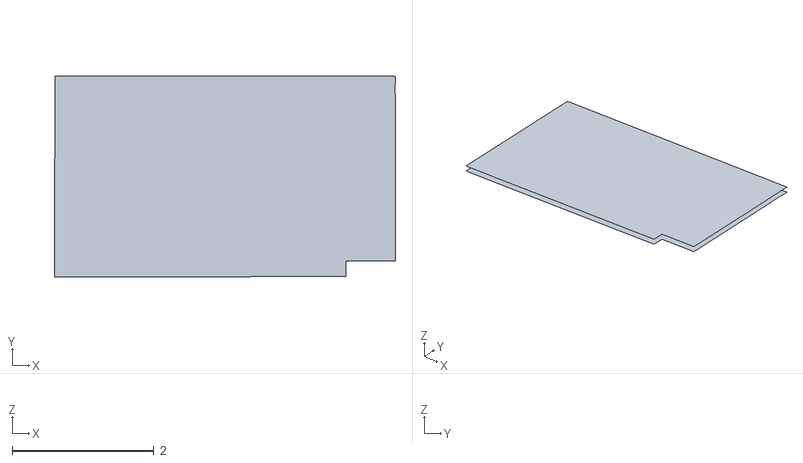
[picture p207: CAD file, 2026-09-14]
benzene_gazebo/models/Surfaces/meshes/floor_8.obj
4.81 x 2.84 x 0.1
