attu0/benzene/assets/laser_cut/cross.dxf

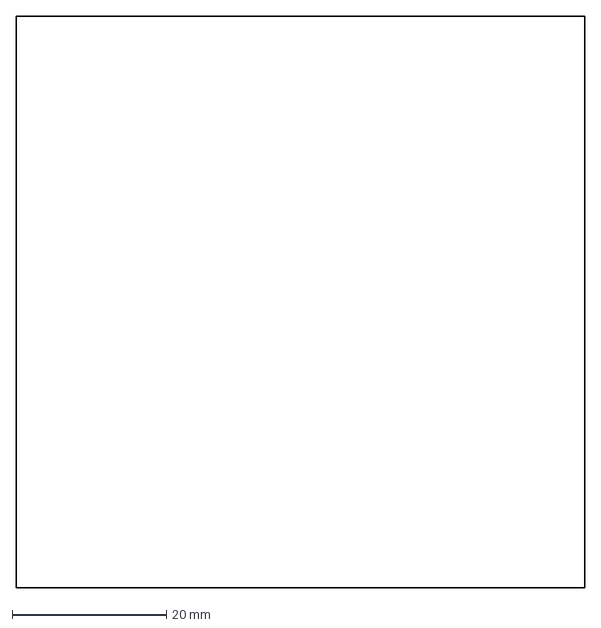
[picture p208: CAD file, 2026-10-04]
assets/laser_cut/cross.dxf
73.6 x 74.0 mm
