attu0/benzene/benzene_description/meshes/v3/visual/uss_link.stl

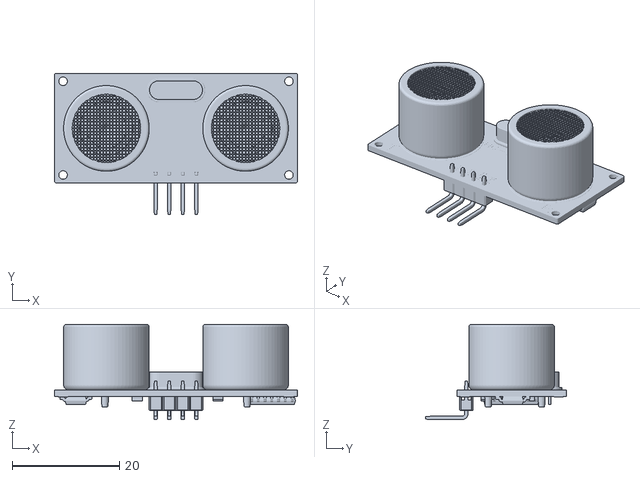
[picture p209: CAD file, 2026-09-08]
benzene_description/meshes/v3/visual/uss_link.stl
45.4 x 26.4 x 17.8
