attu0/benzene/benzene_gazebo/models/Surfaces/meshes/floor_14.obj

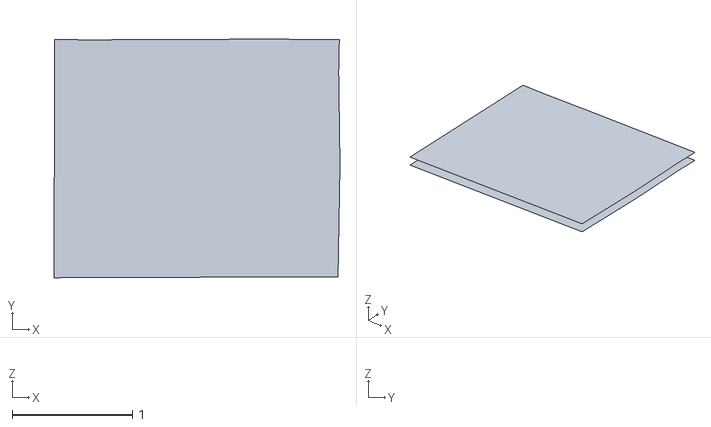
[picture p210: CAD file, 2026-09-14]
benzene_gazebo/models/Surfaces/meshes/floor_14.obj
2.38 x 1.98 x 0.1
