attu0/benzene/assets/laser_cut/uss.dxf

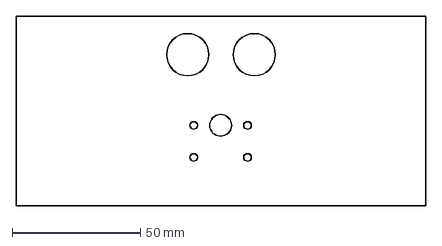
[picture p211: CAD file, 2026-10-04]
assets/laser_cut/uss.dxf
160.0 x 74.0 mm
