attu0/benzene/benzene_description/meshes/v3/visual/base_link.stl

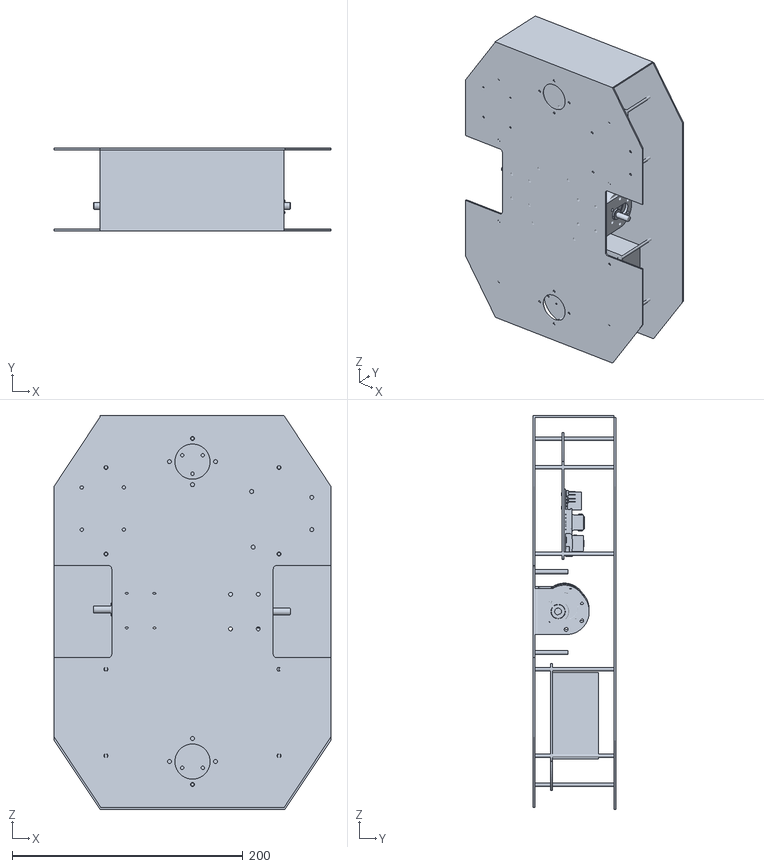
[picture p212: CAD file, 2026-09-08]
benzene_description/meshes/v3/visual/base_link.stl
240.0 x 71.6 x 341.6
