attu0/benzene/benzene_gazebo/models/Surfaces/meshes/floor_12.obj

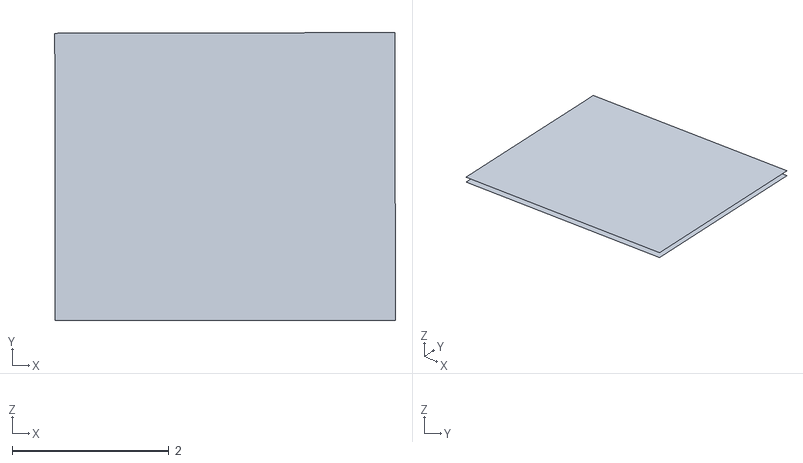
[picture p213: CAD file, 2026-09-14]
benzene_gazebo/models/Surfaces/meshes/floor_12.obj
4.35 x 3.67 x 0.1
