attu0/benzene/assets/laser_cut/lower.dxf

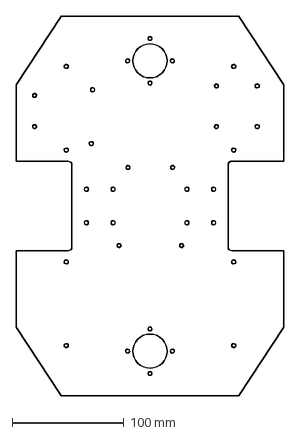
[picture p214: CAD file, 2026-10-04]
assets/laser_cut/lower.dxf
240.0 x 340.0 mm
