attu0/benzene/benzene_gazebo/models/Surfaces/meshes/floor_2.obj

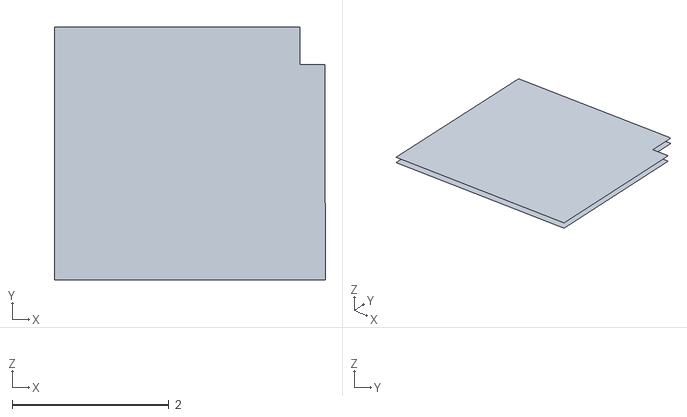
[picture p215: CAD file, 2026-09-14]
benzene_gazebo/models/Surfaces/meshes/floor_2.obj
3.46 x 3.24 x 0.1
