attu0/benzene/assets/laser_cut/side.dxf

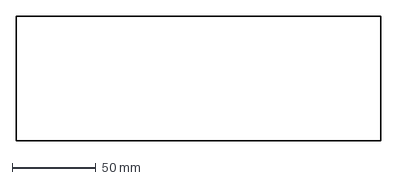
[picture p216: CAD file, 2026-10-04]
assets/laser_cut/side.dxf
217.3 x 74.0 mm
