attu0/benzene/benzene_description/meshes/v3/visual/camera.stl

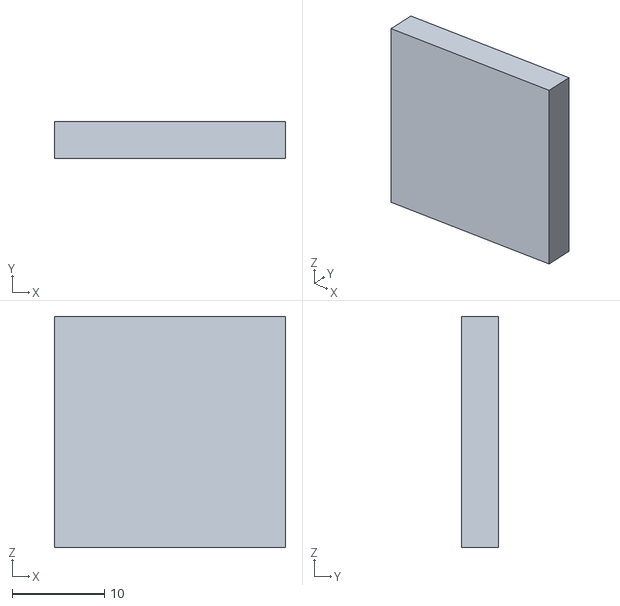
[picture p217: CAD file, 2026-08-12]
benzene_description/meshes/v3/visual/camera.stl
25.0 x 4.00 x 25.0
