attu0/benzene/benzene_gazebo/models/Surfaces/meshes/floor_9.obj

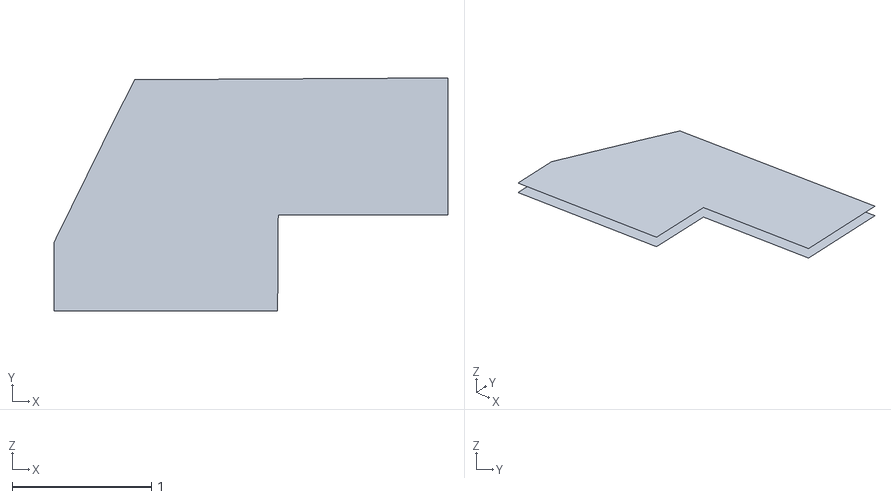
[picture p218: CAD file, 2026-09-14]
benzene_gazebo/models/Surfaces/meshes/floor_9.obj
2.83 x 1.67 x 0.1
