attu0/benzene/assets/laser_cut/switch.dxf

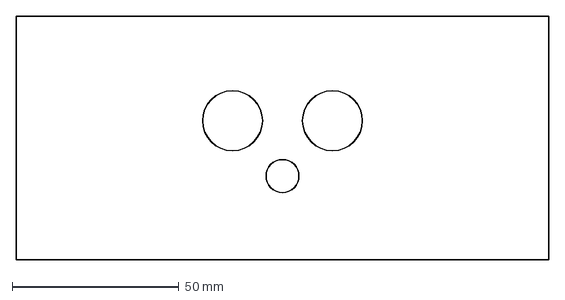
[picture p219: CAD file, 2026-10-04]
assets/laser_cut/switch.dxf
160.0 x 73.2 mm
