attu0/benzene/benzene_description/meshes/v3/visual/chassis.stl

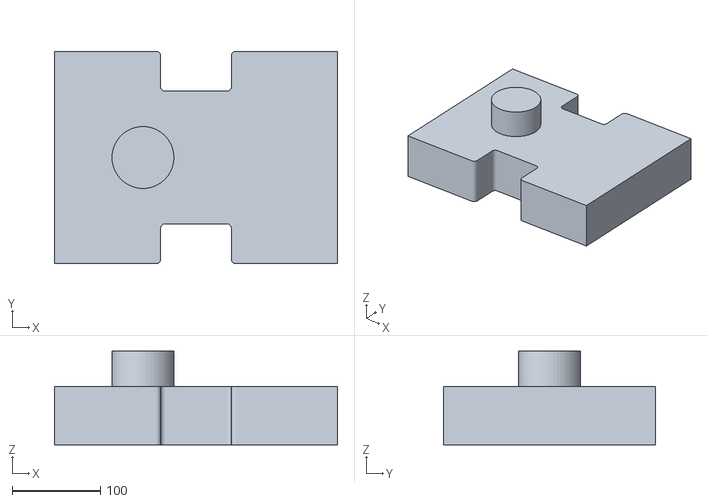
[picture p220: CAD file, 2026-08-12]
benzene_description/meshes/v3/visual/chassis.stl
320.0 x 240.0 x 106.0
