attu0/benzene/benzene_gazebo/models/Surfaces/meshes/floor_1.obj

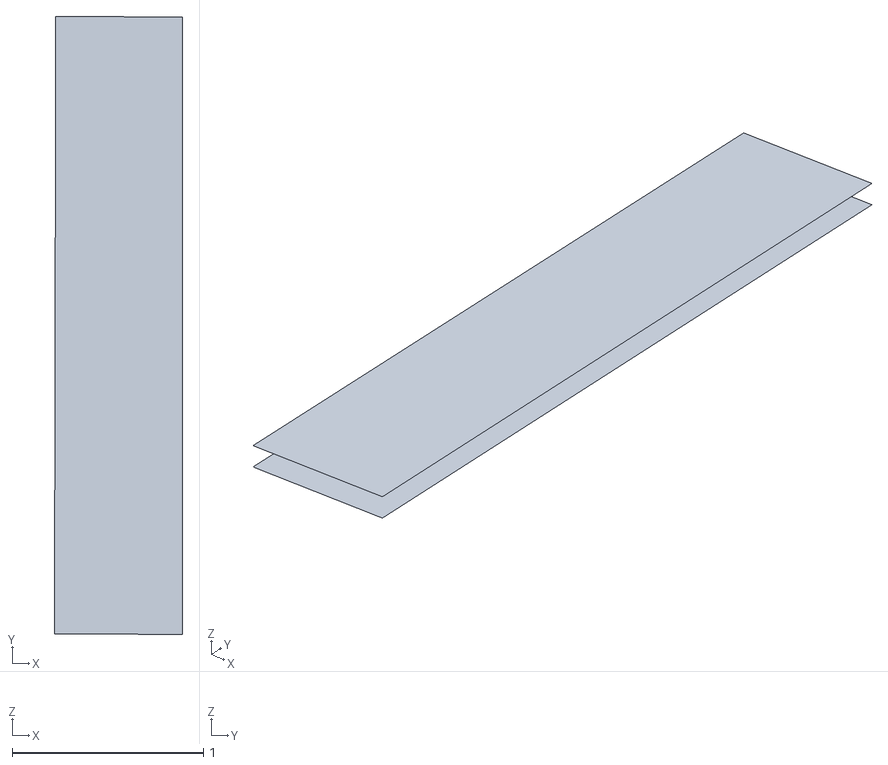
[picture p221: CAD file, 2026-09-14]
benzene_gazebo/models/Surfaces/meshes/floor_1.obj
0.67 x 3.23 x 0.1
