attu0/benzene/benzene_gazebo/models/Surfaces/meshes/floor_3.obj

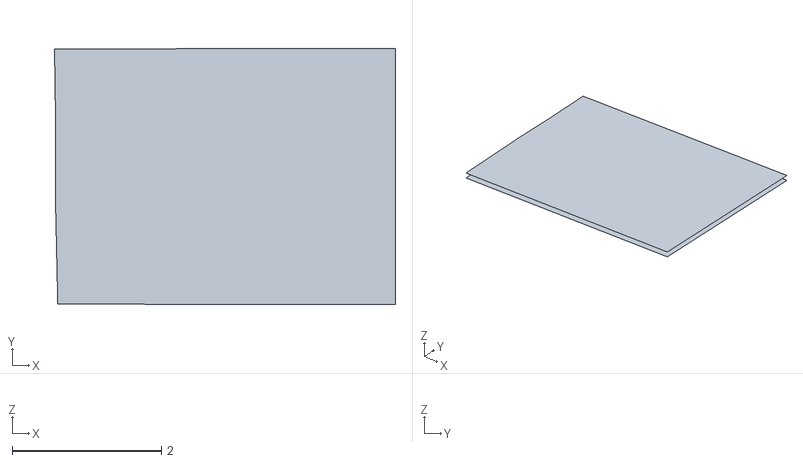
[picture p222: CAD file, 2026-09-14]
benzene_gazebo/models/Surfaces/meshes/floor_3.obj
4.57 x 3.44 x 0.1
