attu0/benzene/benzene_gazebo/models/Surfaces/meshes/floor_10.obj

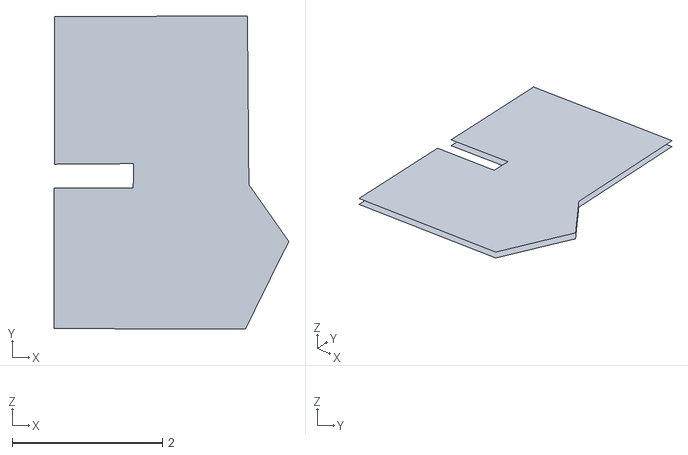
[picture p223: CAD file, 2026-09-14]
benzene_gazebo/models/Surfaces/meshes/floor_10.obj
3.12 x 4.16 x 0.1
