attu0/benzene/benzene_gazebo/models/Surfaces/meshes/floor_5.obj

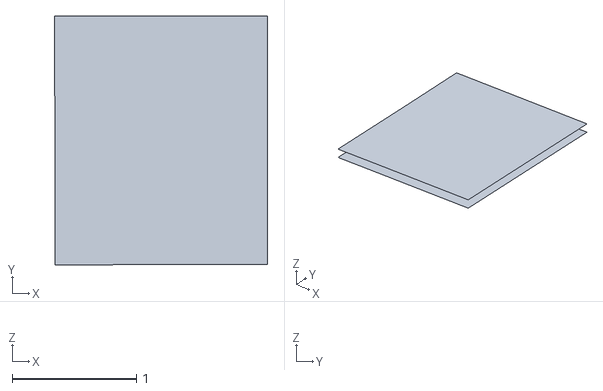
[picture p224: CAD file, 2026-09-14]
benzene_gazebo/models/Surfaces/meshes/floor_5.obj
1.72 x 2.01 x 0.1
