attu0/benzene/benzene_gazebo/models/Surfaces/meshes/floor_4.obj

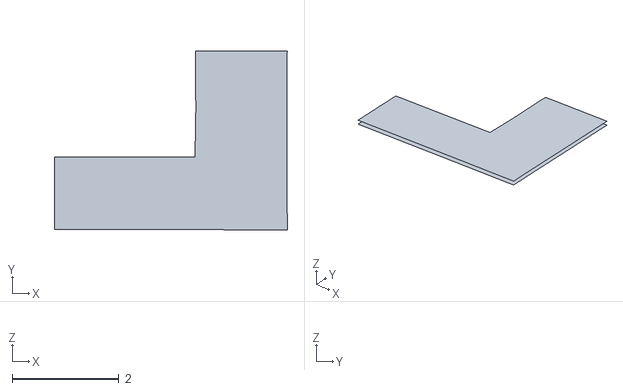
[picture p225: CAD file, 2026-09-14]
benzene_gazebo/models/Surfaces/meshes/floor_4.obj
4.36 x 3.35 x 0.1
