attu0/benzene/benzene_gazebo/models/Surfaces/meshes/floor_6.obj

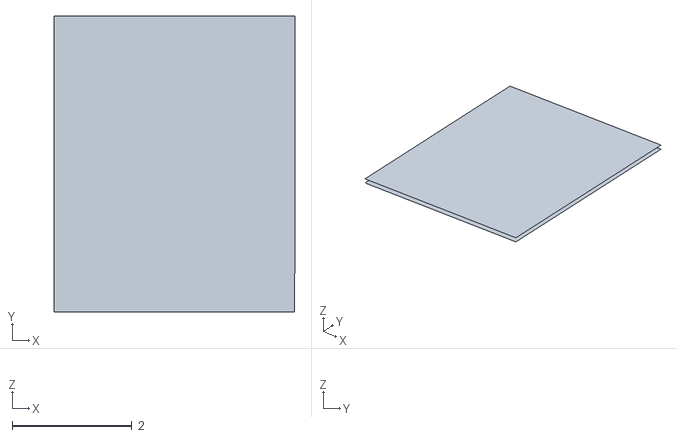
[picture p226: CAD file, 2026-09-14]
benzene_gazebo/models/Surfaces/meshes/floor_6.obj
4.03 x 4.95 x 0.1
