attu0/benzene/benzene_gazebo/models/Surfaces/meshes/floor_13.obj

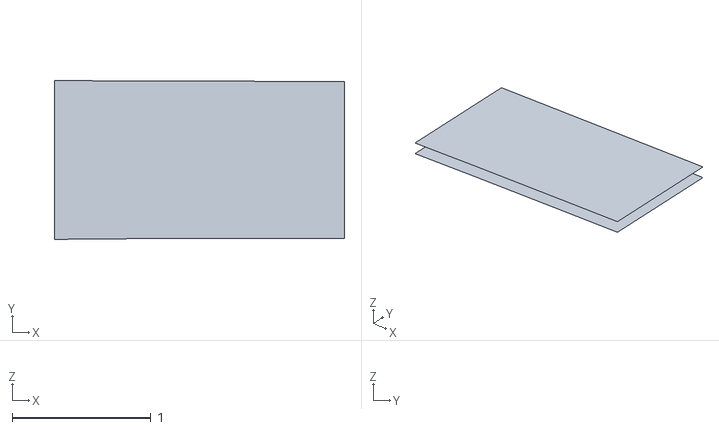
[picture p227: CAD file, 2026-09-14]
benzene_gazebo/models/Surfaces/meshes/floor_13.obj
2.09 x 1.14 x 0.1
