attu0/benzene/benzene_gazebo/models/Surfaces/meshes/floor_11.obj

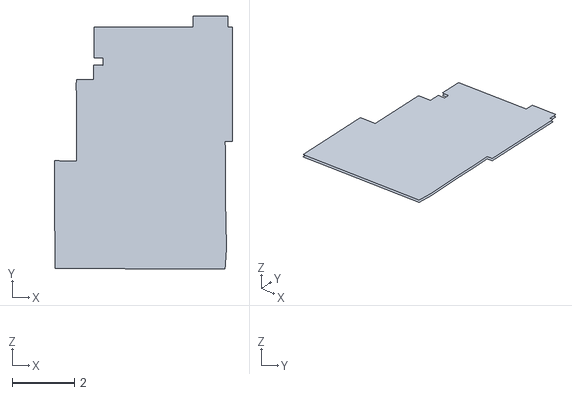
[picture p228: CAD file, 2026-09-14]
benzene_gazebo/models/Surfaces/meshes/floor_11.obj
5.71 x 8.11 x 0.1
