attu0/benzene/benzene_gazebo/models/Surfaces/meshes/wall_2.obj

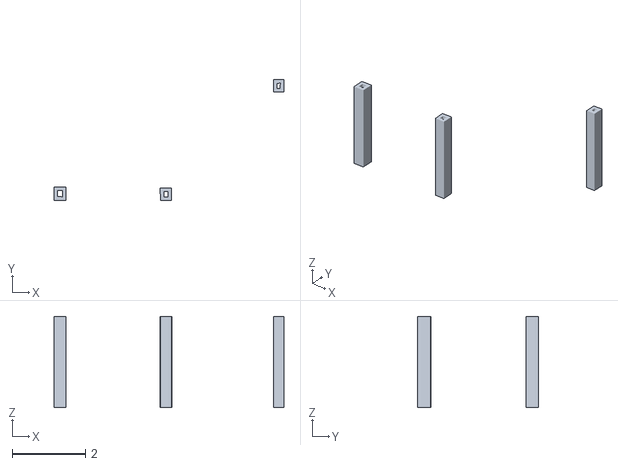
[picture p229: CAD file, 2026-09-14]
benzene_gazebo/models/Surfaces/meshes/wall_2.obj
6.30 x 3.32 x 2.50
