attu0/benzene/assets/images/docker/build.png

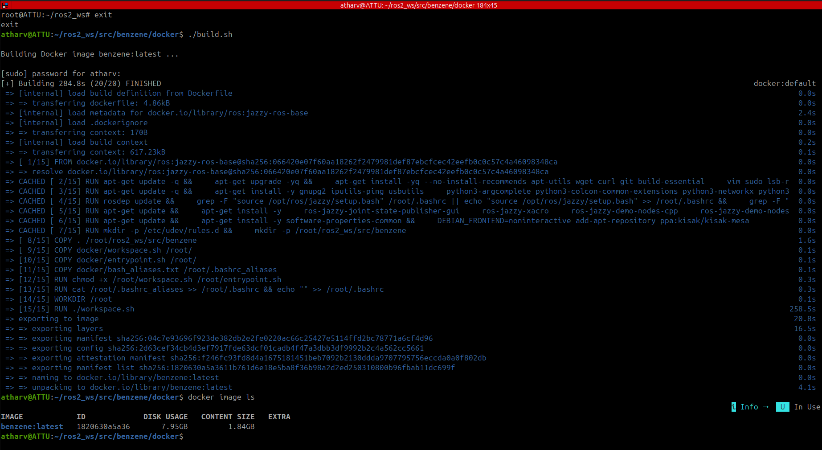
assets/images/docker/build.png
