attu0/benzene/benzene_arduino/ros_arduino_bridge_2motor_v3_pio/include/sensors.h

/* Functions for various sensor types */

#ifndef SENSORS_H
#define SENSORS_H

#include <Arduino.h>

static float microsecondsToCm(long microseconds)
{
  // The speed of sound is 340 m/s or 29 microseconds per cm.
  // The ping travels out and back, so to find the distance of the
  // object we take half of the distance travelled.
  return microseconds / 29 / 2;
}

static long Ping(int pin) {
  long duration, range;

  // The PING))) is triggered by a HIGH pulse of 2 or more microseconds.
  // Give a short LOW pulse beforehand to ensure a clean HIGH pulse:
  pinMode(pin, OUTPUT);
  digitalWrite(pin, LOW);
  delayMicroseconds(2);
  digitalWrite(pin, HIGH);
  delayMicroseconds(5);
  digitalWrite(pin, LOW);

  // The same pin is used to read the signal from the PING))): a HIGH
  // pulse whose duration is the time (in microseconds) from the sending
  // of the ping to the reception of its echo off of an object.
  pinMode(pin, INPUT);
  duration = pulseIn(pin, HIGH);

  // convert the time into centimetres
  range = microsecondsToCm(duration);

  return range;
}

#endif
