attu0/benzene/benzene_gazebo/models/cheezit_big_original/meshes/cheez_tex_0.jpg

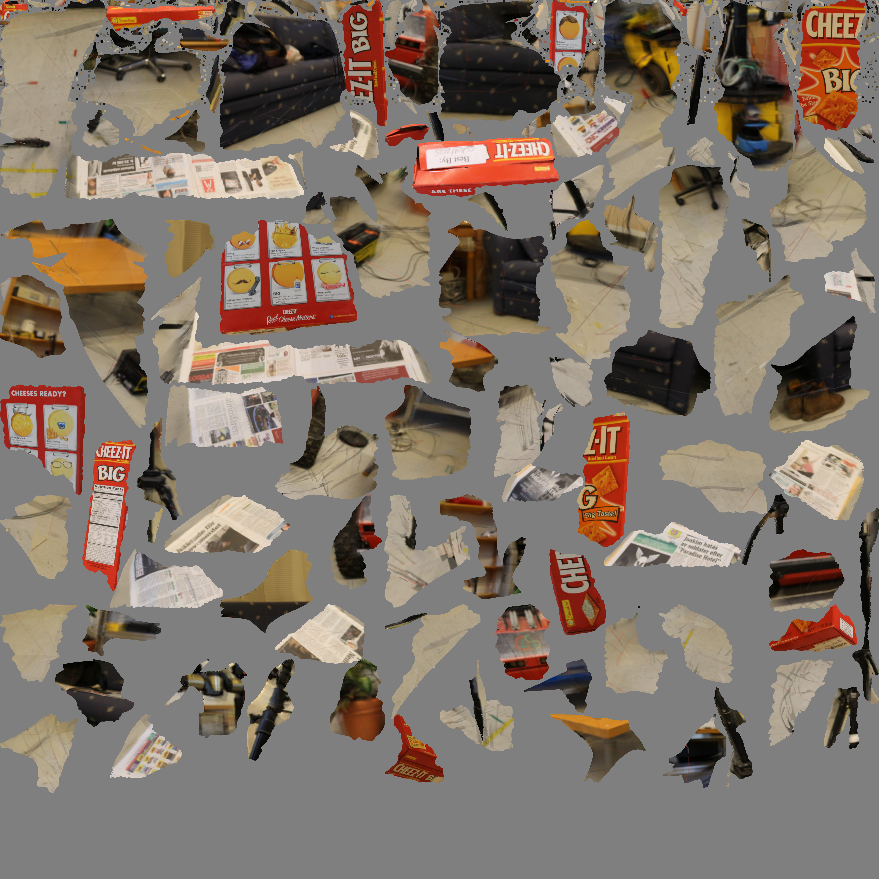
benzene_gazebo/models/cheezit_big_original/meshes/cheez_tex_0.jpg
